OSVR/OSVR-HDK/HDK Ver. 2.0/misc/GF-S140149--Cable B  Rev_3.0.pdf

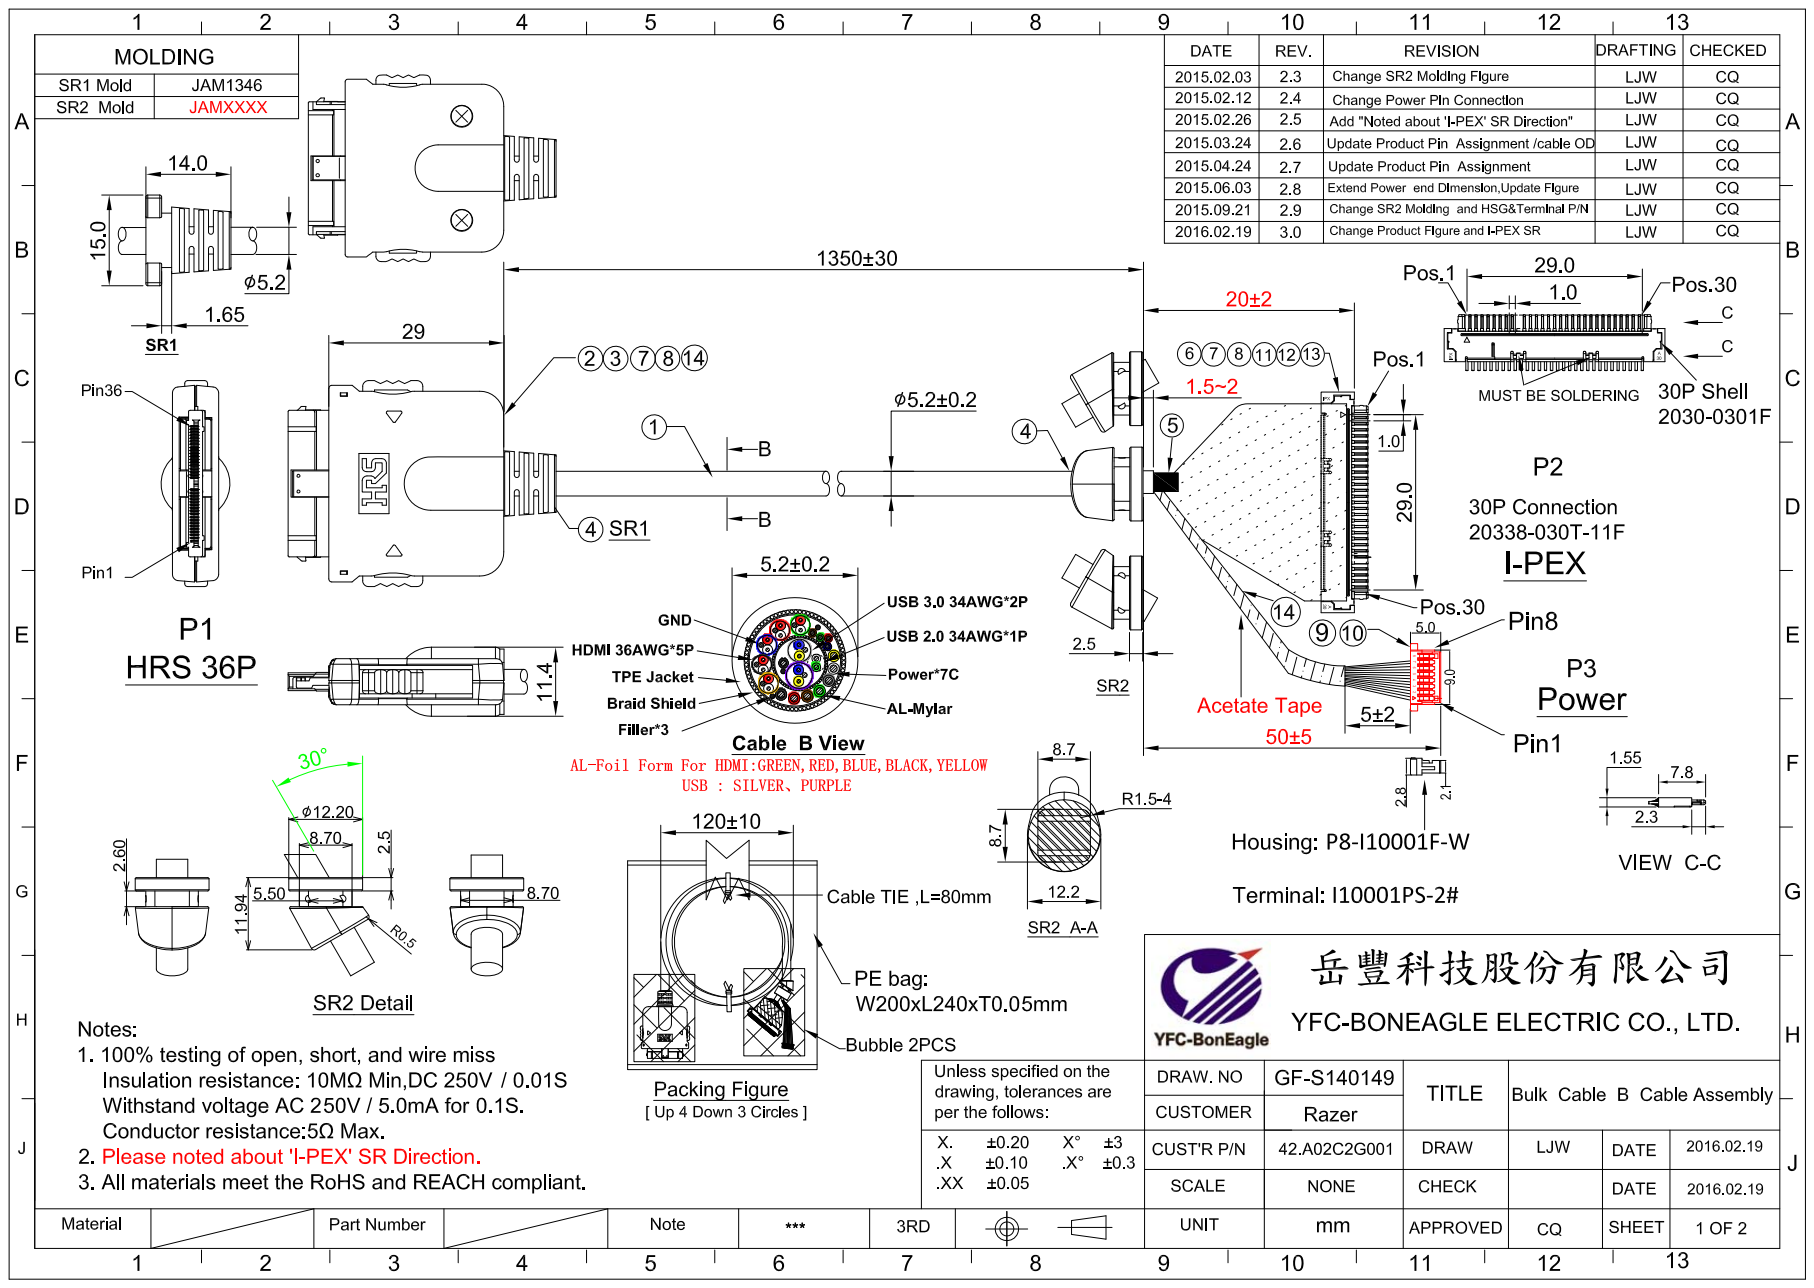
[picture p48: page 1]

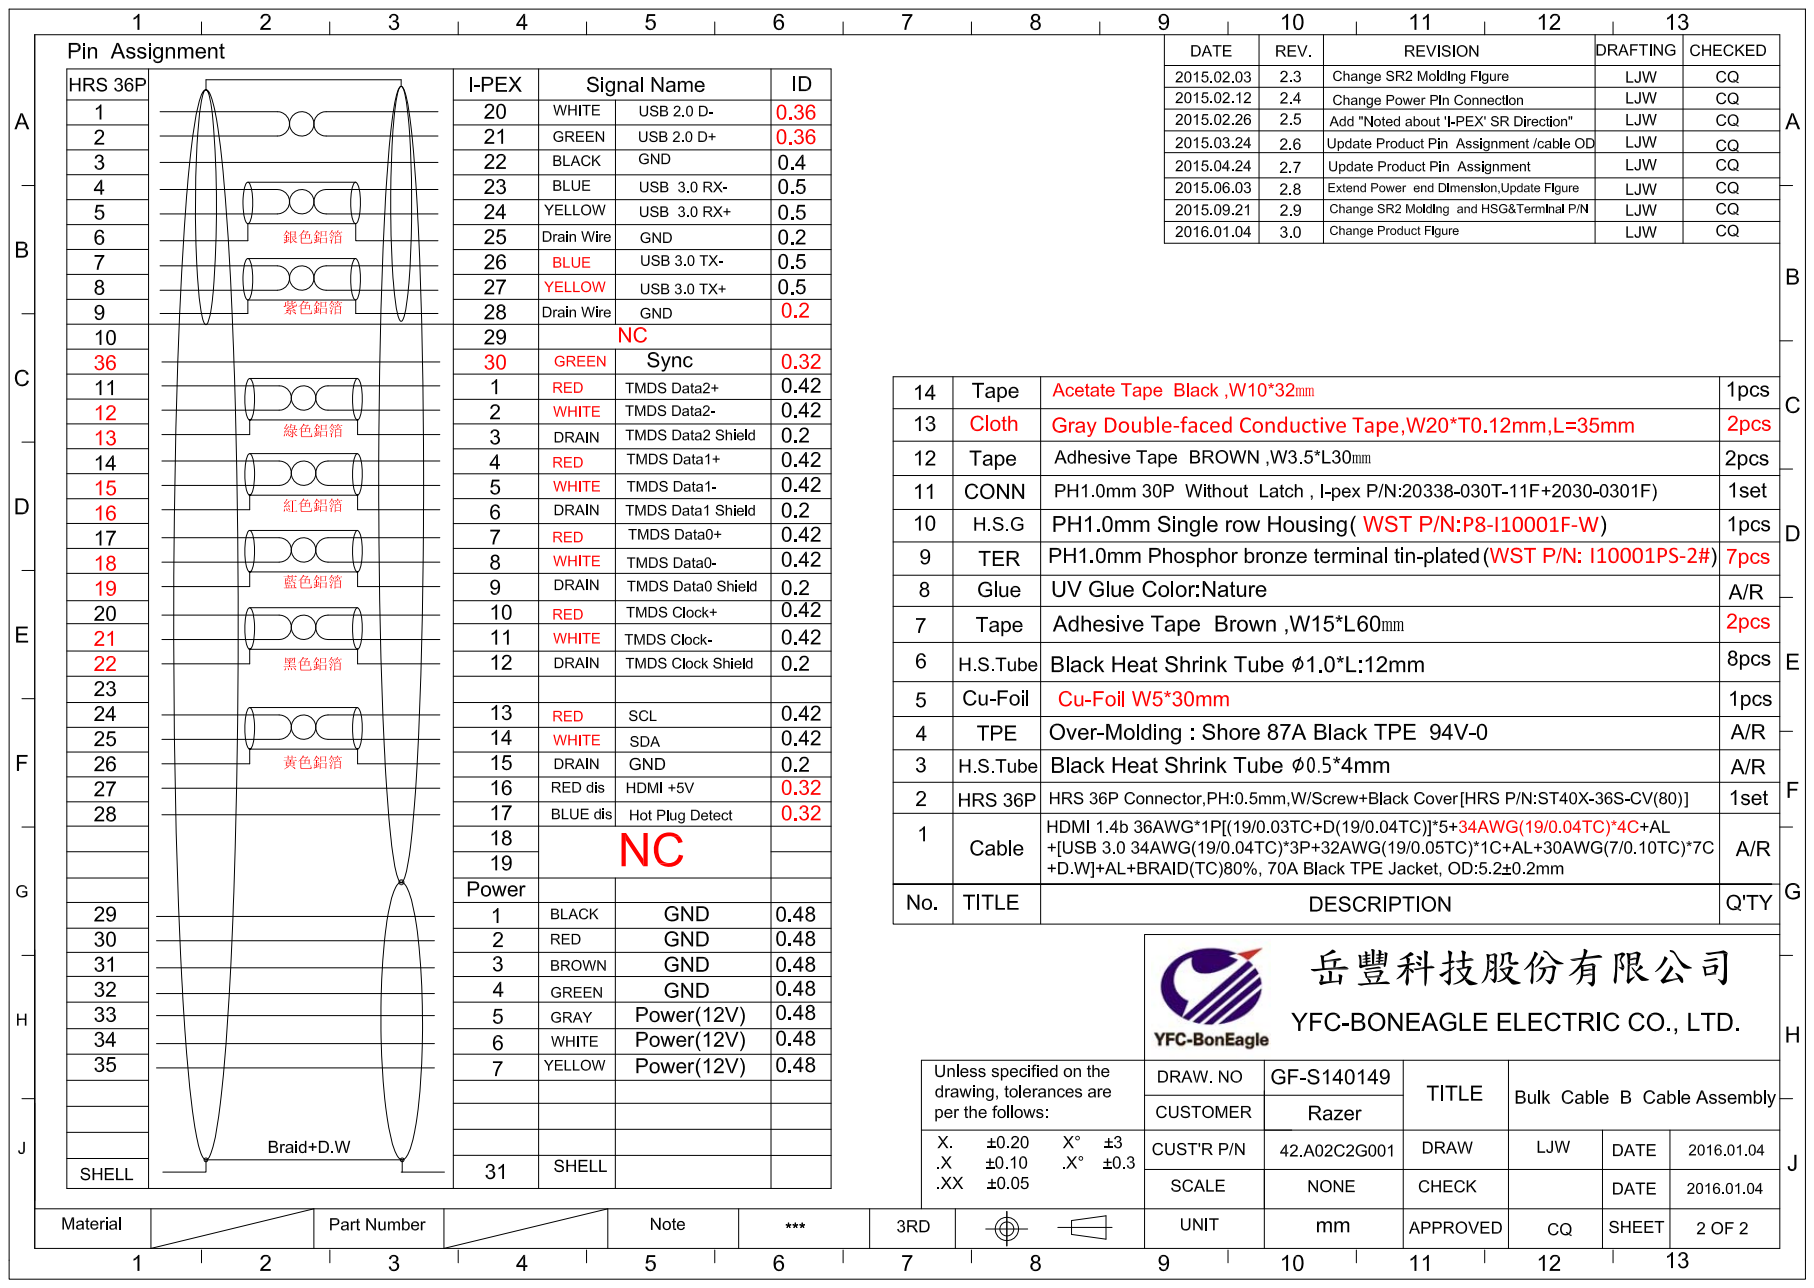
[picture p49: page 2]
