OSVR/OSVR-HDK/HDK Ver. 2.0/misc/GF-S150066--IR Cable_REV1.6.pdf

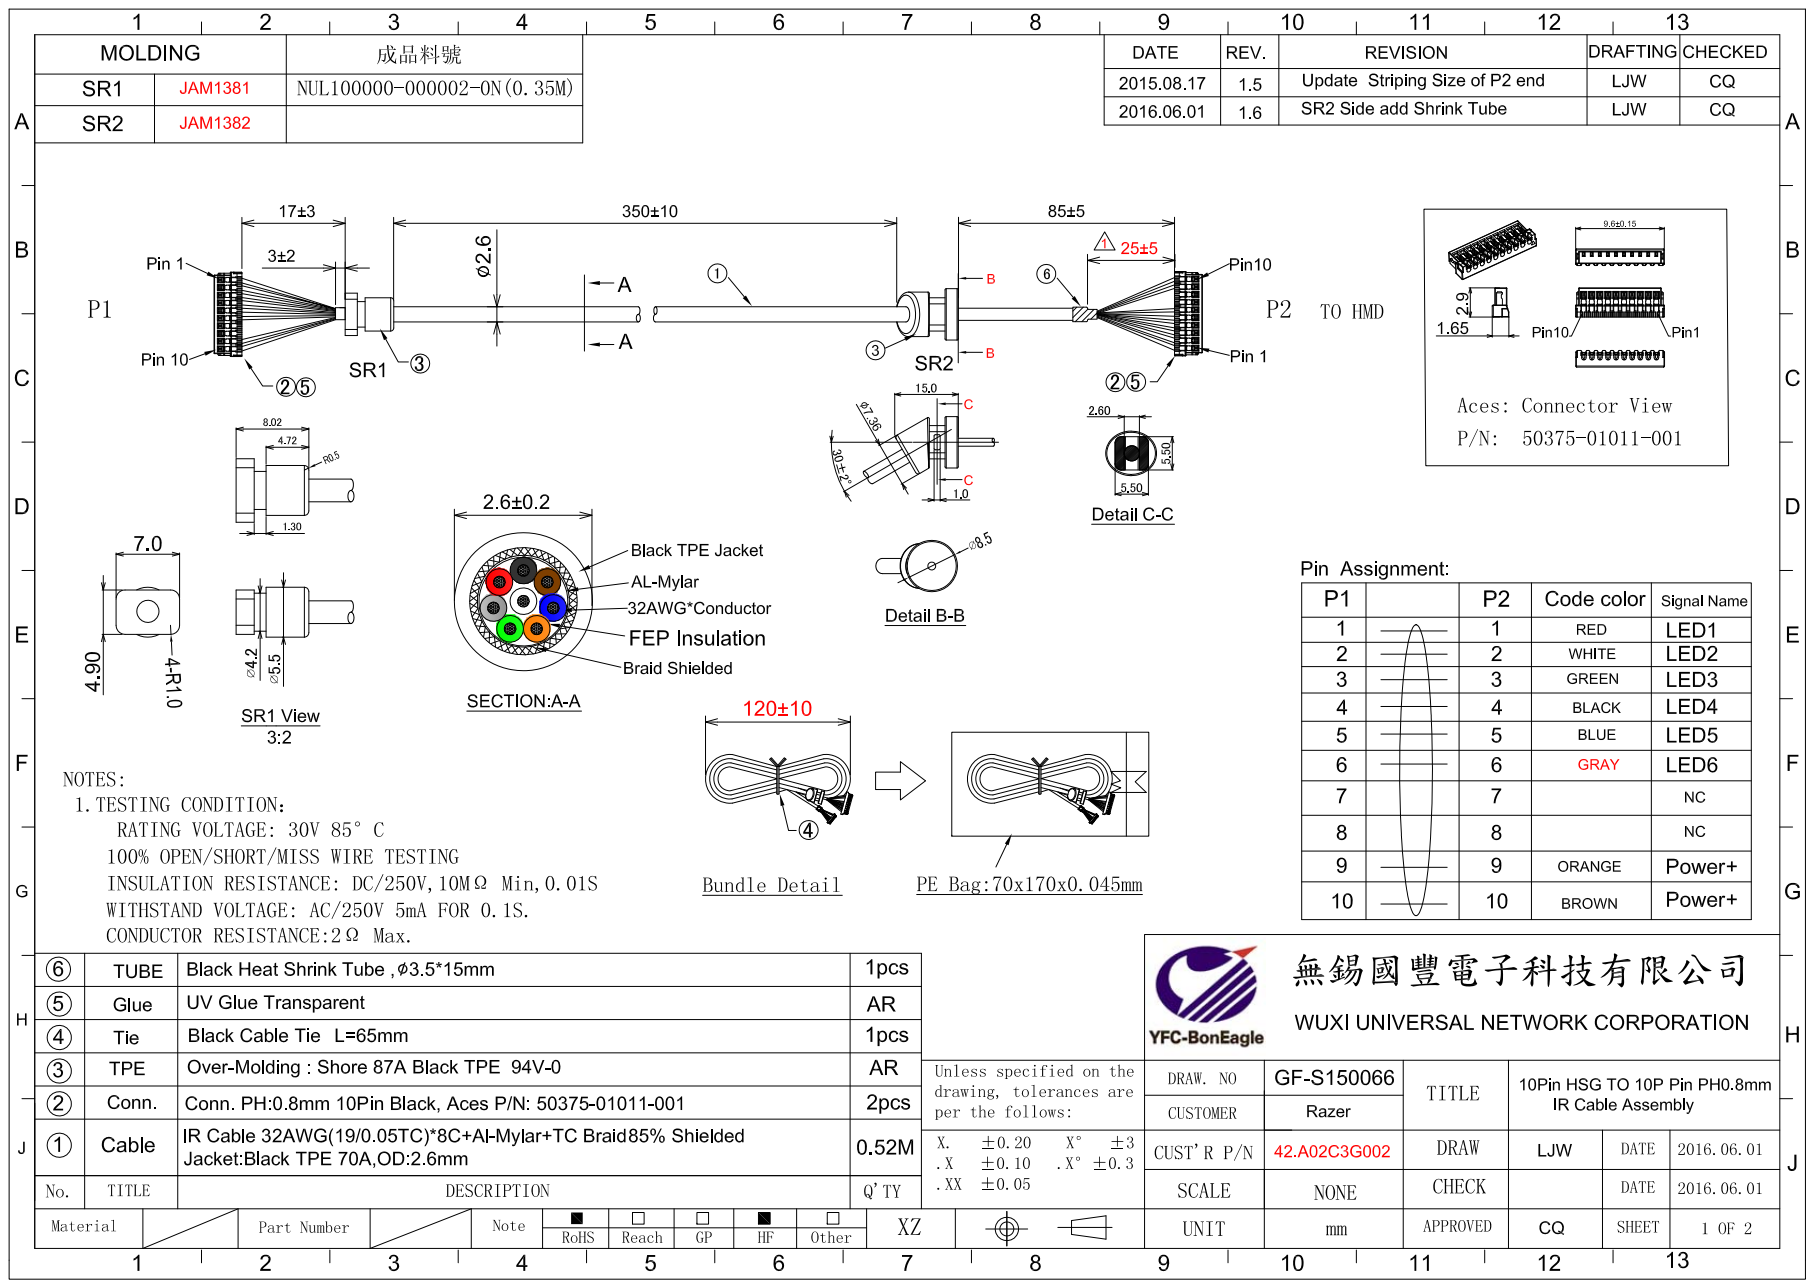
[picture p50: page 1]

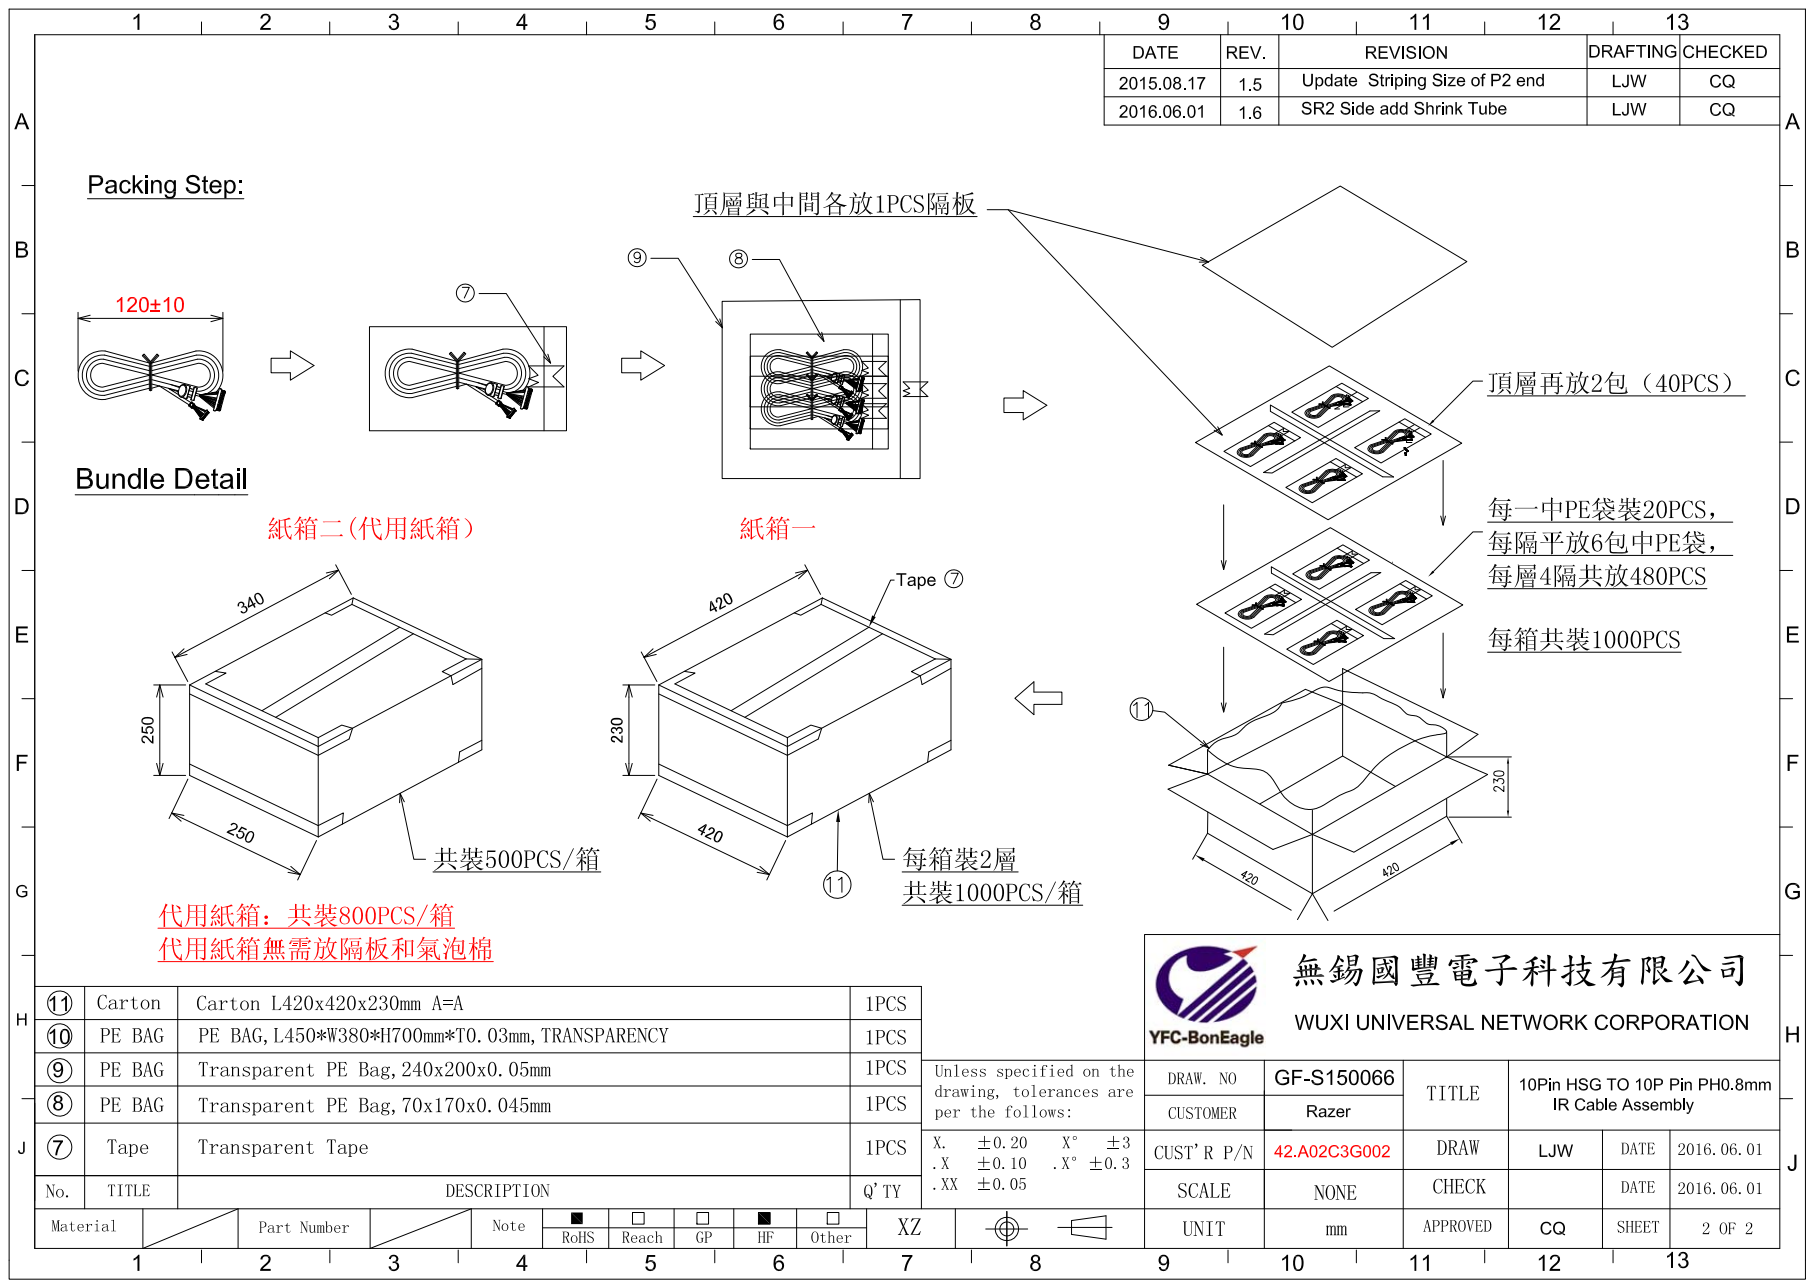
[picture p51: page 2]
