OSVR/OSVR-HDK/HDK Ver. 2.0/misc/GF-S150127---USB 2.0 AM-MICRO BM _A1.pdf

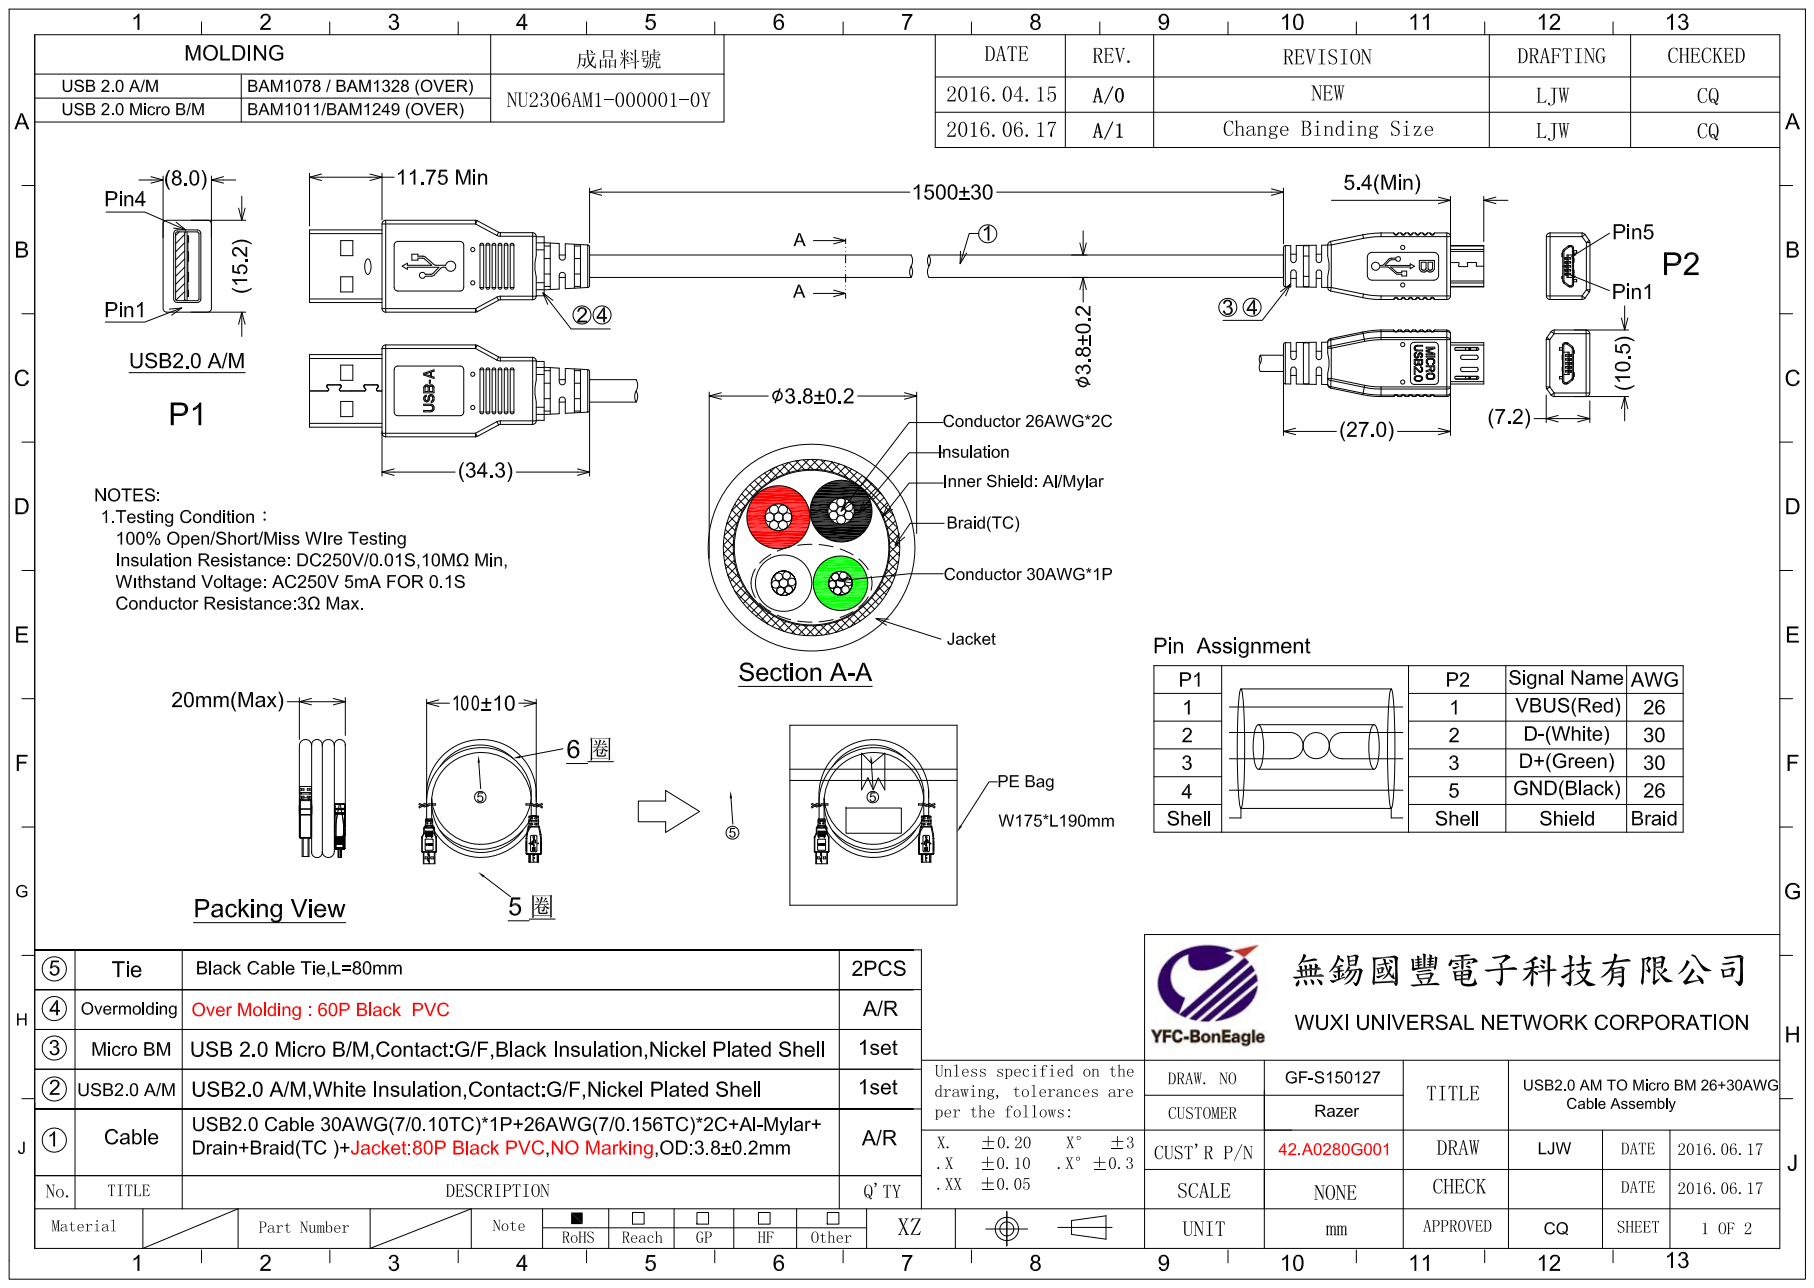
[picture p52: page 1]

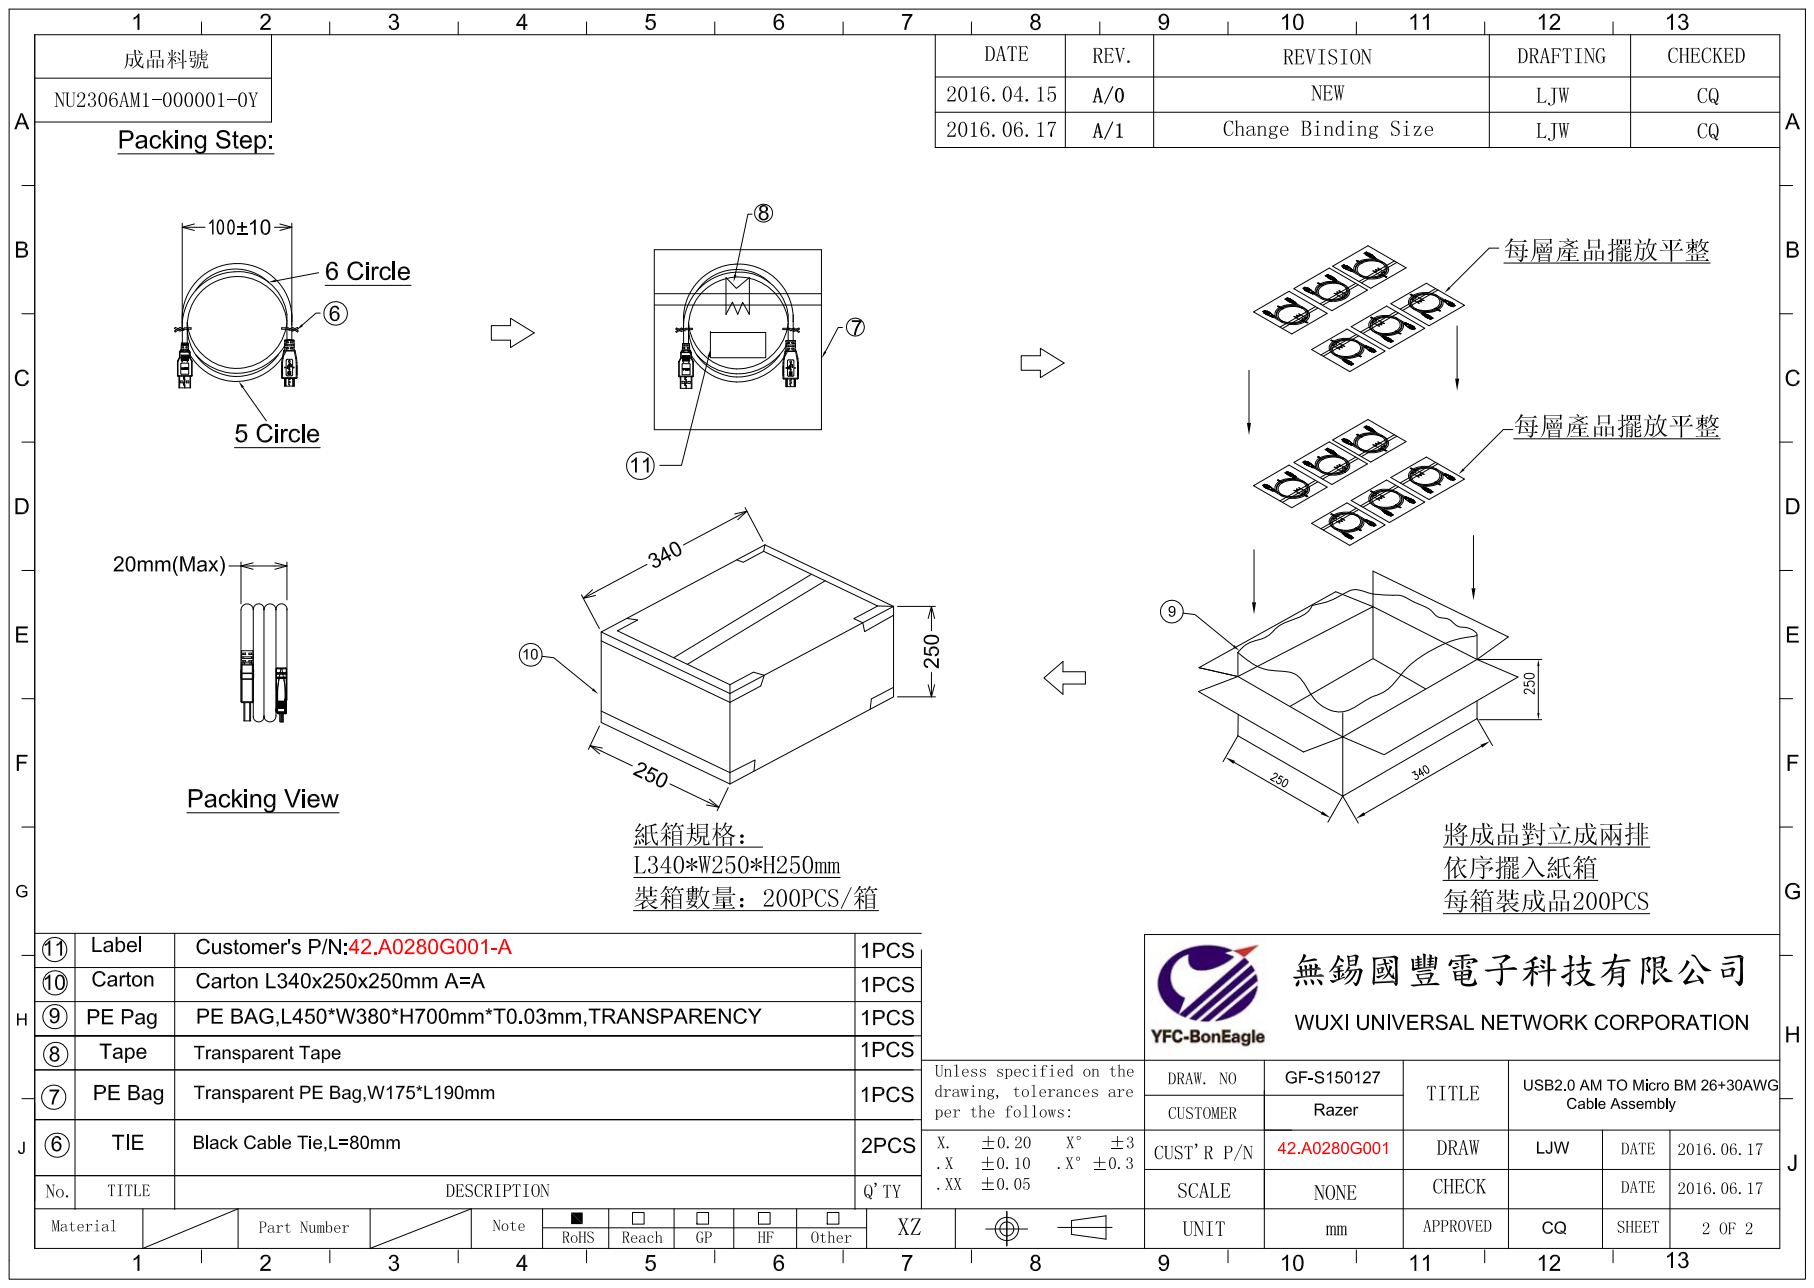
[picture p53: page 2]
