OSVR/OSVR-HDK/HDK Ver. 2.0/misc/GF-S150128---CABLE  D Rev_1.4 20150721.pdf

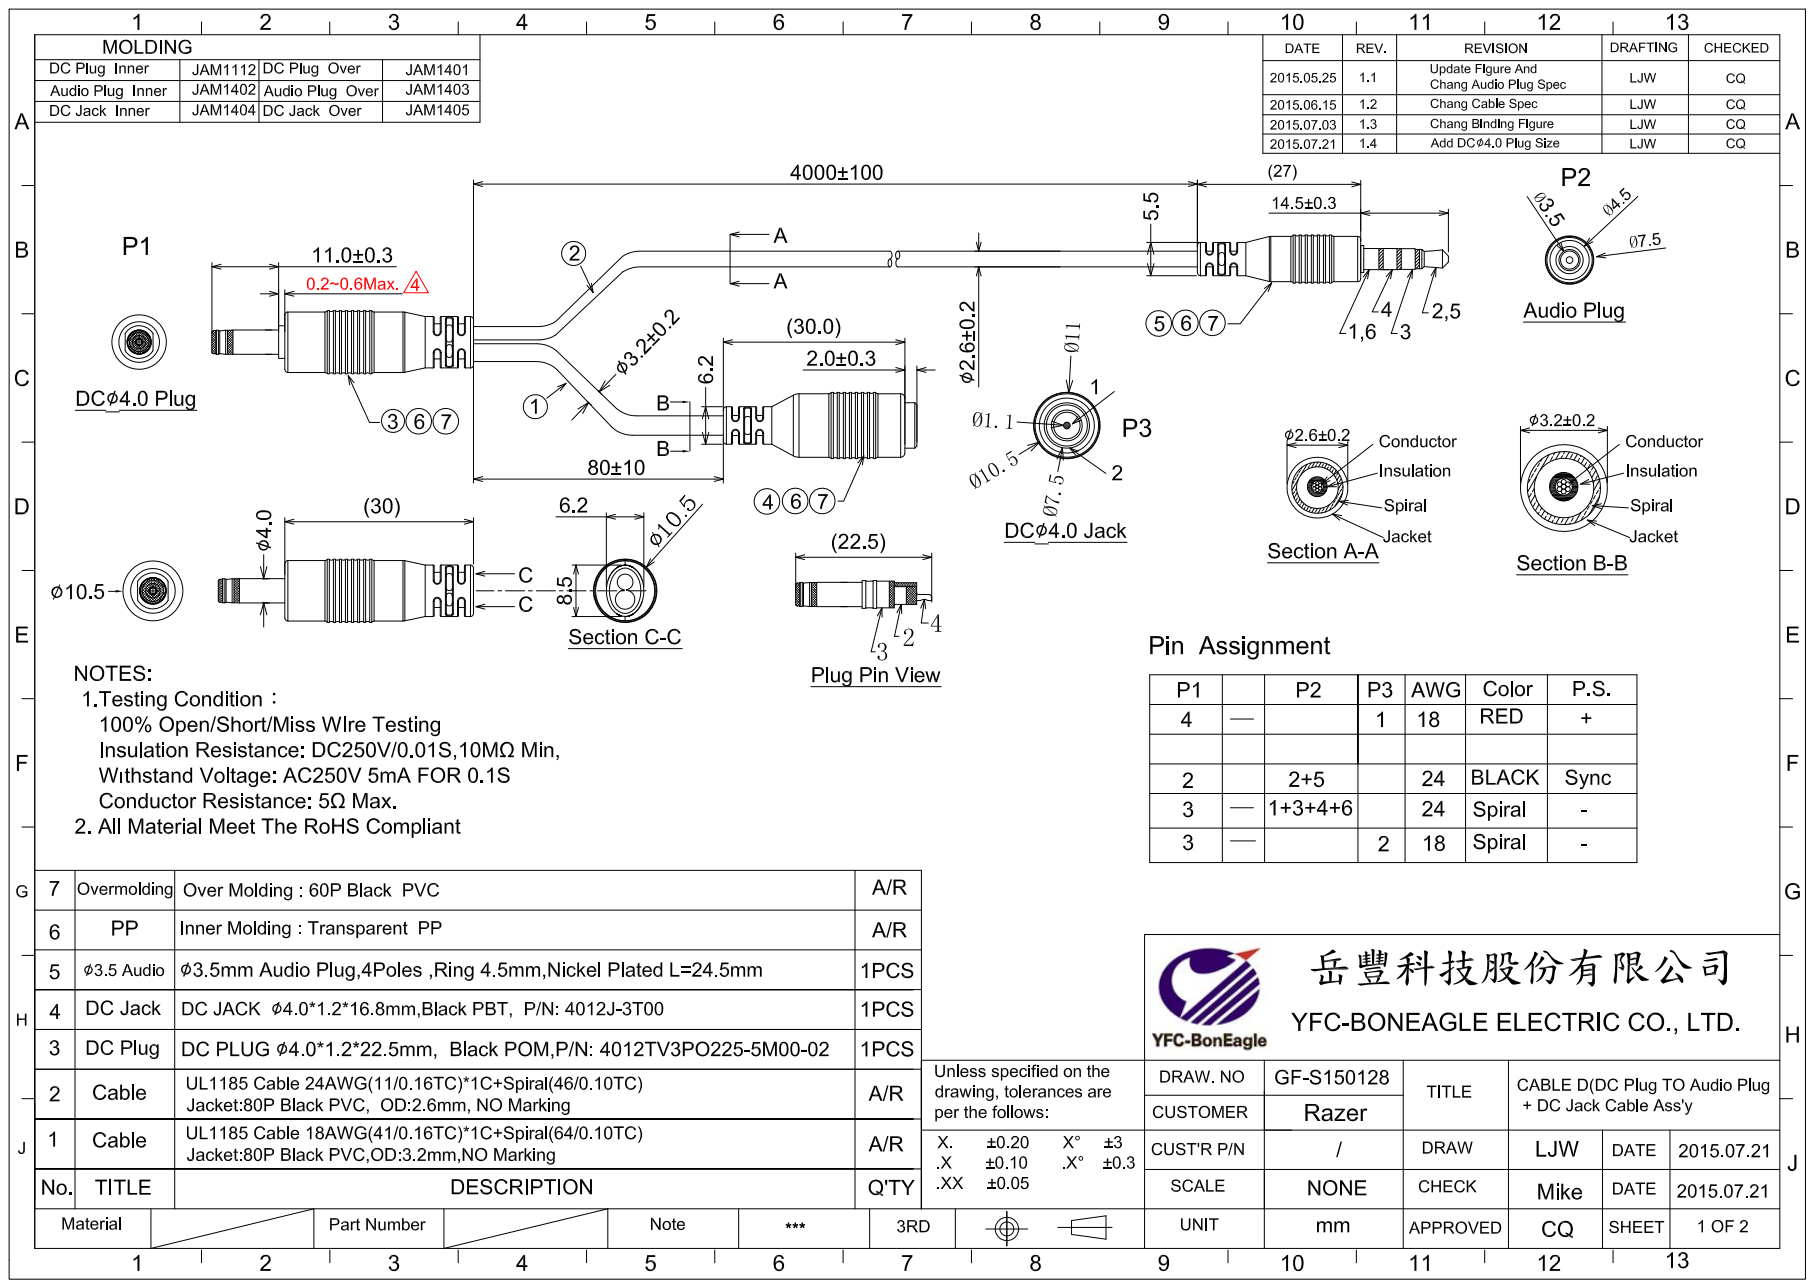
[picture p54: page 1]

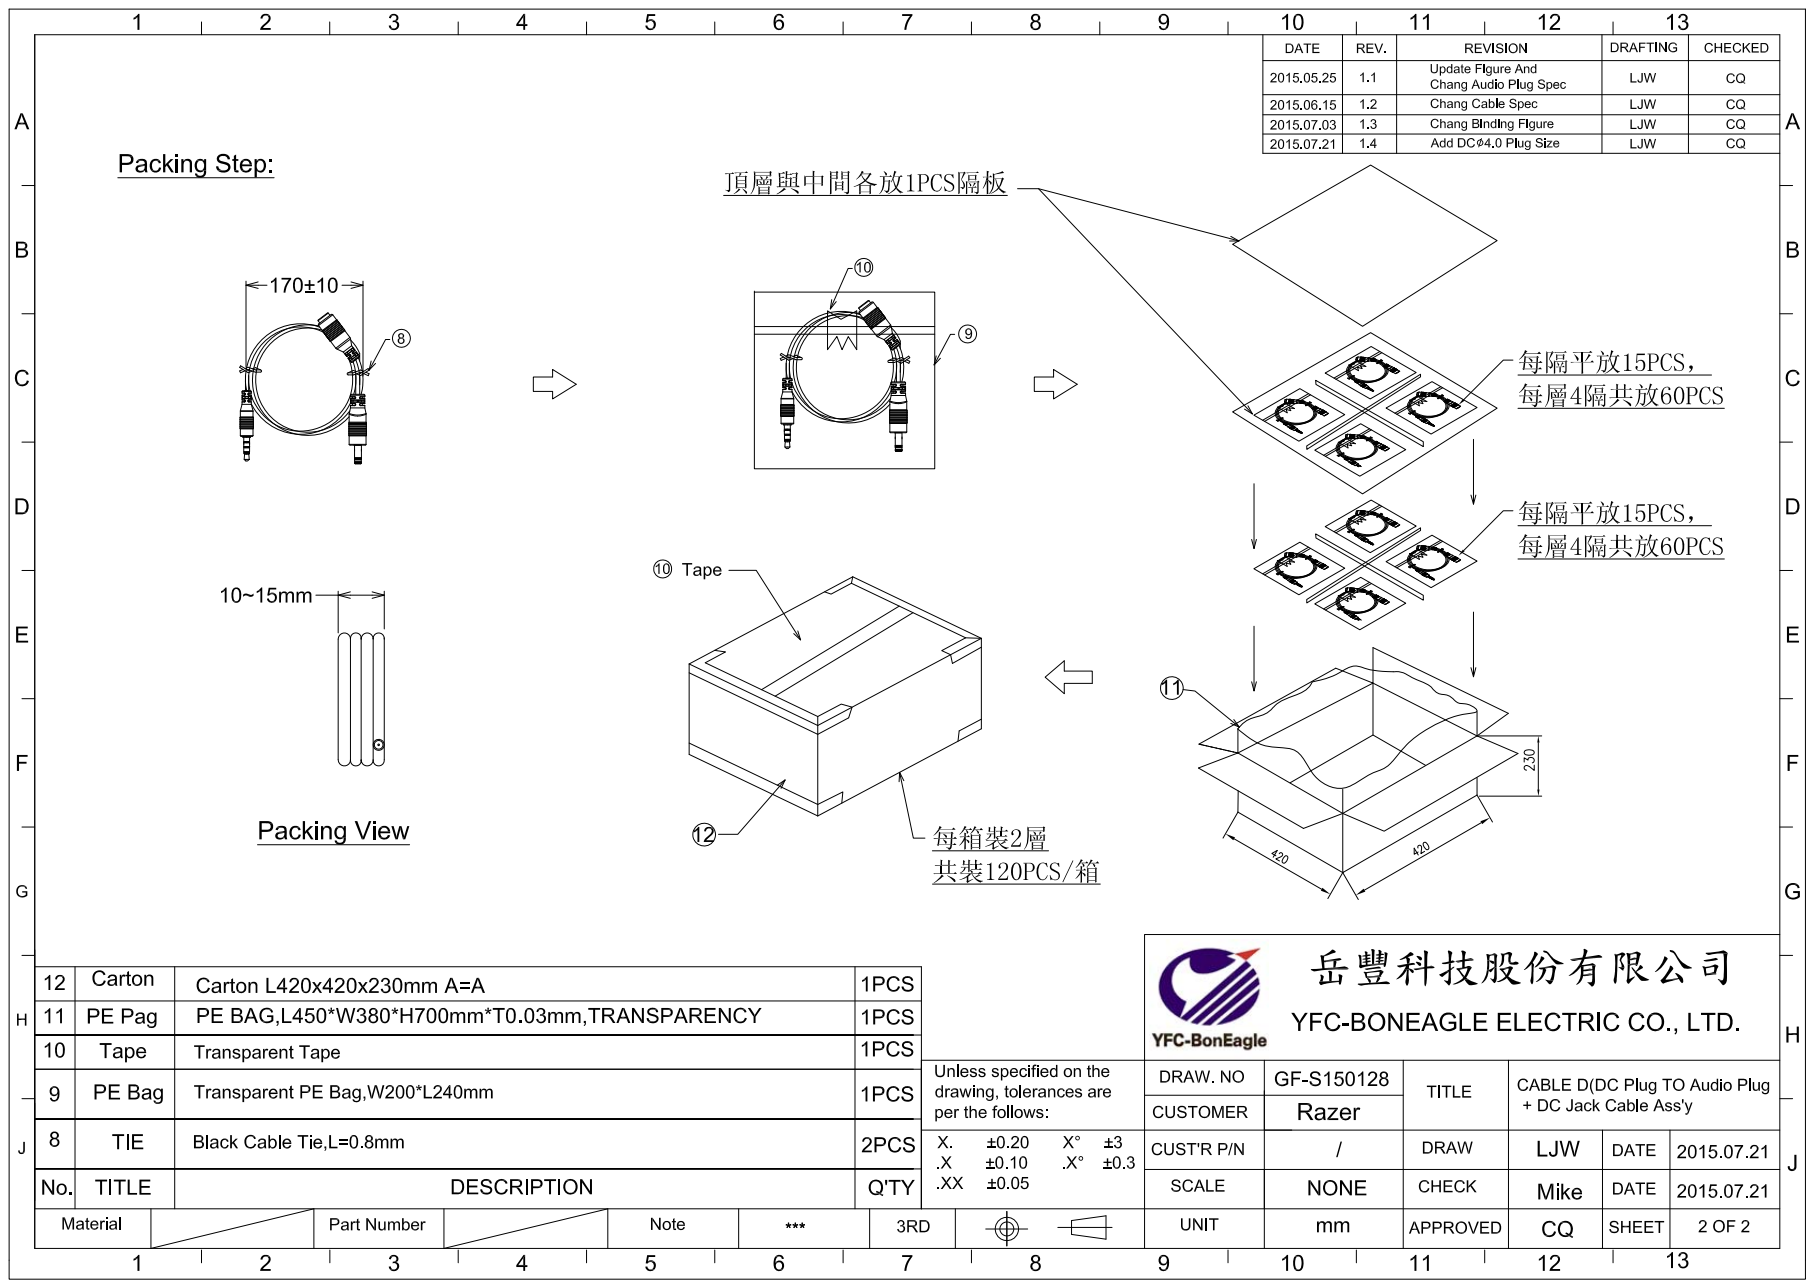
[picture p55: page 2]
