OSVR/OSVR-HDK/HDK Ver 1.2/electricals/schematics/dvt ir_fpc_fc_05112.pdf

# FPC-Front Cover Board 1/2

# TO FPC-U Board

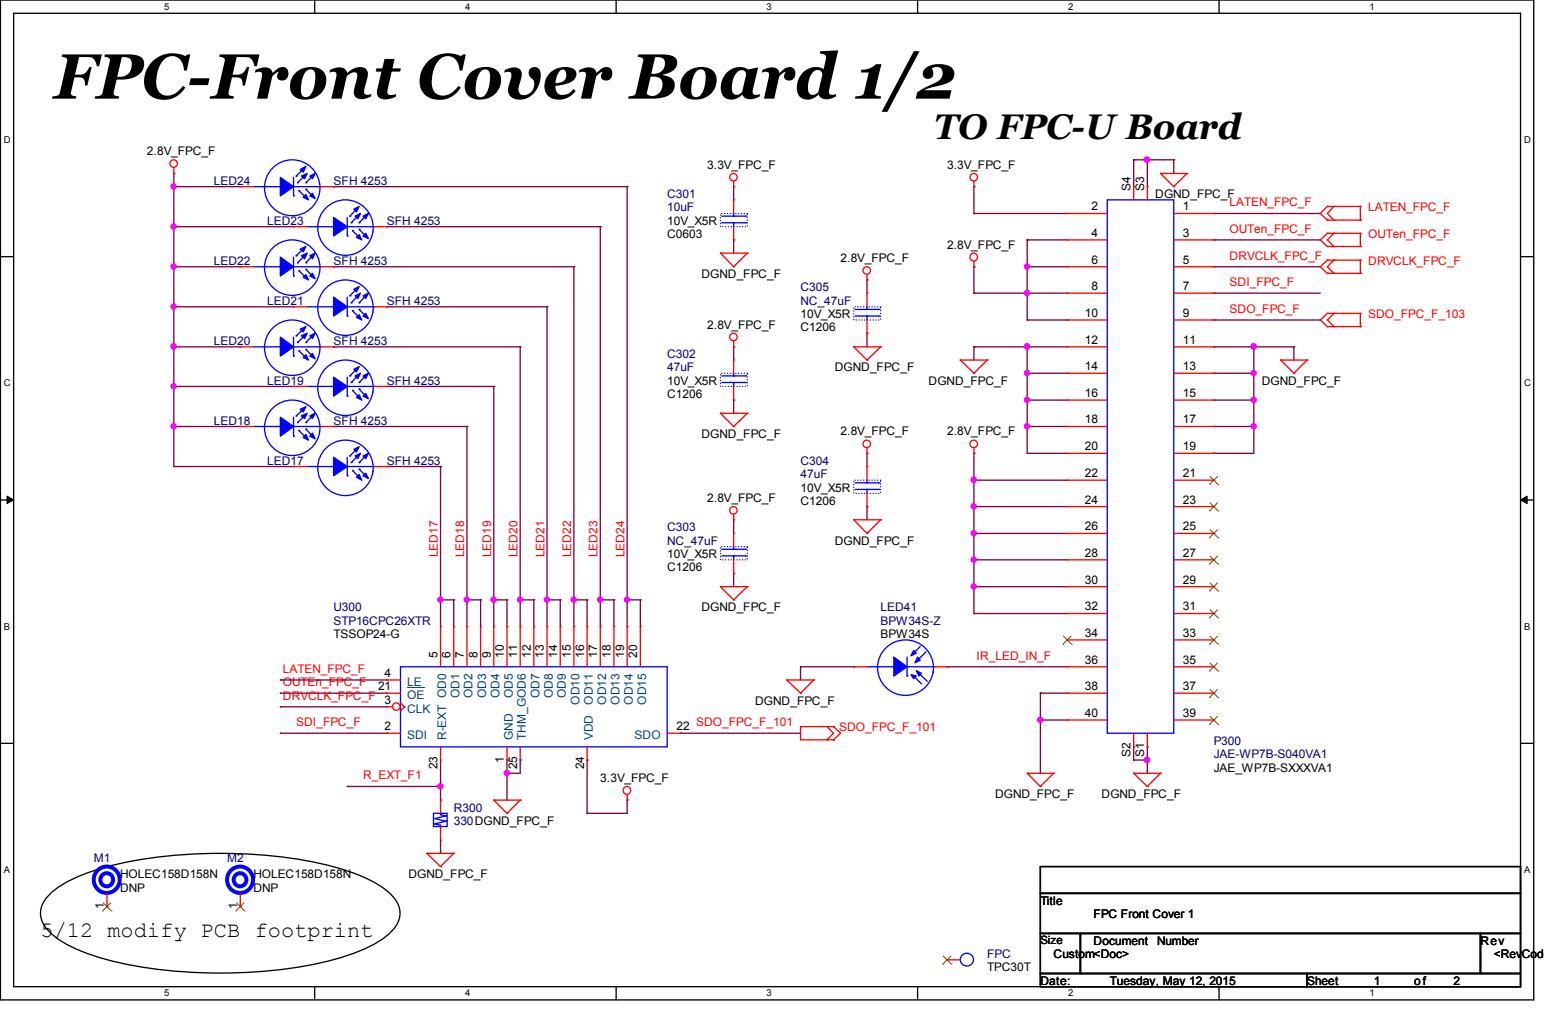
[picture p56: page 1]

# FPC-Front Cover Board 2/2

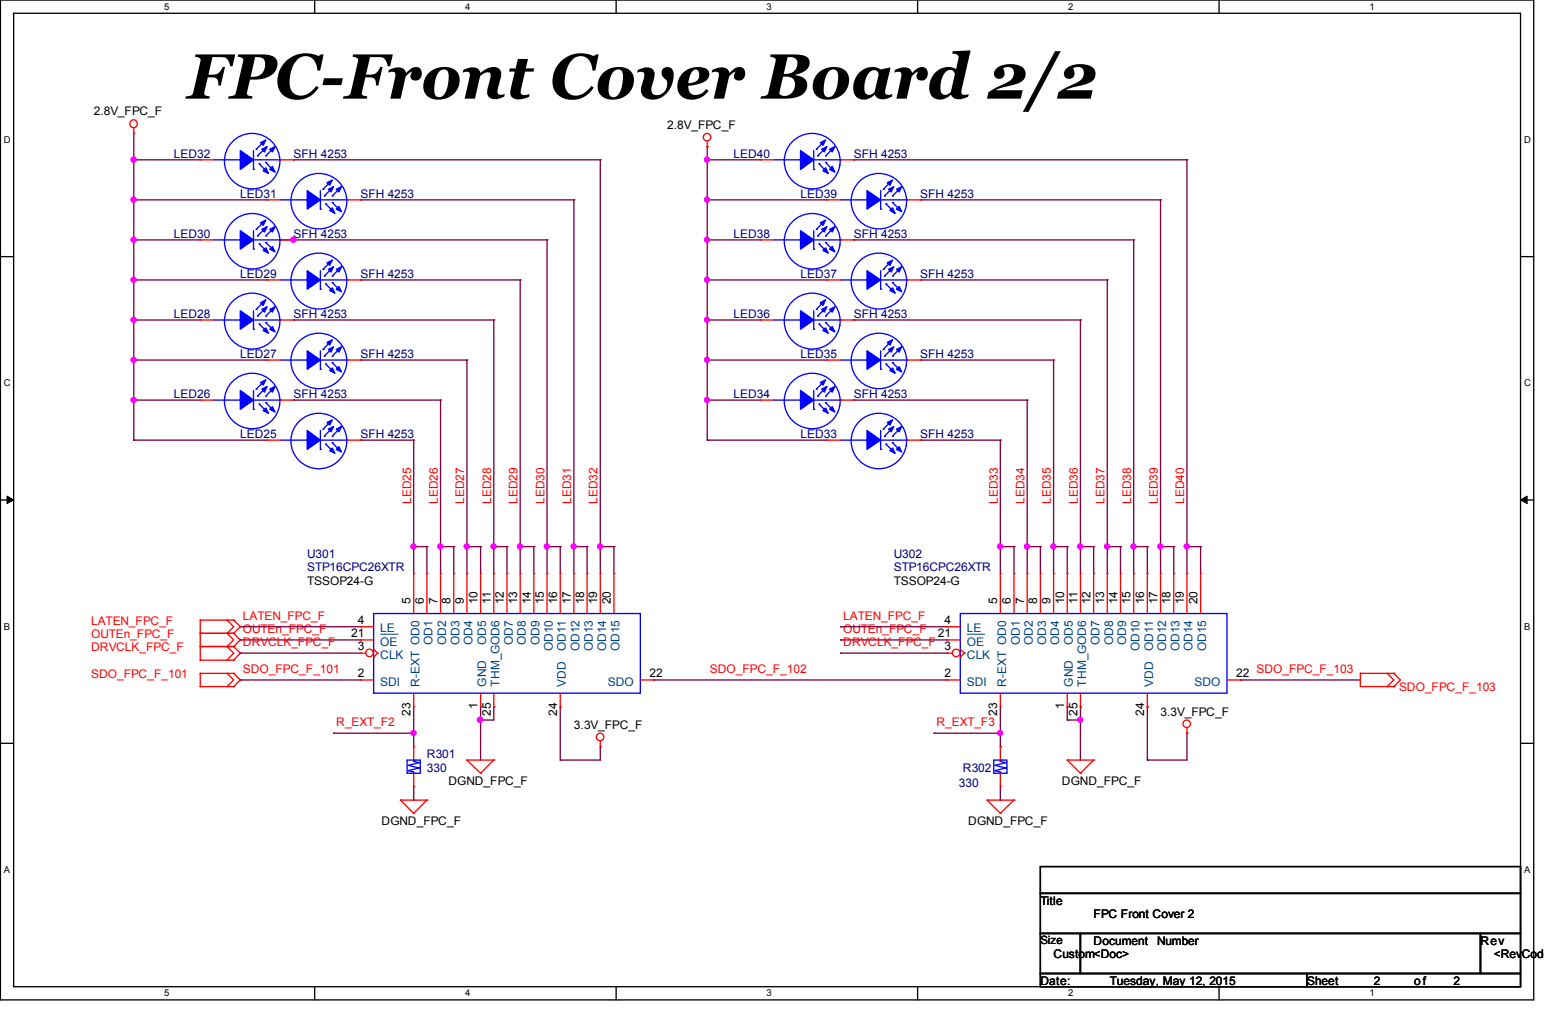
[picture p57: page 2]
