OSVR/OSVR-HDK/HDK Ver 1.2/electricals/schematics/dvt ir_fpc_u_0511.pdf

TO IR Board | TO FPC_ Front Cover Board

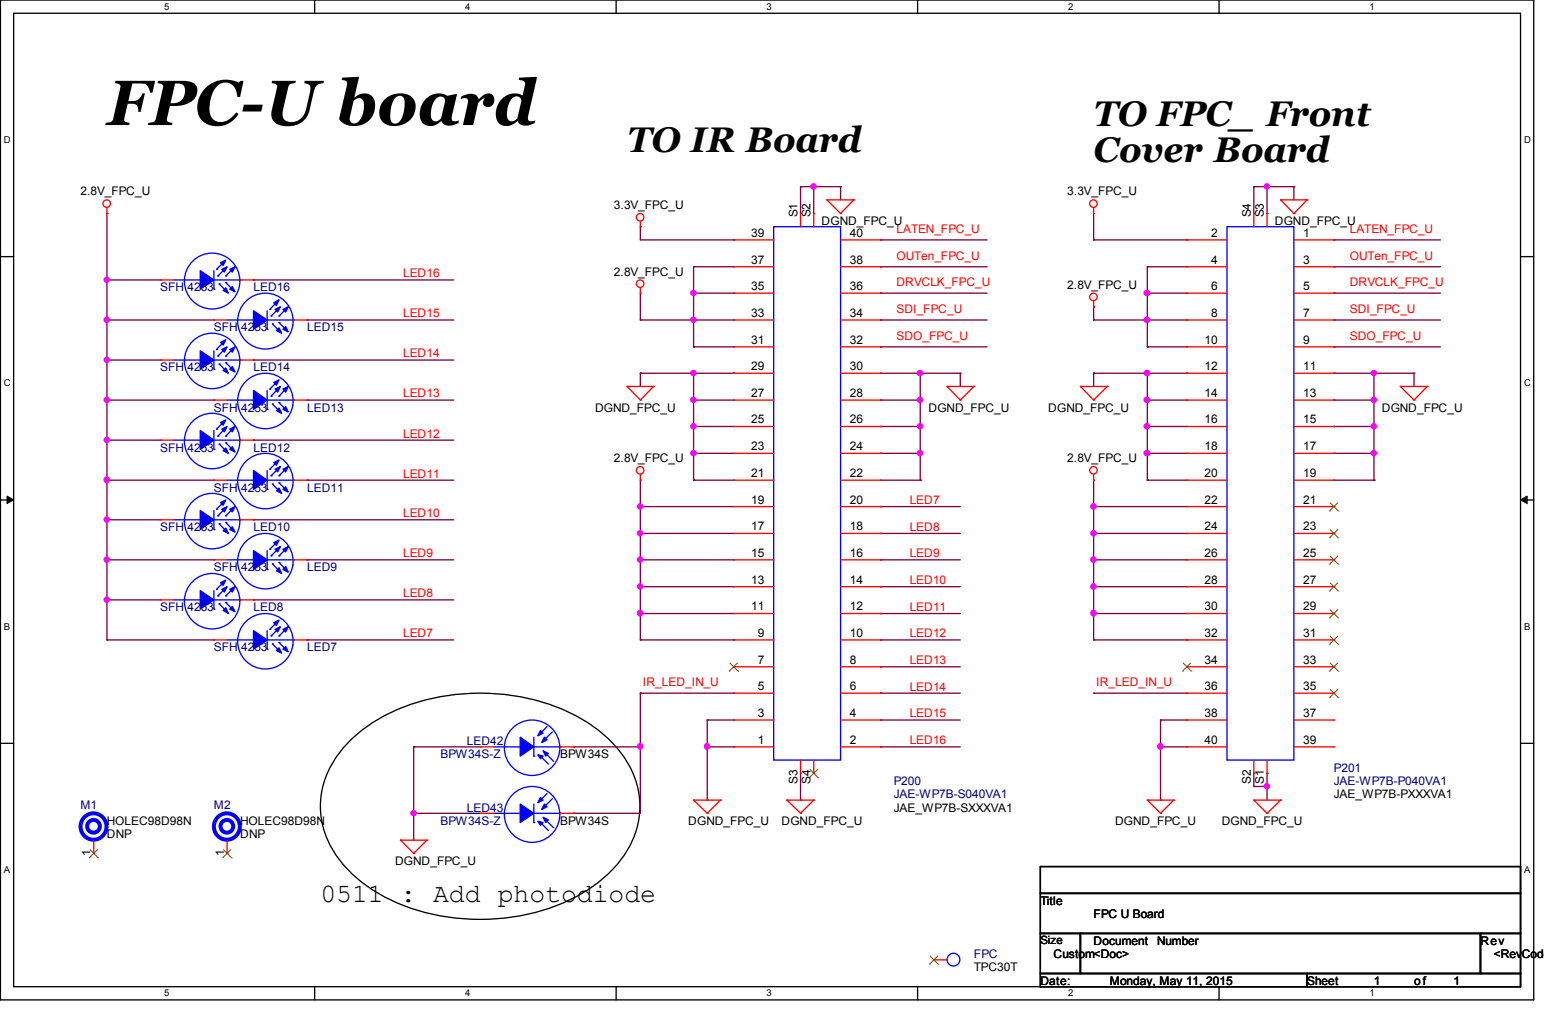
[picture p58: page 1]
