OSVR/OSVR-HDK/HDK Ver 1.2/electricals/schematics/DVT_RIGID_PCBWLEDS_UPDATE1_0513.pdf

# TO FPC_U Board TO HMD Board

# IR Board 1/4

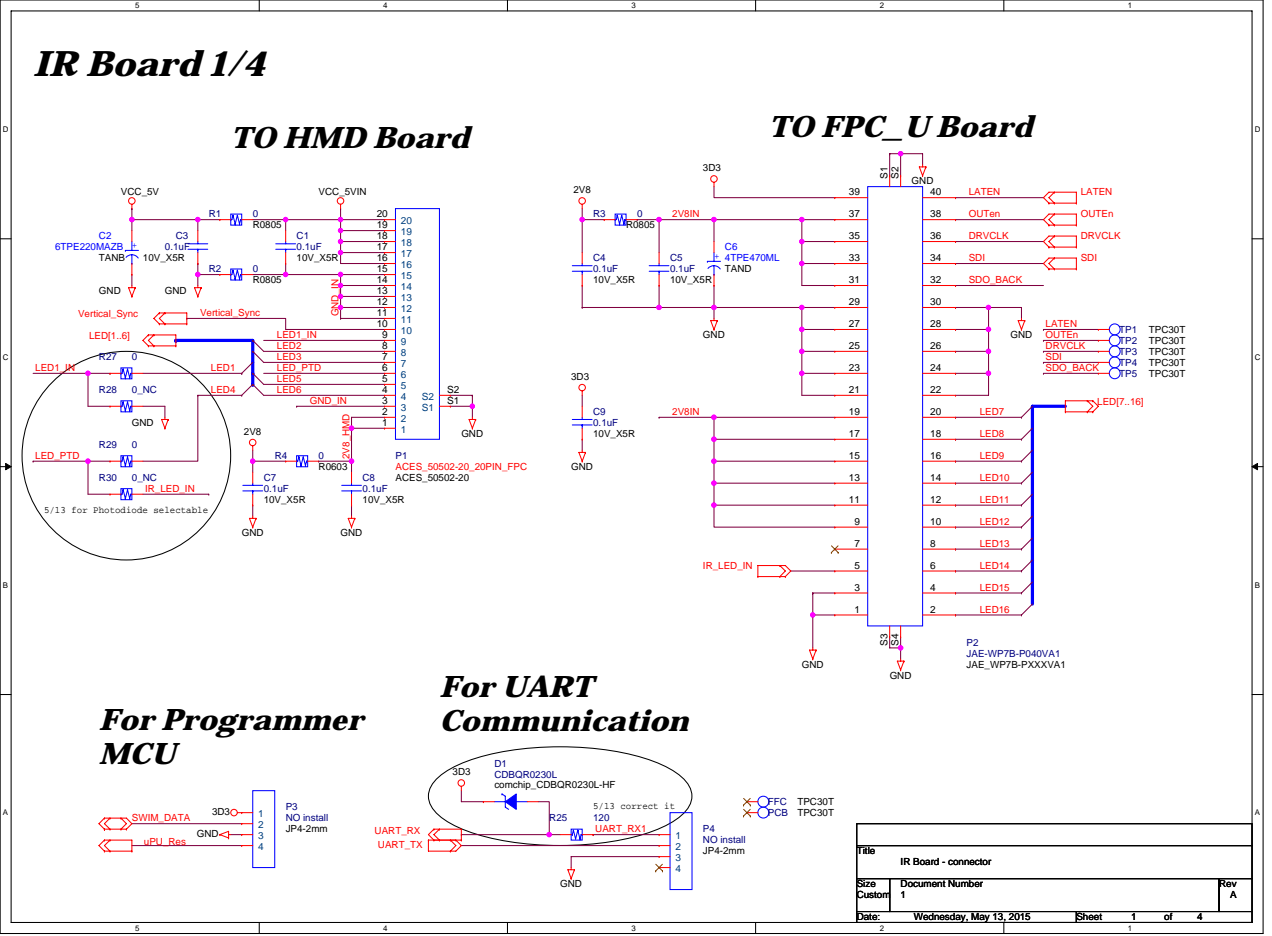
[picture p59: page 1]

17 | 18 LED8

15 | 16 LED9

13 | 14 LED10

11 | 12 LED11

9 | 10 LED12

Size Size Size Custom Custom Custom | Document Number Document Number Document Number 1 1 1 | Rev Rev Rev A A A

Date: Wednesday, May 13, 2015 Wednesday, May 13, 2015 Wednesday, May 13, 2015 | Sheet 1 1 1 of 4 4 4

# IR Board 2/4

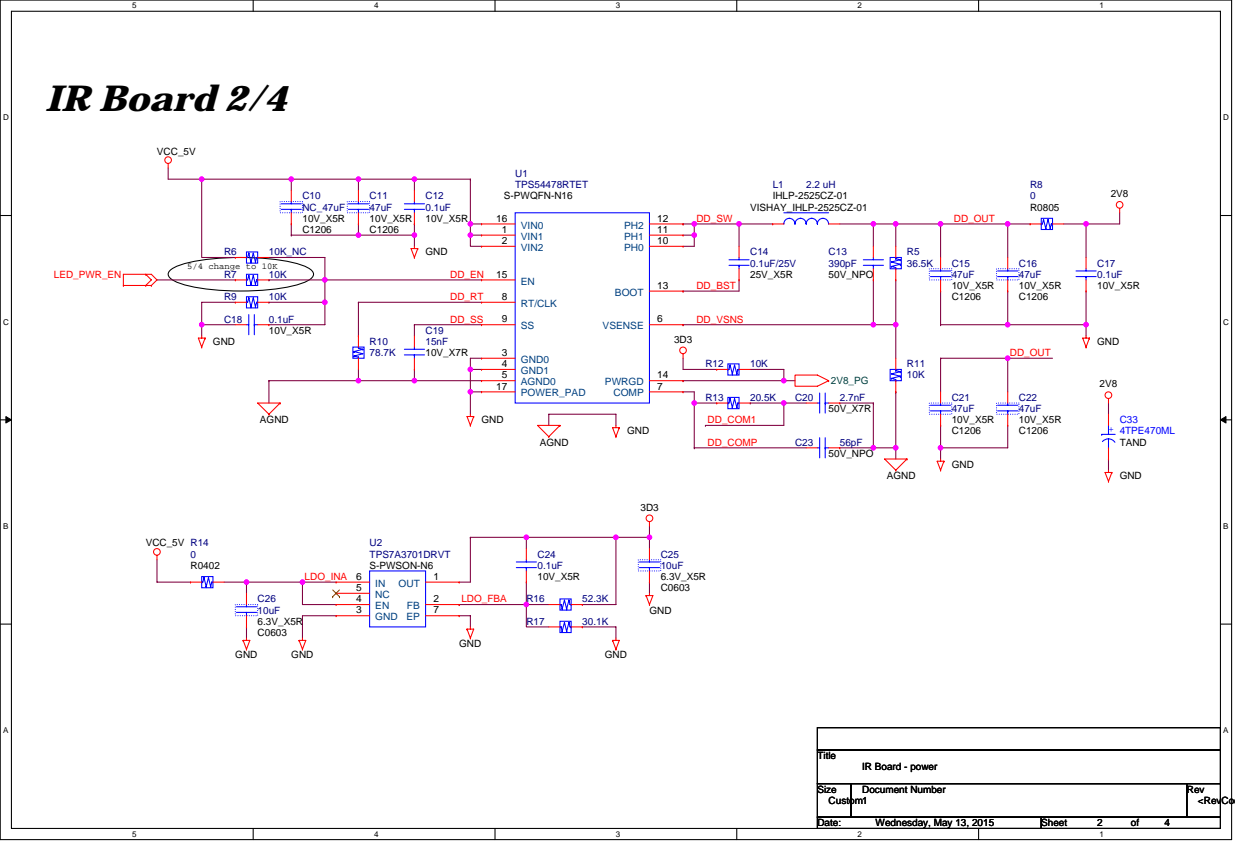
[picture p60: page 2]

Size Size Size Custom Custom Custom | Document Number Document Number Document Number | Rev Rev Rev

Wednesday, May 13, 2015 Wednesday, May 13, 2015 Wednesday, May 13, 2015 | 2 2 2 4 4 4

# IR Board 3/4

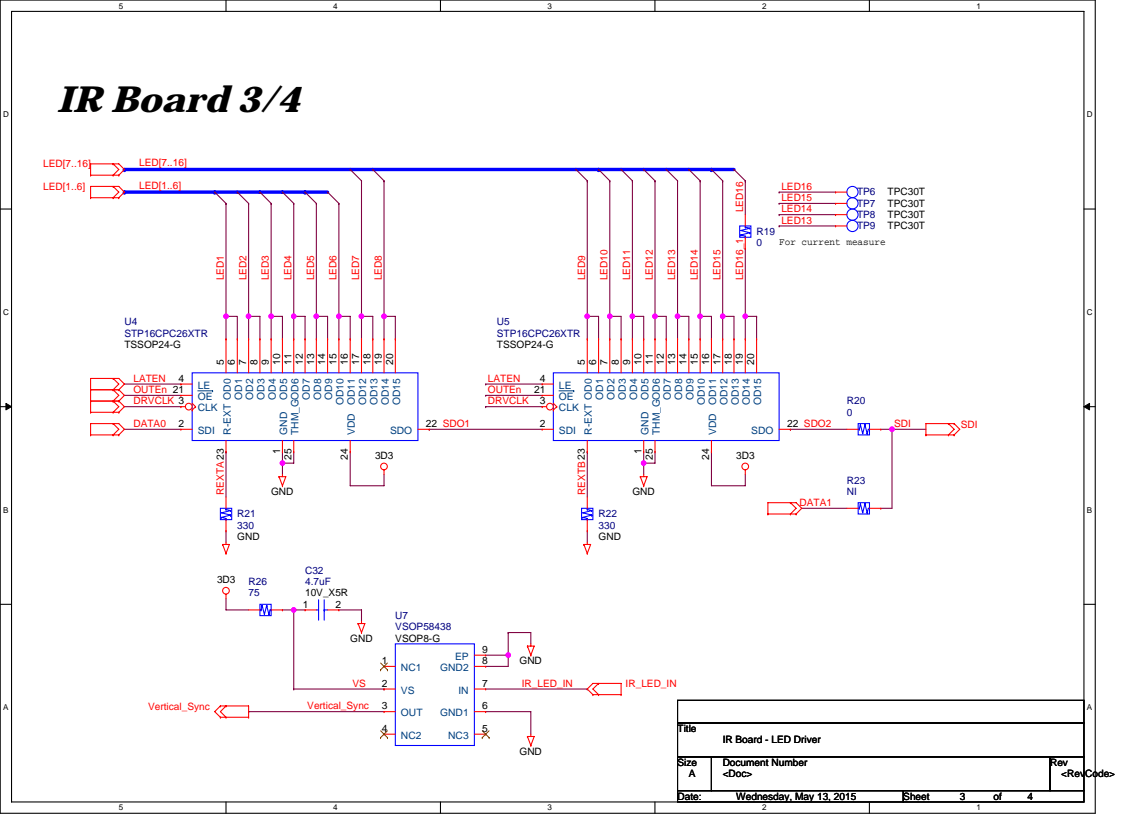
[picture p61: page 3]

IR Board - LED Driver

Size Size Size A A A | Document Number Document Number Document Number | Rev Rev Rev

Wednesday, May 13, 2015 Wednesday, May 13, 2015 Wednesday, May 13, 2015 | 3 3 3 4 4 4

# IR Board 4/4

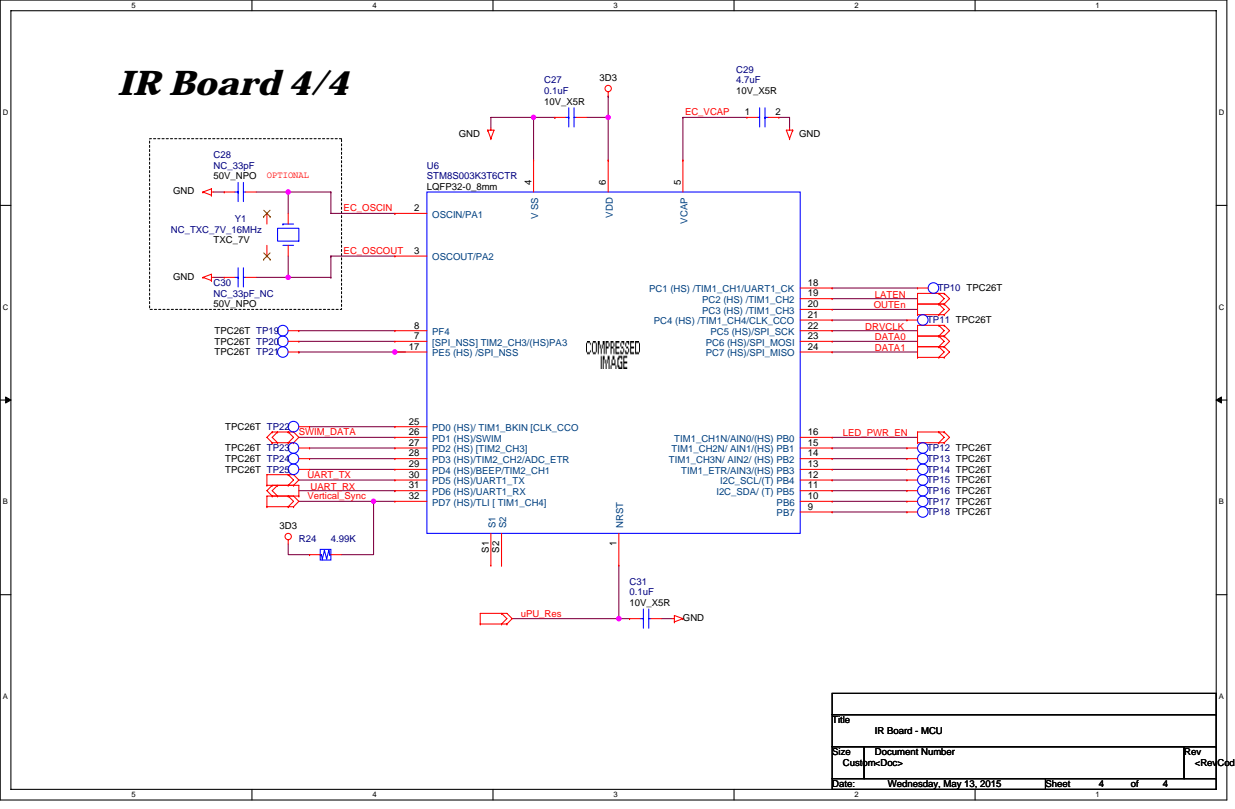
[picture p62: page 4]

Size Size Size Custom Custom Custom | Document Number Document Number Document Number | Rev Rev Rev

Date: Date: Date: Wednesday, May 13, 2015 Wednesday, May 13, 2015 Wednesday, May 13, 2015 | Sheet Sheet Sheet 4 4 4 of of of 4 4 4
