OSVR/OSVR-HDK/HDK Ver 1.2/electricals/schematics/DVT_RIGID_PCBWLEDS_UPDATE1_Phot_0524.pdf

# TO FPC_U Board TO HMD Board

# IR Board 1/4

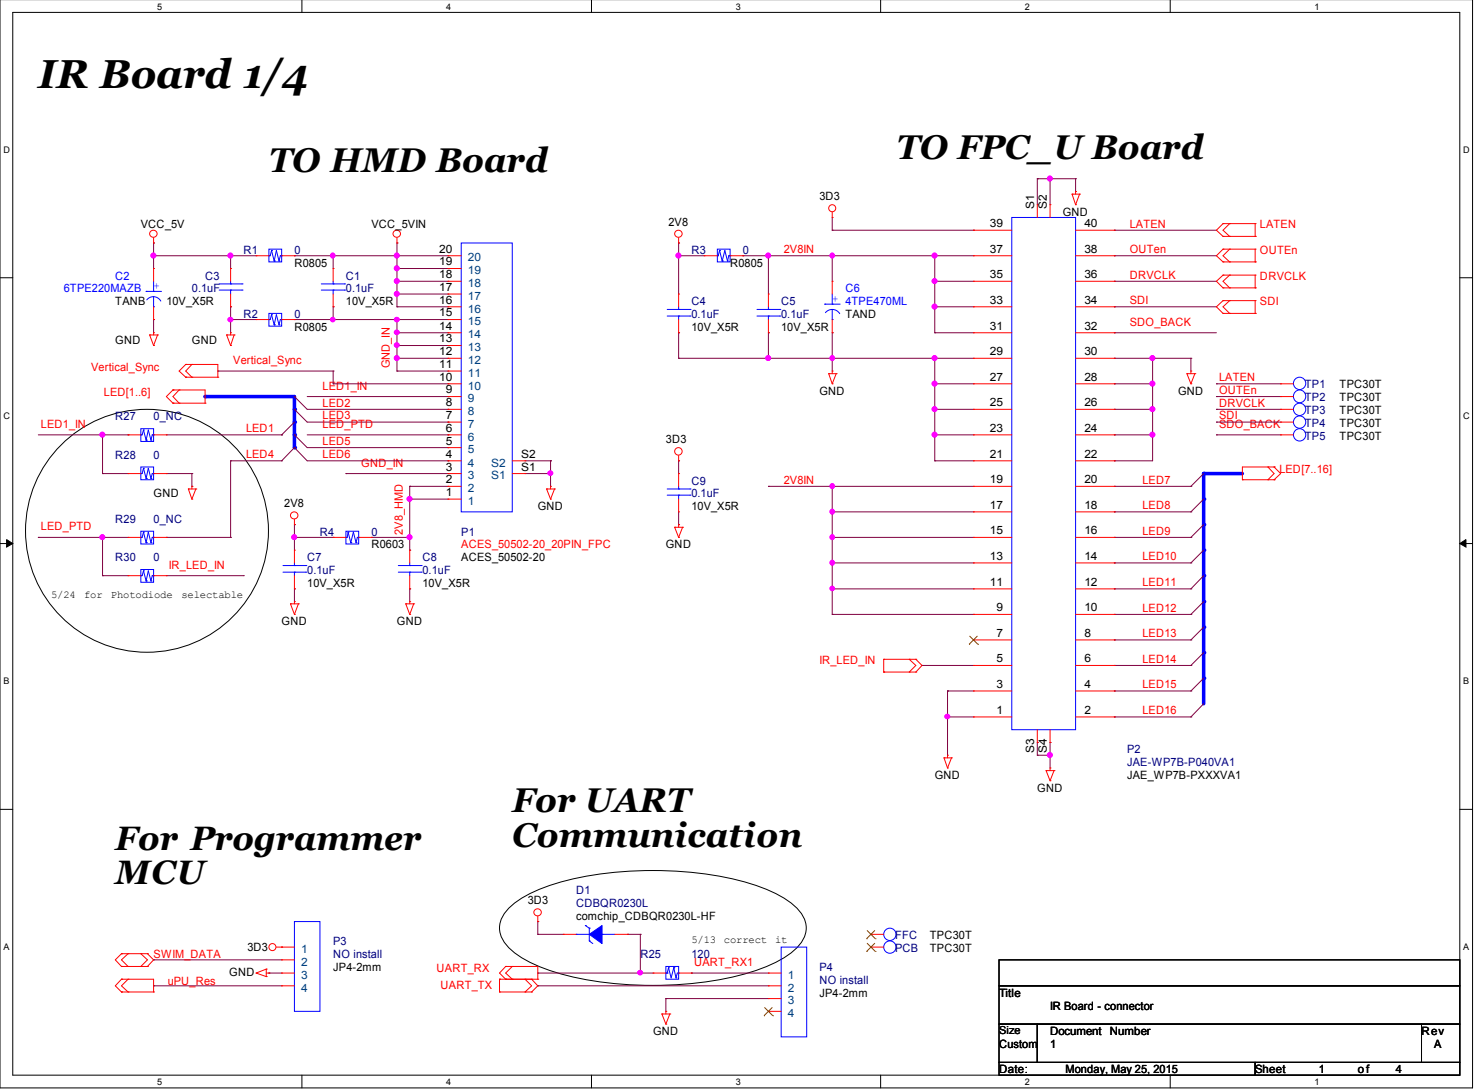
[picture p63: page 1]

# IR Board 2/4

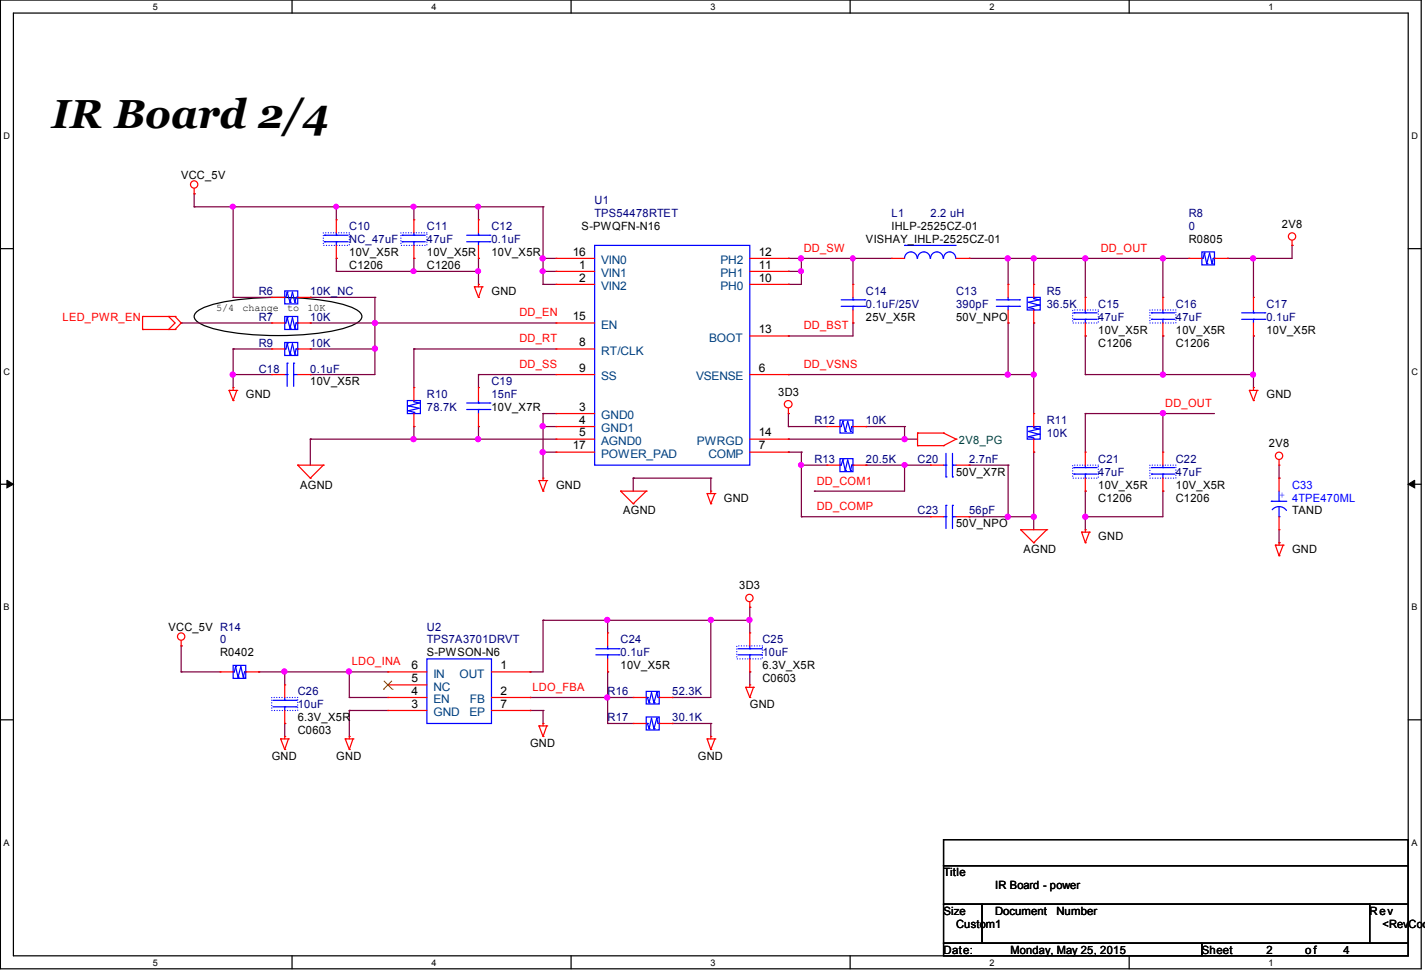
[picture p64: page 2]

# IR Board 3/4

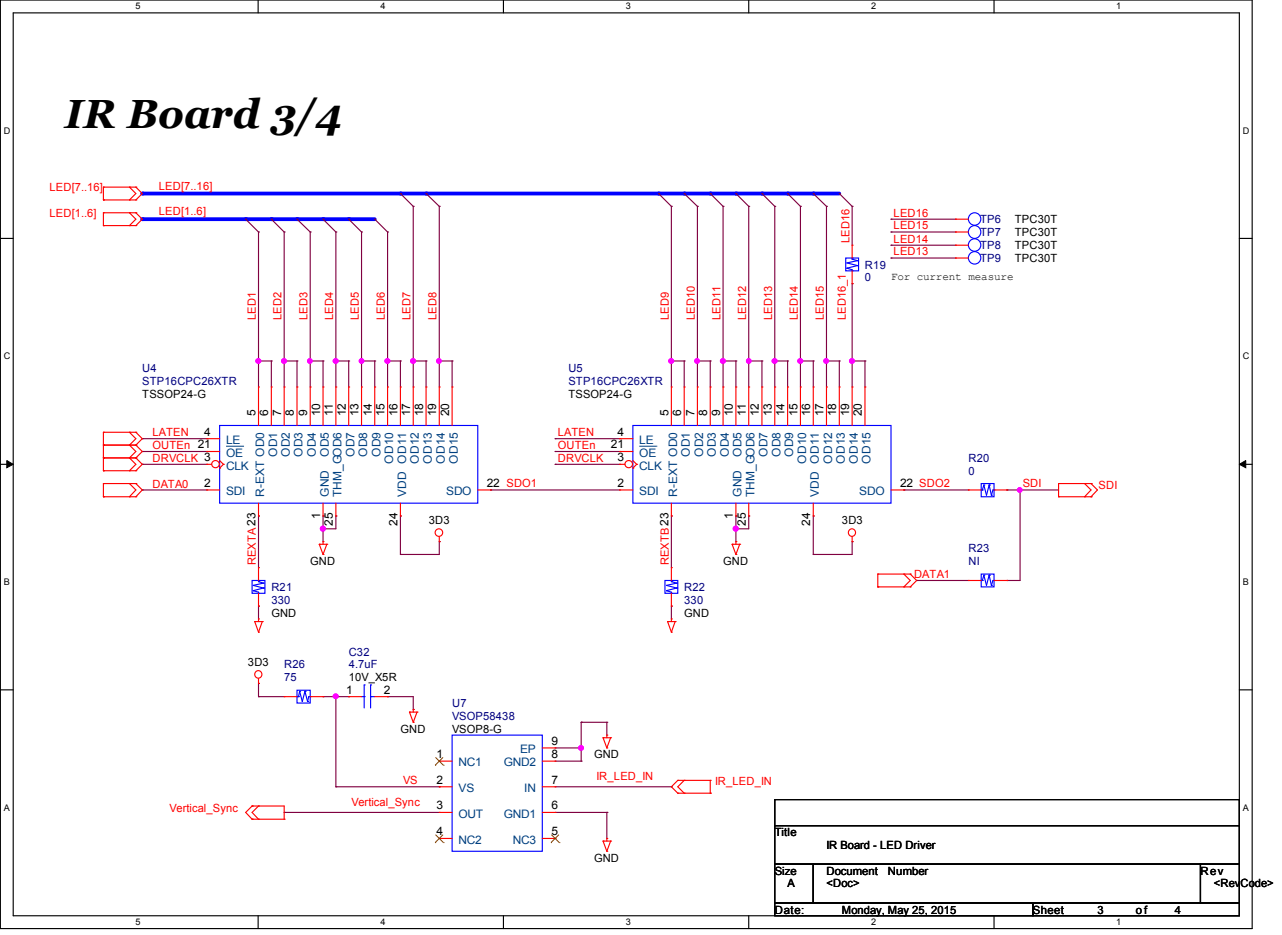
[picture p65: page 3]

IR Board - LED Driver

# IR Board 4/4

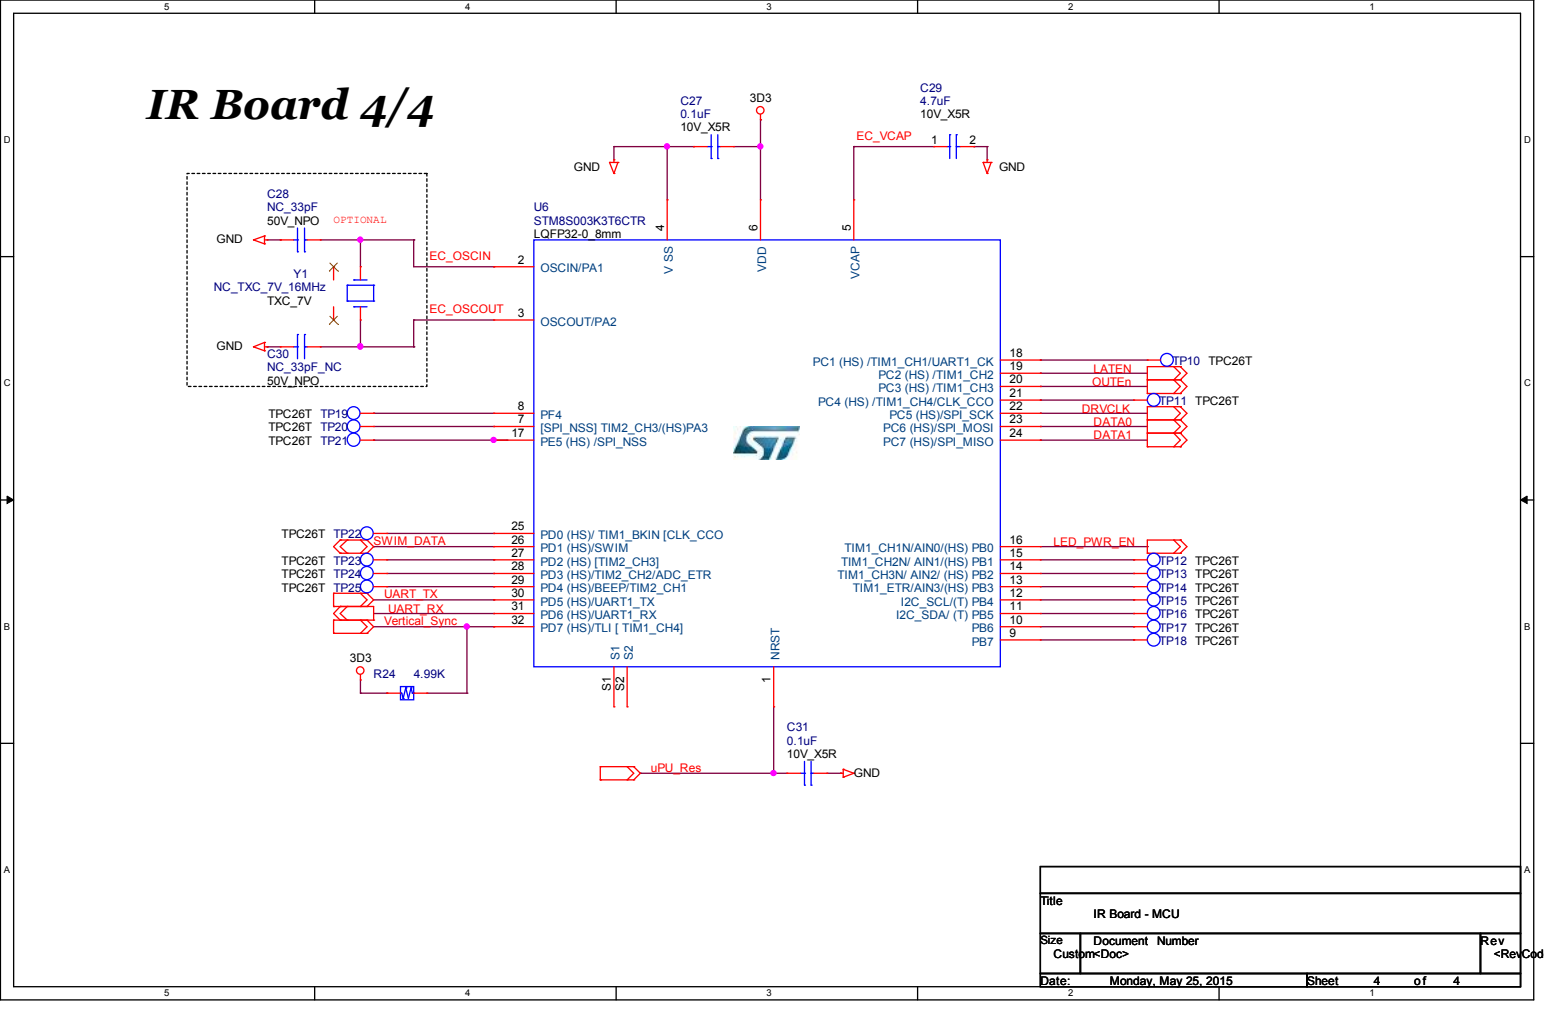
[picture p66: page 4]
