OSVR/OSVR-HDK/HDK Ver 1.2/electricals/schematics/HDMI_T34I_S2_2015_0416.pdf

# VER-T31i_S2_Re_Single

# HDMI-Single

Title; Size; Document Number; Rev; Date:; Sheet; <Doc>; Dual-HDMI; <Variant Name>

# TOP

# HDMI Connector

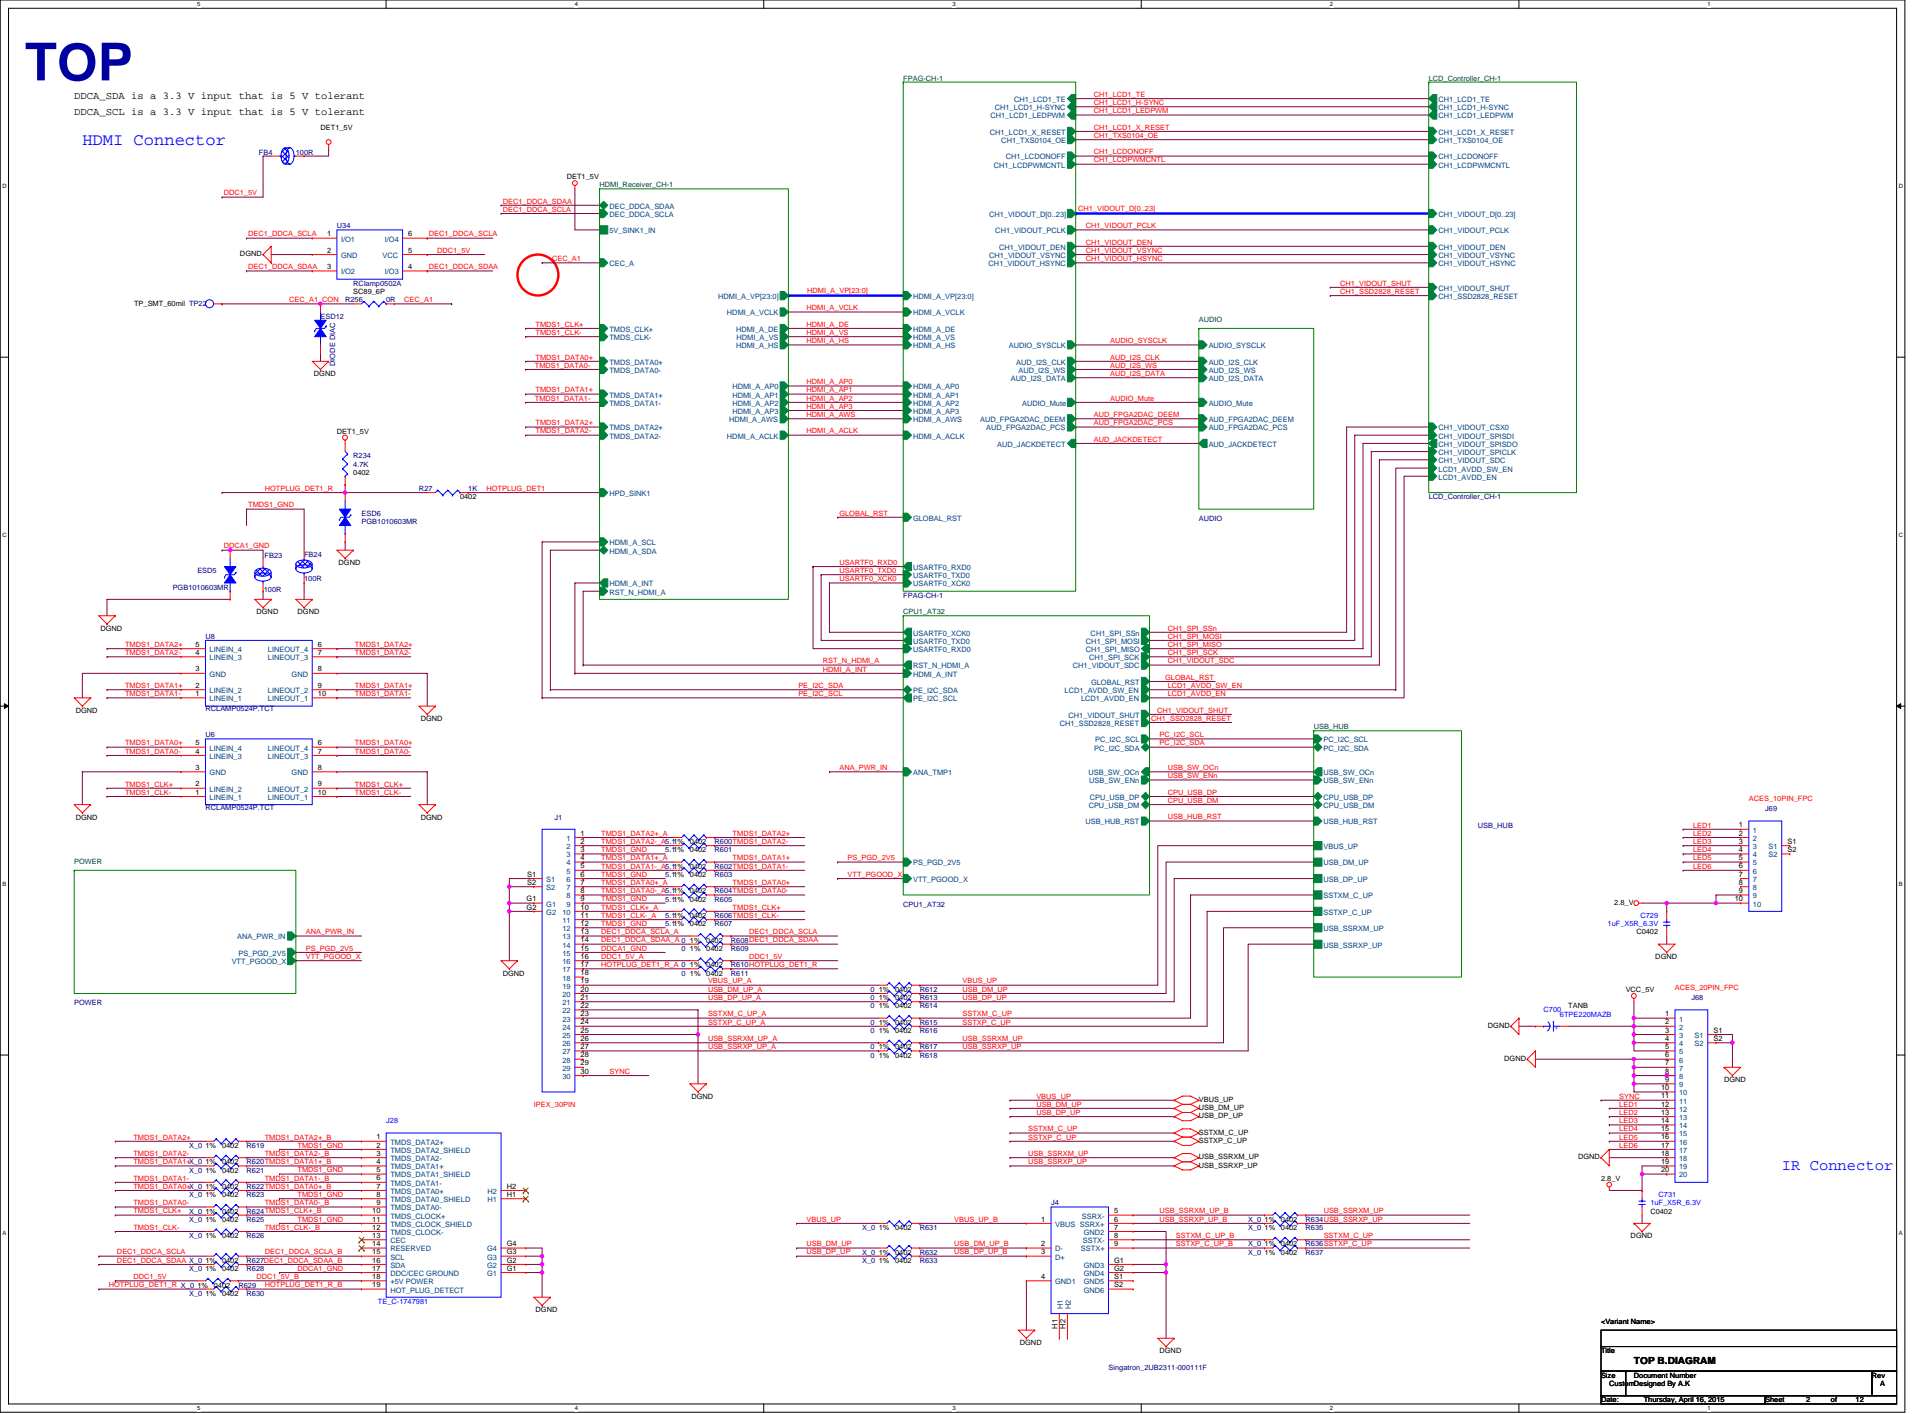
[picture p67: page 2]

DDCA_SDA is a 3.3 V input that is 5 V tolerant
DDCA_SCL is a 3.3 V input that is 5 V tolerant

HDMI_A_AP3 | AUD_FPGA2DAC_DEEM

HDMI_A_ACLK | AUD_FPGA2DAC_PCS

# DNP FB59 , C641 ,U50, R560, R561 C642

# DNP R461 R463 C576

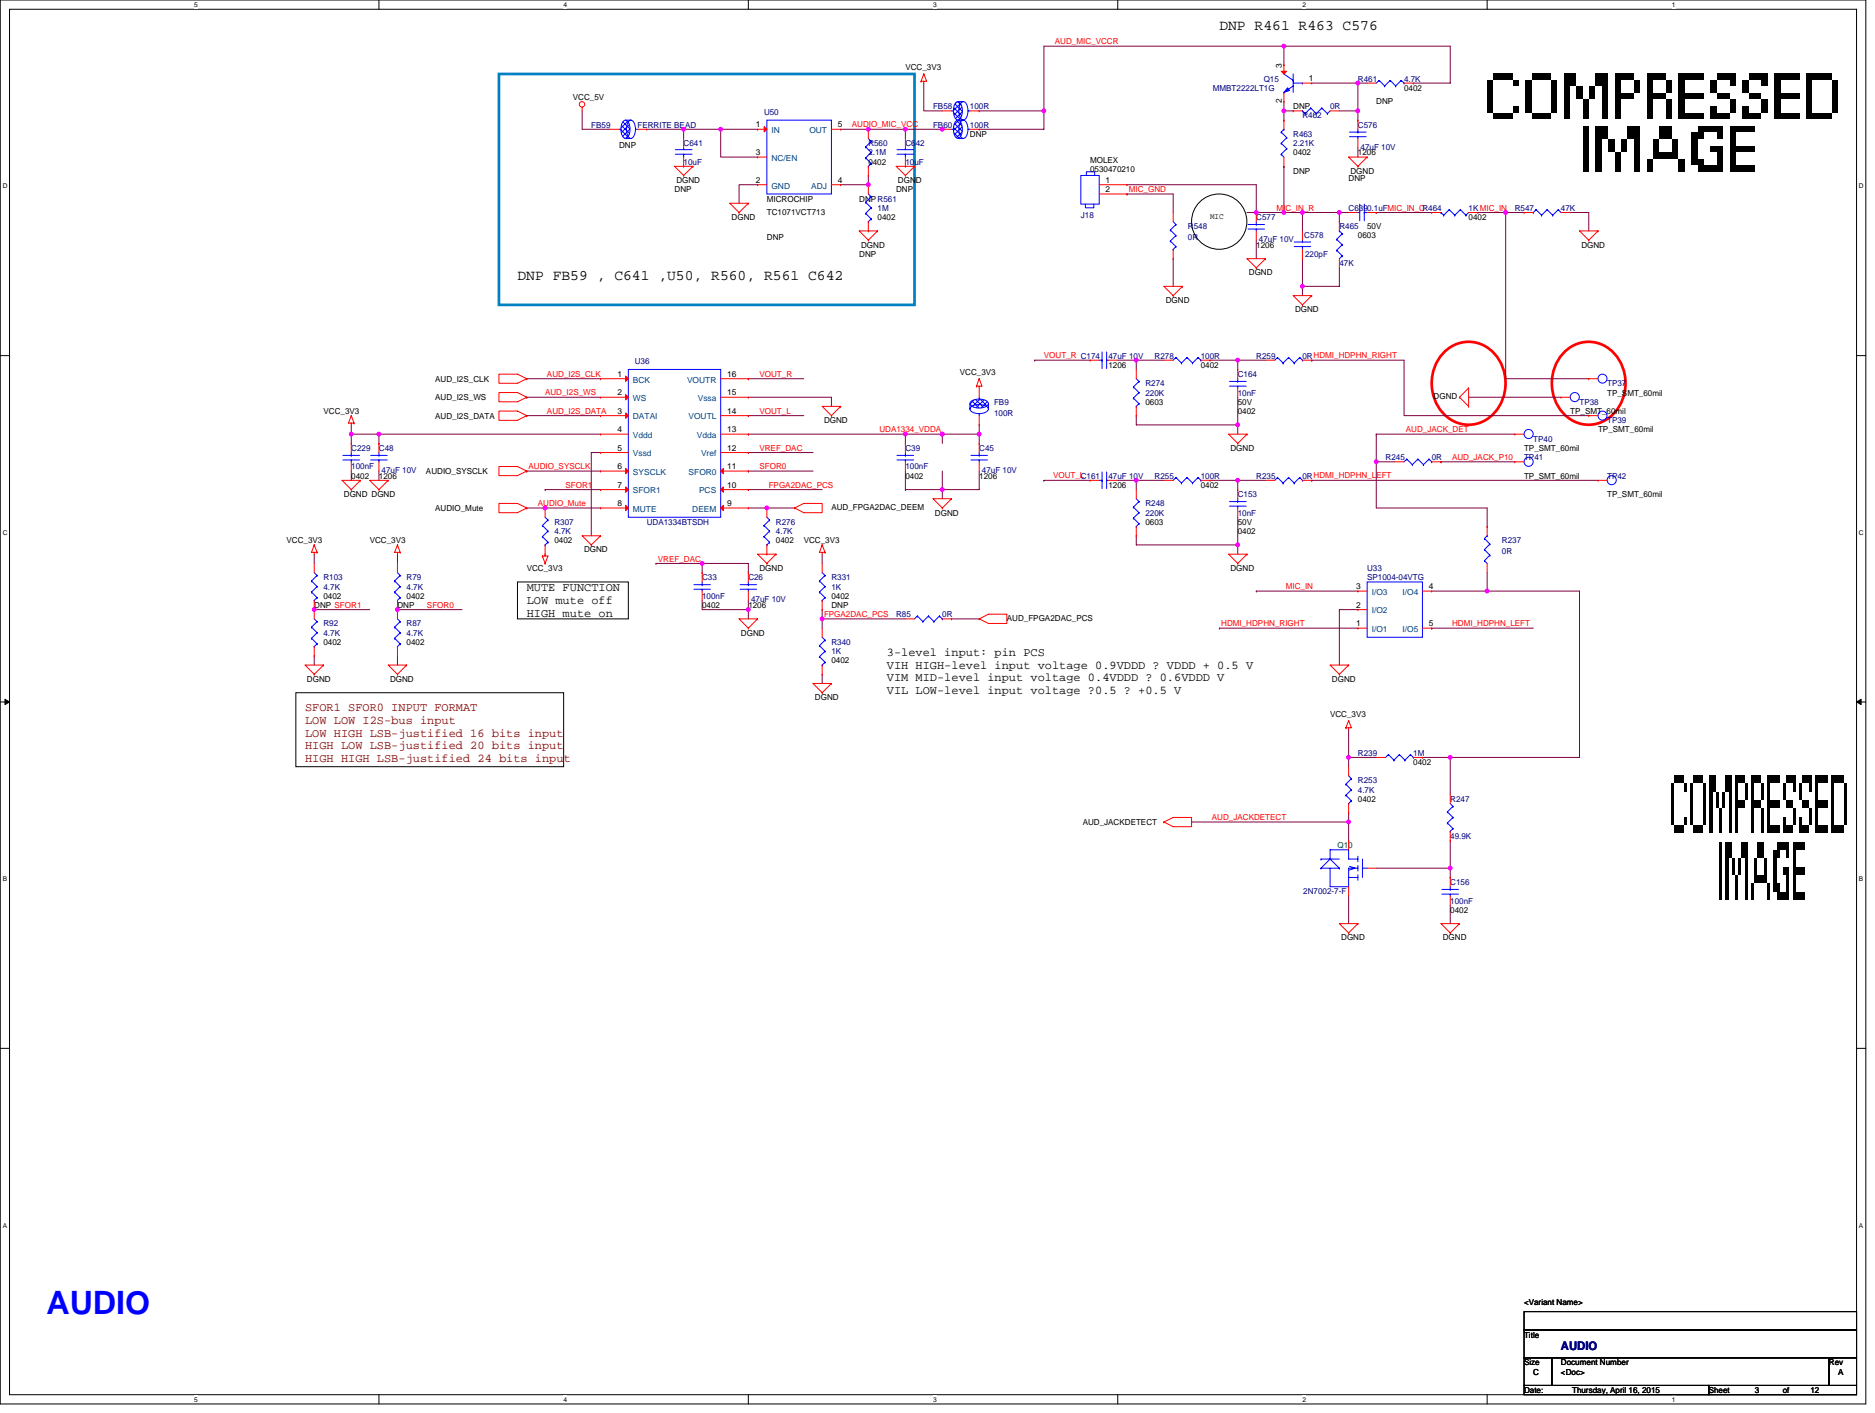
[picture p68: page 3]

3-level input: pin PCS
VIH HIGH-level input voltage 0.9VDDD ? VDDD + 0.5 V
VIM MID-level input voltage 0.4VDDD ? 0.6VDDD V
VIL LOW-level input voltage ?0.5 ? +0.5 V

SFOR1 SFOR0 INPUT FORMAT
LOW LOW I2S-bus input
LOW HIGH LSB-justified 16 bits input
HIGH LOW LSB-justified 20 bits input
HIGH HIGH LSB-justified 24 bits input

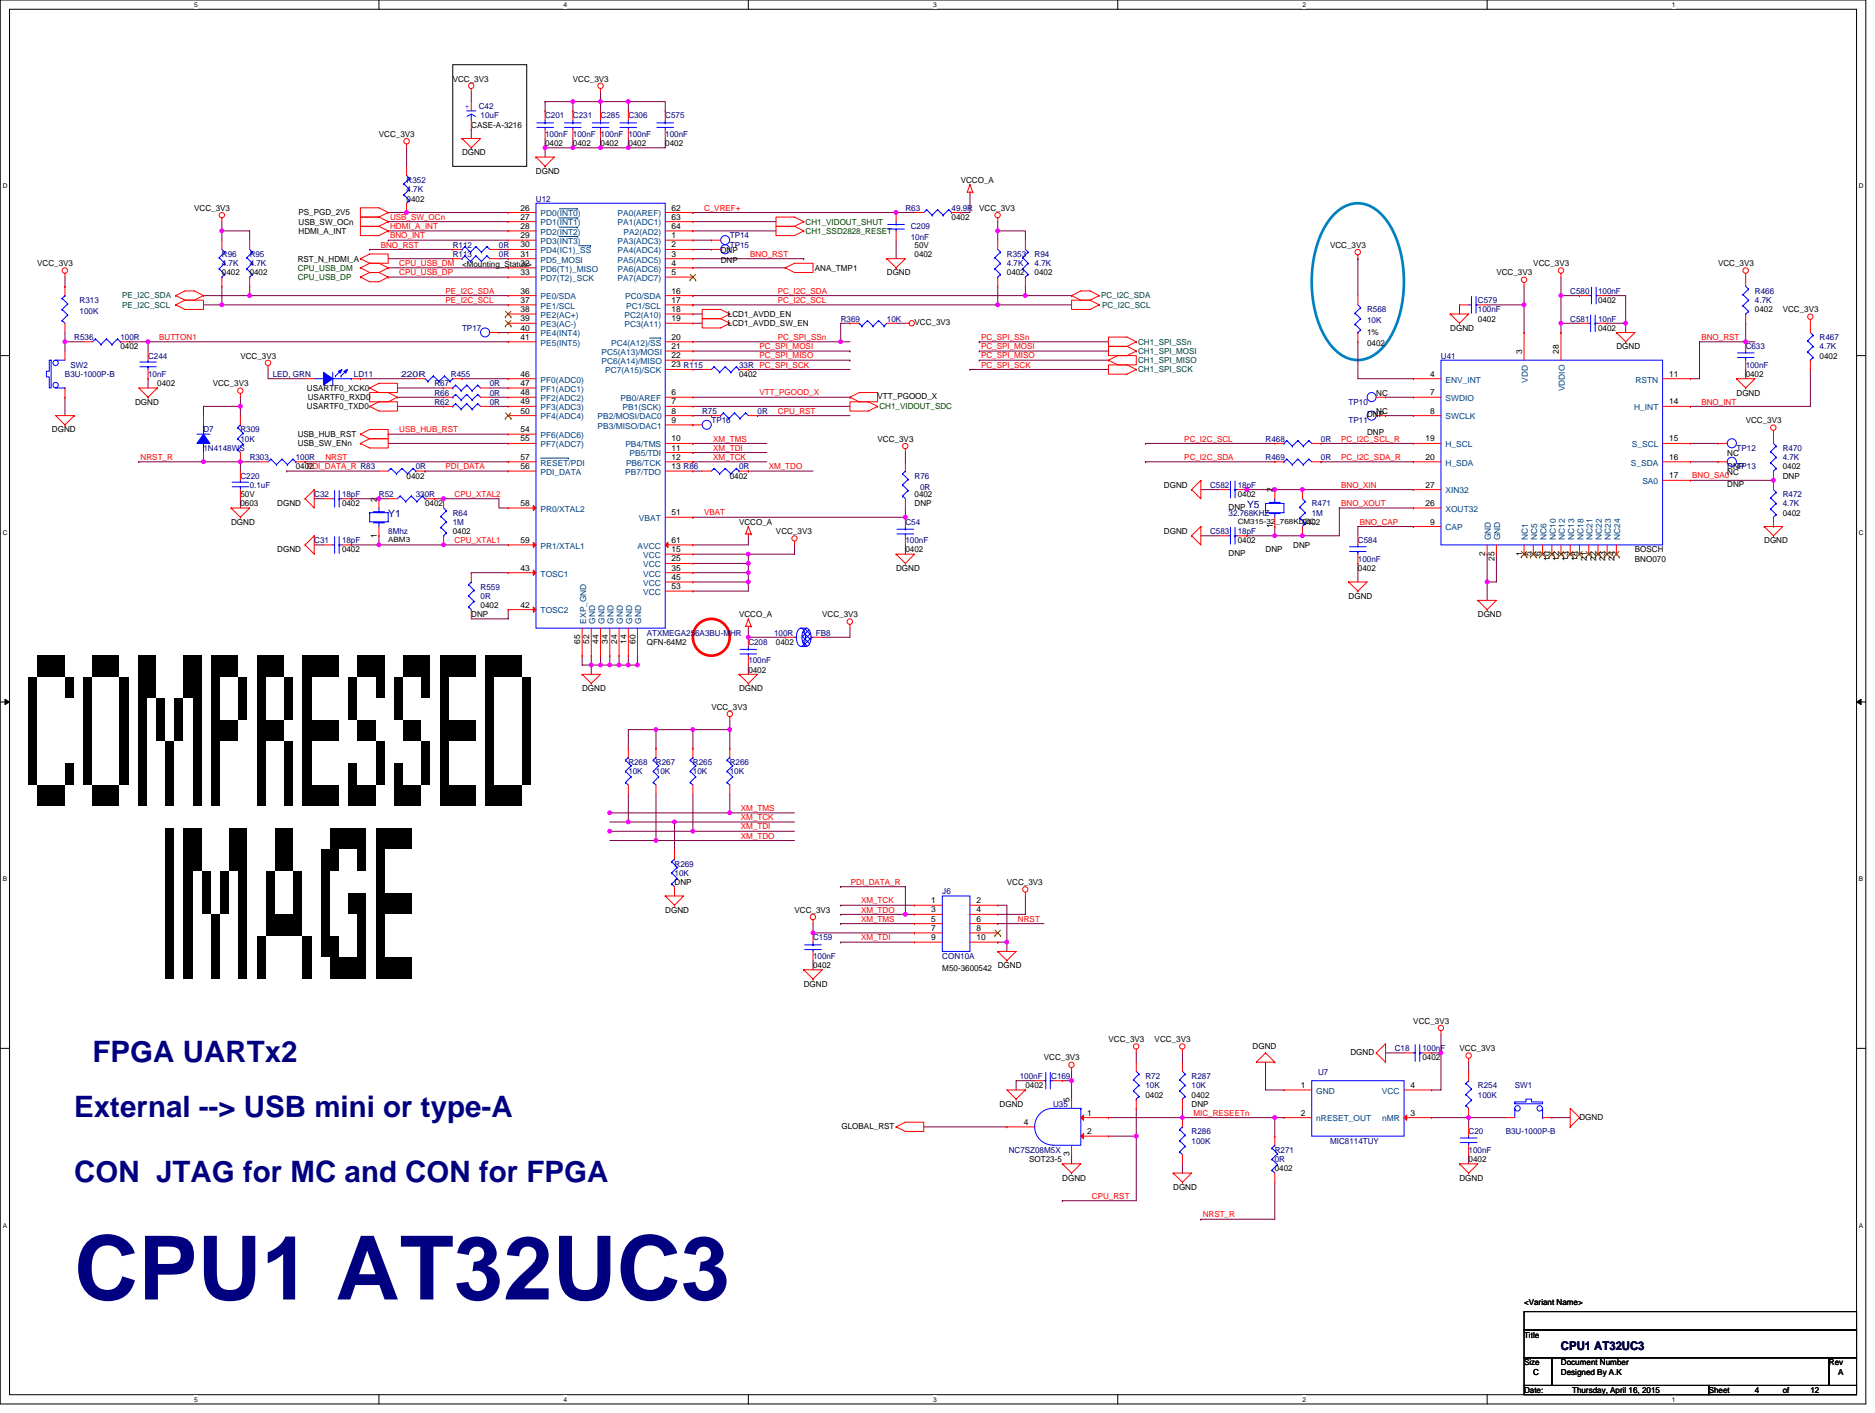
[picture p69: page 4]

FPGA UARTx2
External --> USB mini or type-A

CON JTAG for MC and CON for FPGA
CPU1 AT32UC3

FPGA - Audio/Video Input from SDI Receiver (3.3V) | FPGA - Audio/Video & SDI Rx Ctrl Signals

## R400 repleace SBY100505T-470Y-N

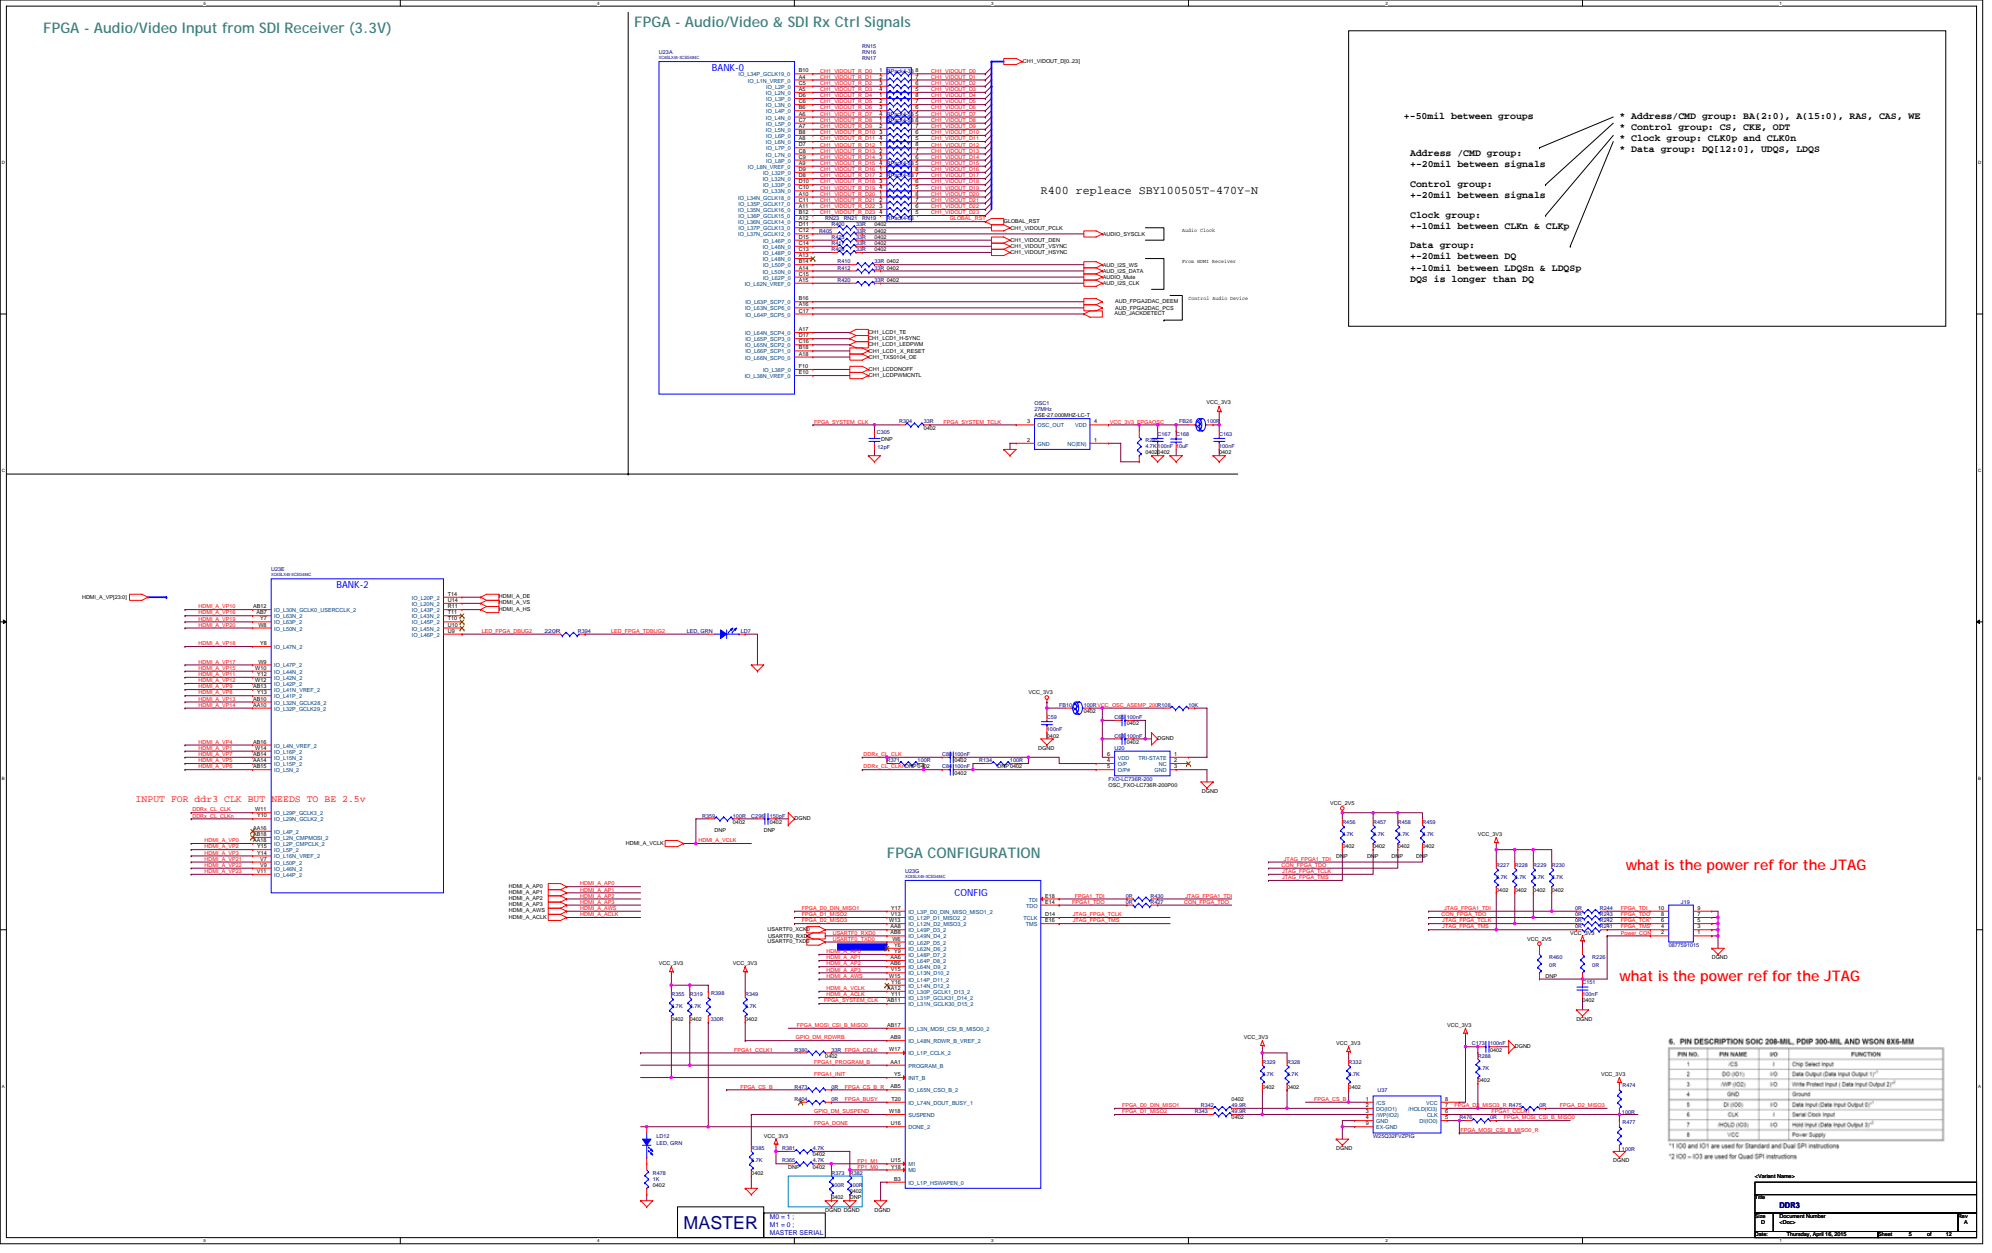
[picture p70: page 5]

* Address/CMD group: BA(2:0), A(15:0), RAS, CAS, WE
* Control group: CS, CKE, ODT
* Clock group: CLK0p and CLK0n
* Data group: DQ[12:0], UDQS, LDQS

Address /CMD group:
+-20mil between signals
Control group:
Clock group:
+-10mil between CLKn & CLKp
Data group:
+-20mil between DQ
+-10mil between LDQSn & LDQSp
DQS is longer than DQ

what is the power ref for the JTAG

# FPGA - DDR3 Interface (1.5V)

# DDR0_D11_FPAG-CH-1U30.A2

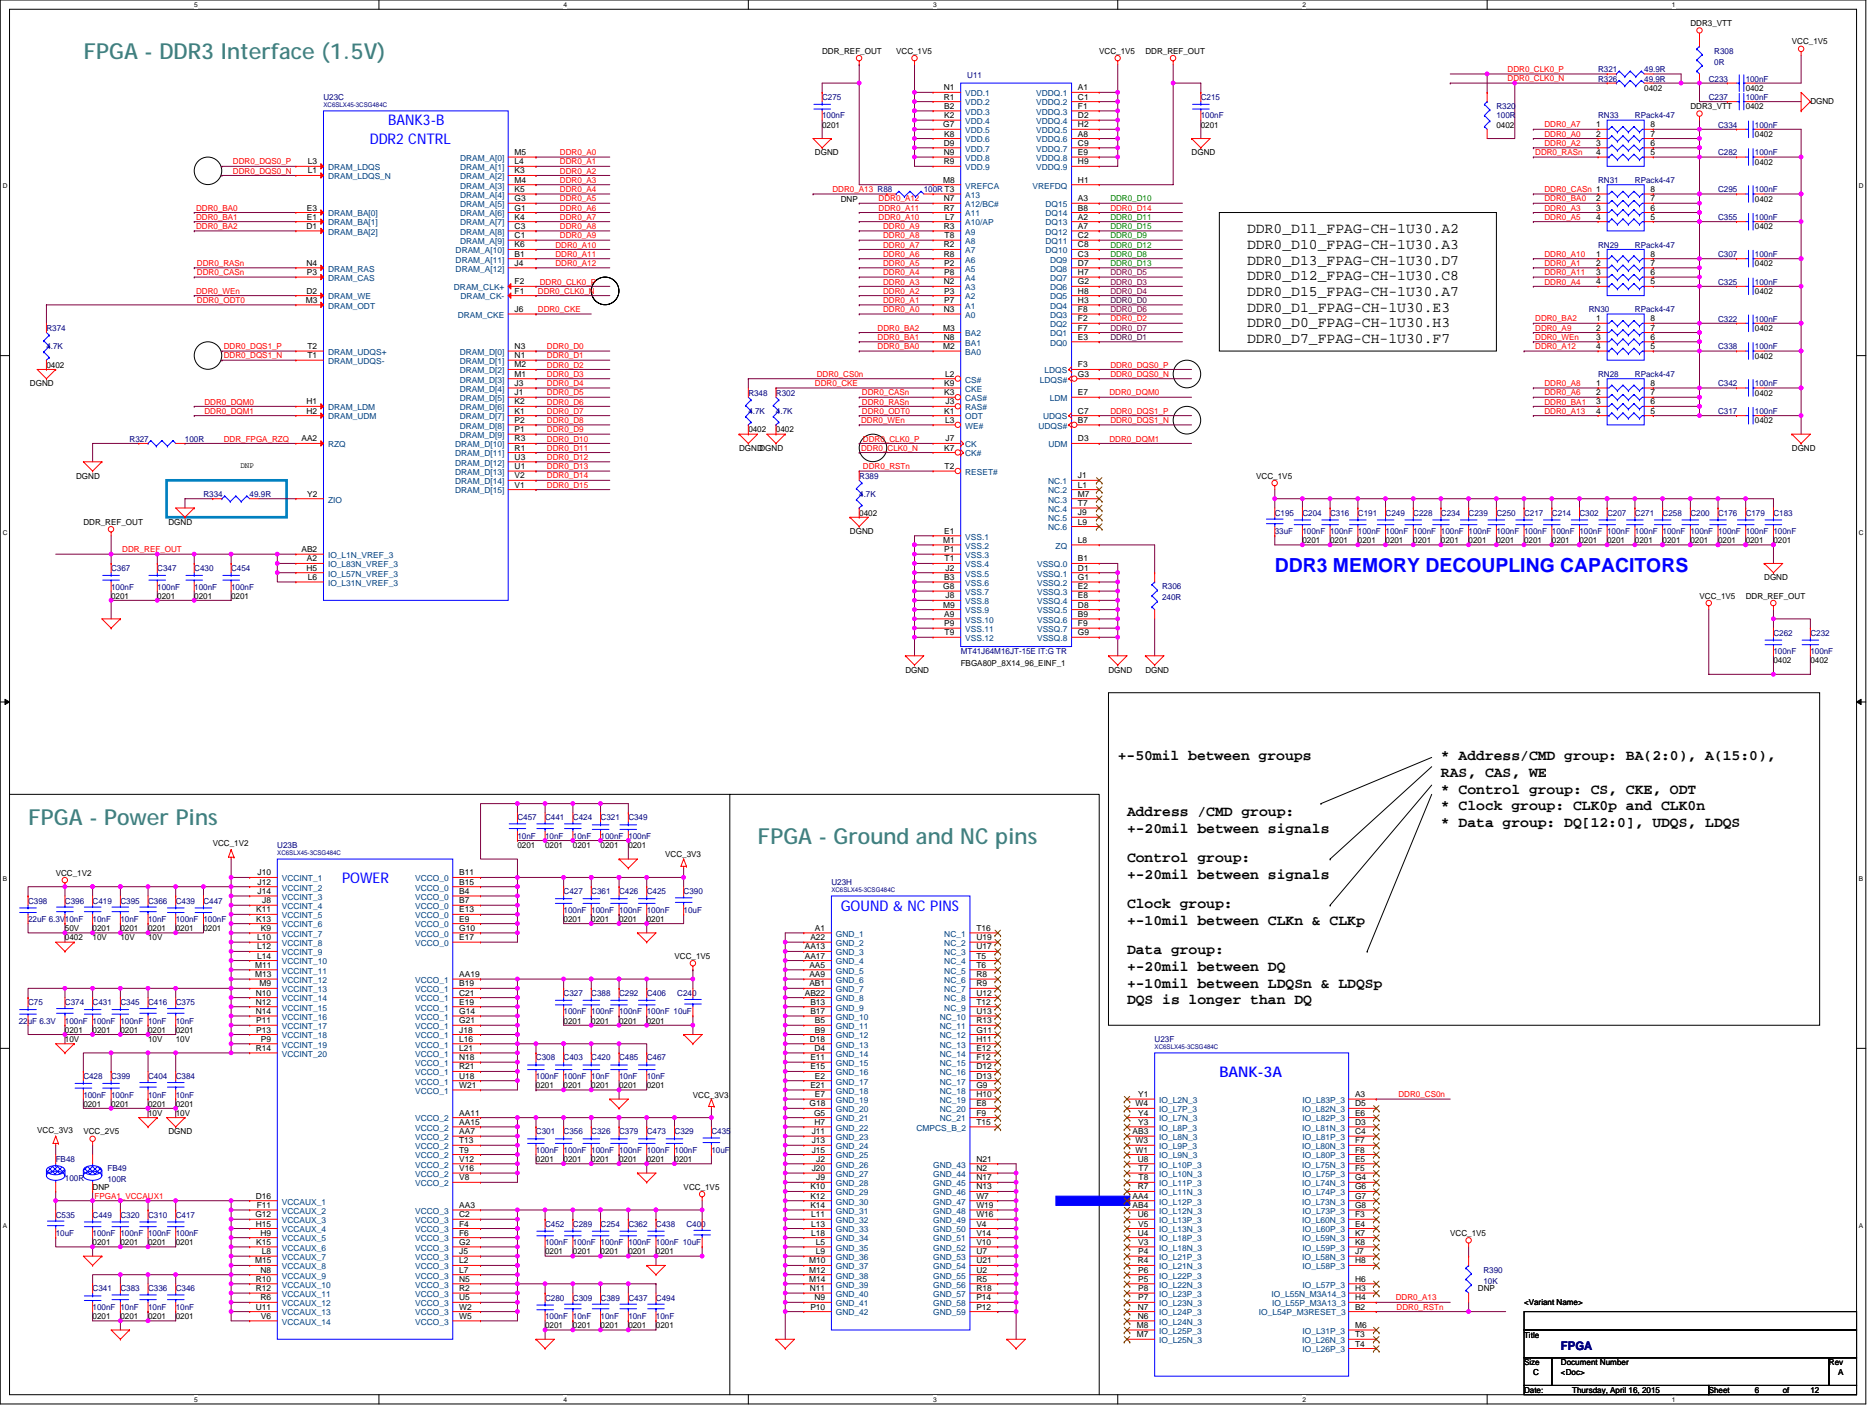
[picture p71: page 6]
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

FPGA - Ground and NC pins

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

# DDR0 MEMORY INTERFACE

## DDR1_DQ12_FPAG-CH-1U29.C2

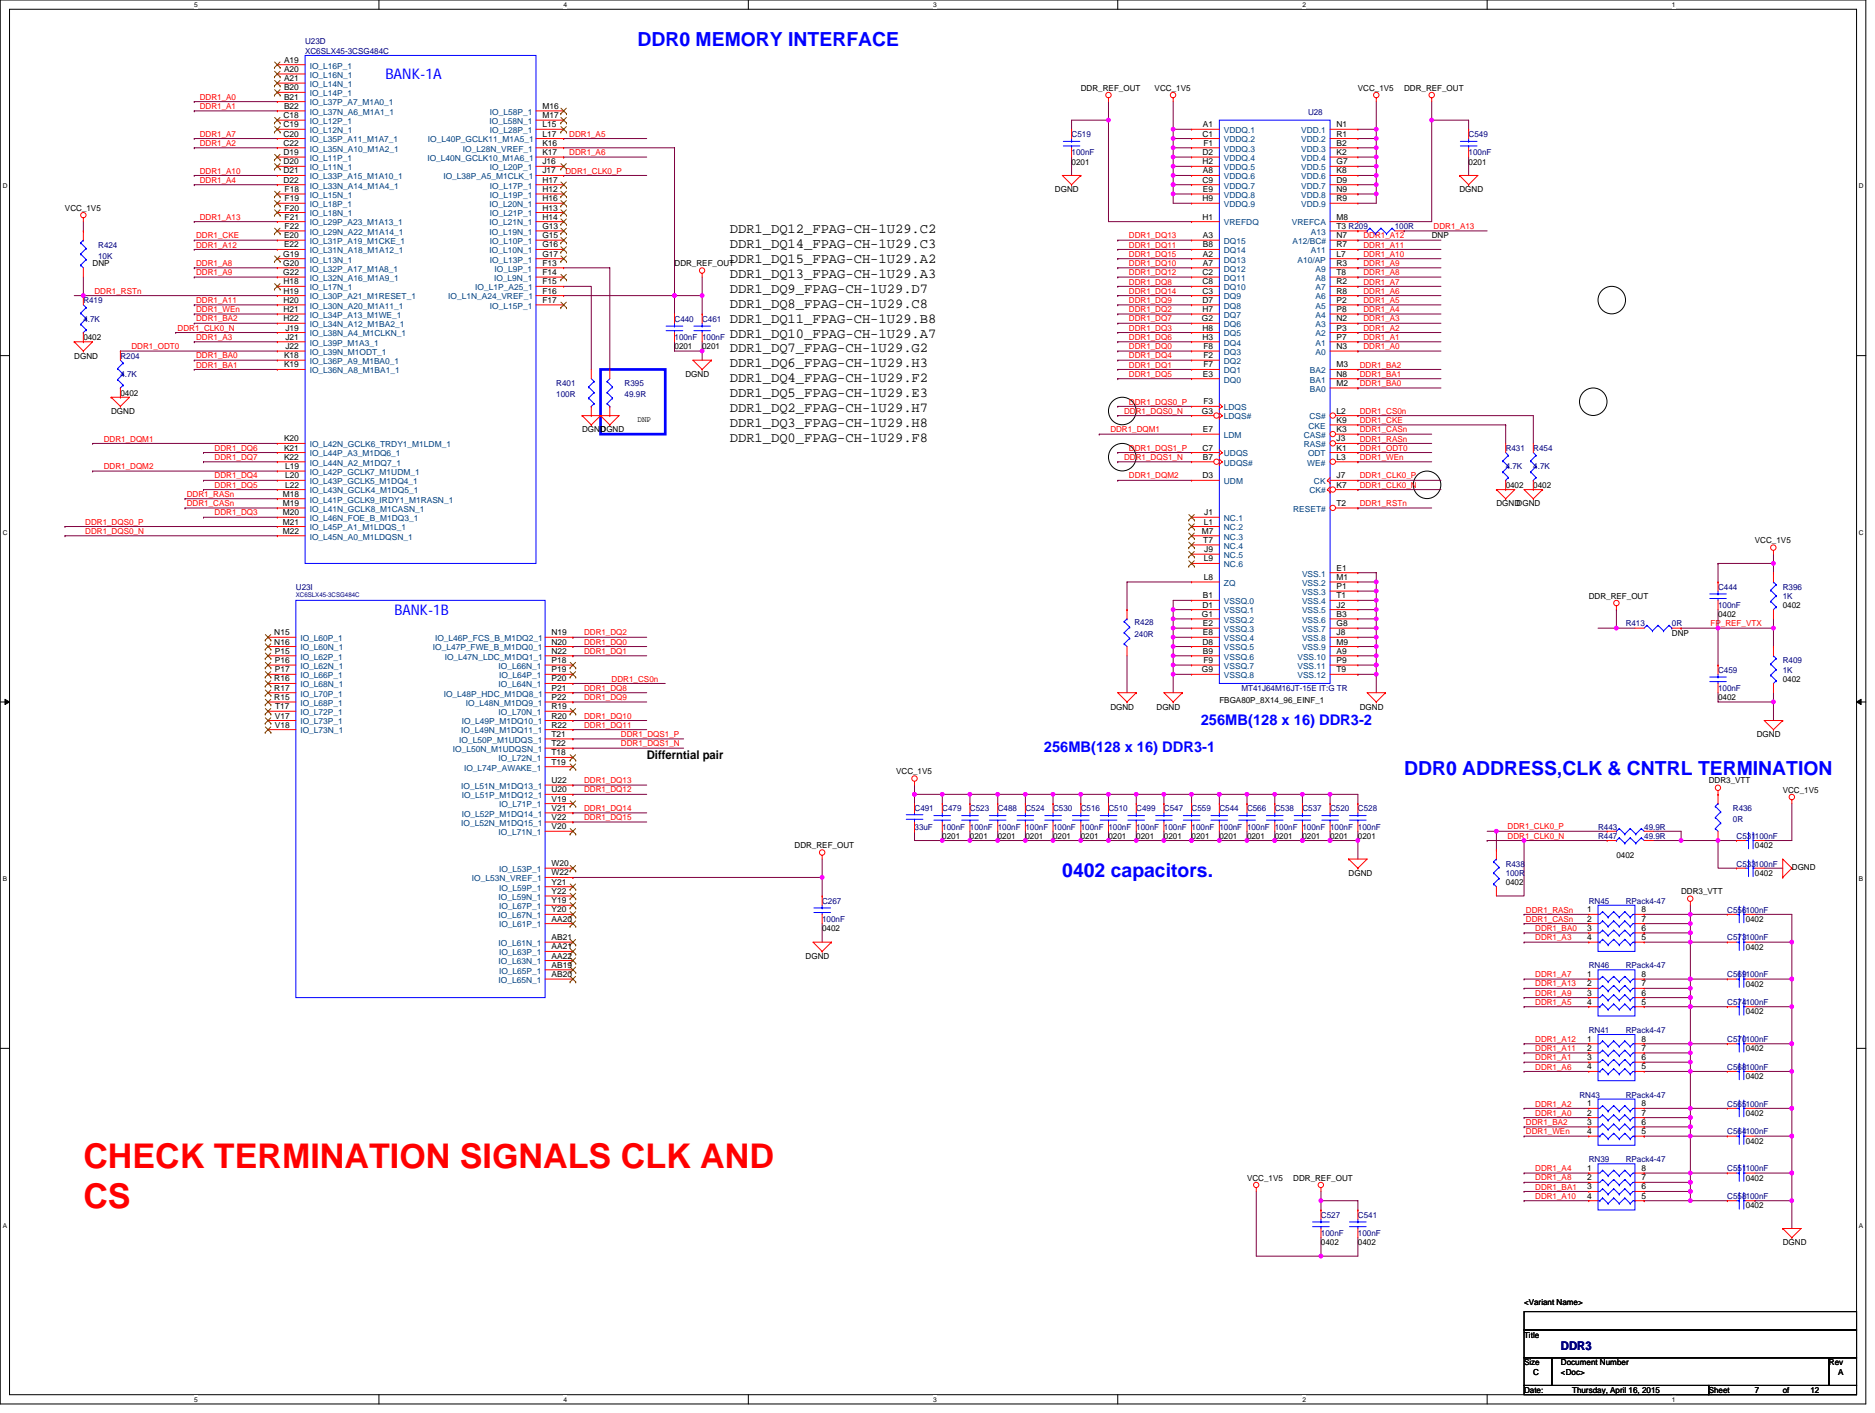
[picture p72: page 7]

CHECK TERMINATION SIGNALS CLK AND

# HDMI RECEIVER PORT A

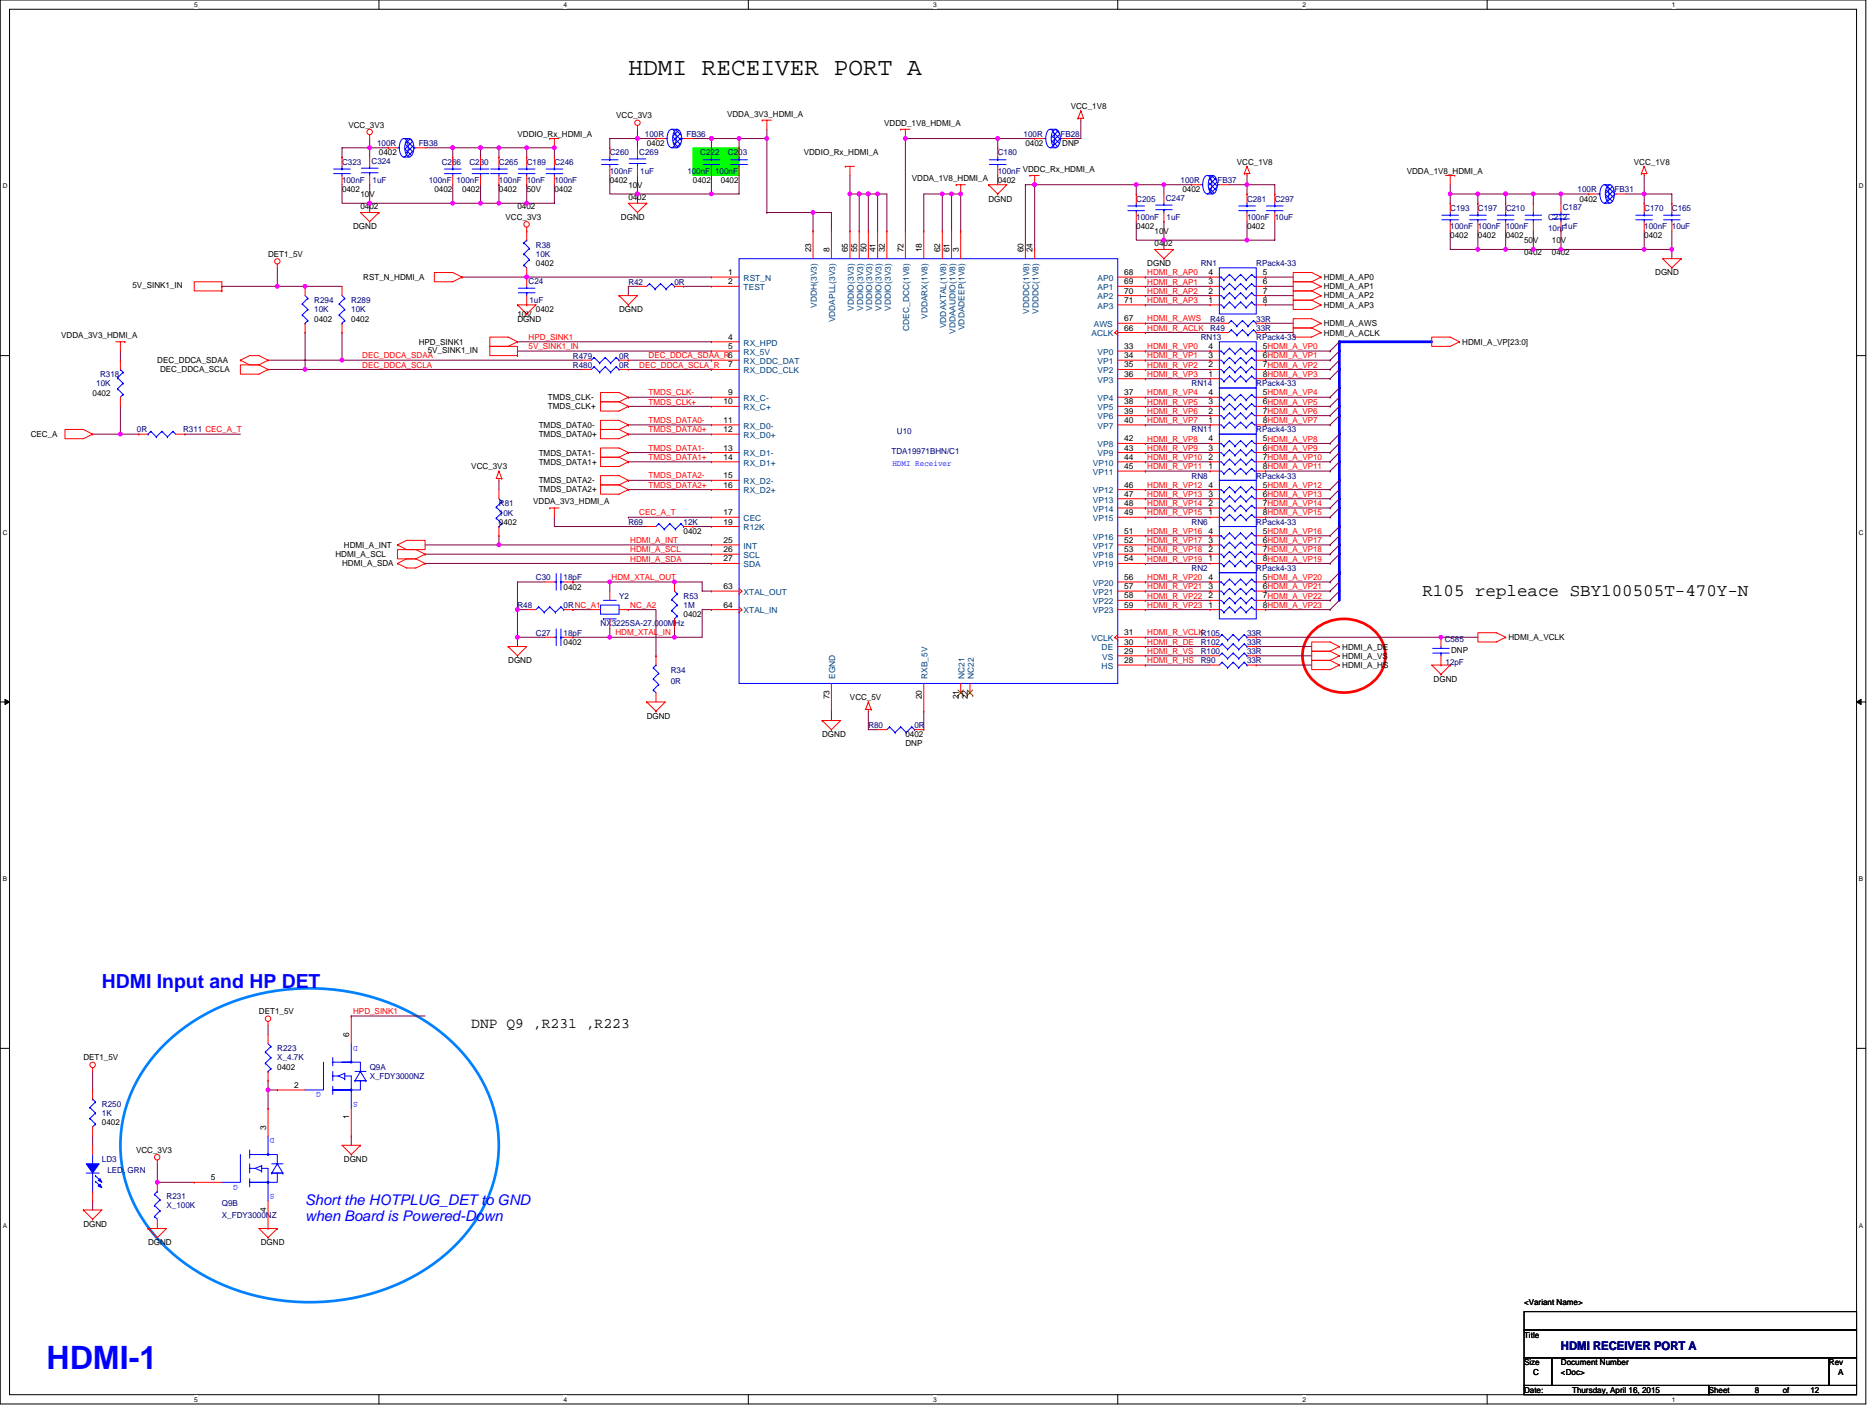
[picture p73: page 8]

VDDIO(3V3) 32 VDDIO(3V3) 41 VDDIO(3V3) 50 VDDIO(3V3) 55

HDMI Input and HP DET

Short the HOTPLUG_DET to GND
when Board is Powered-Down

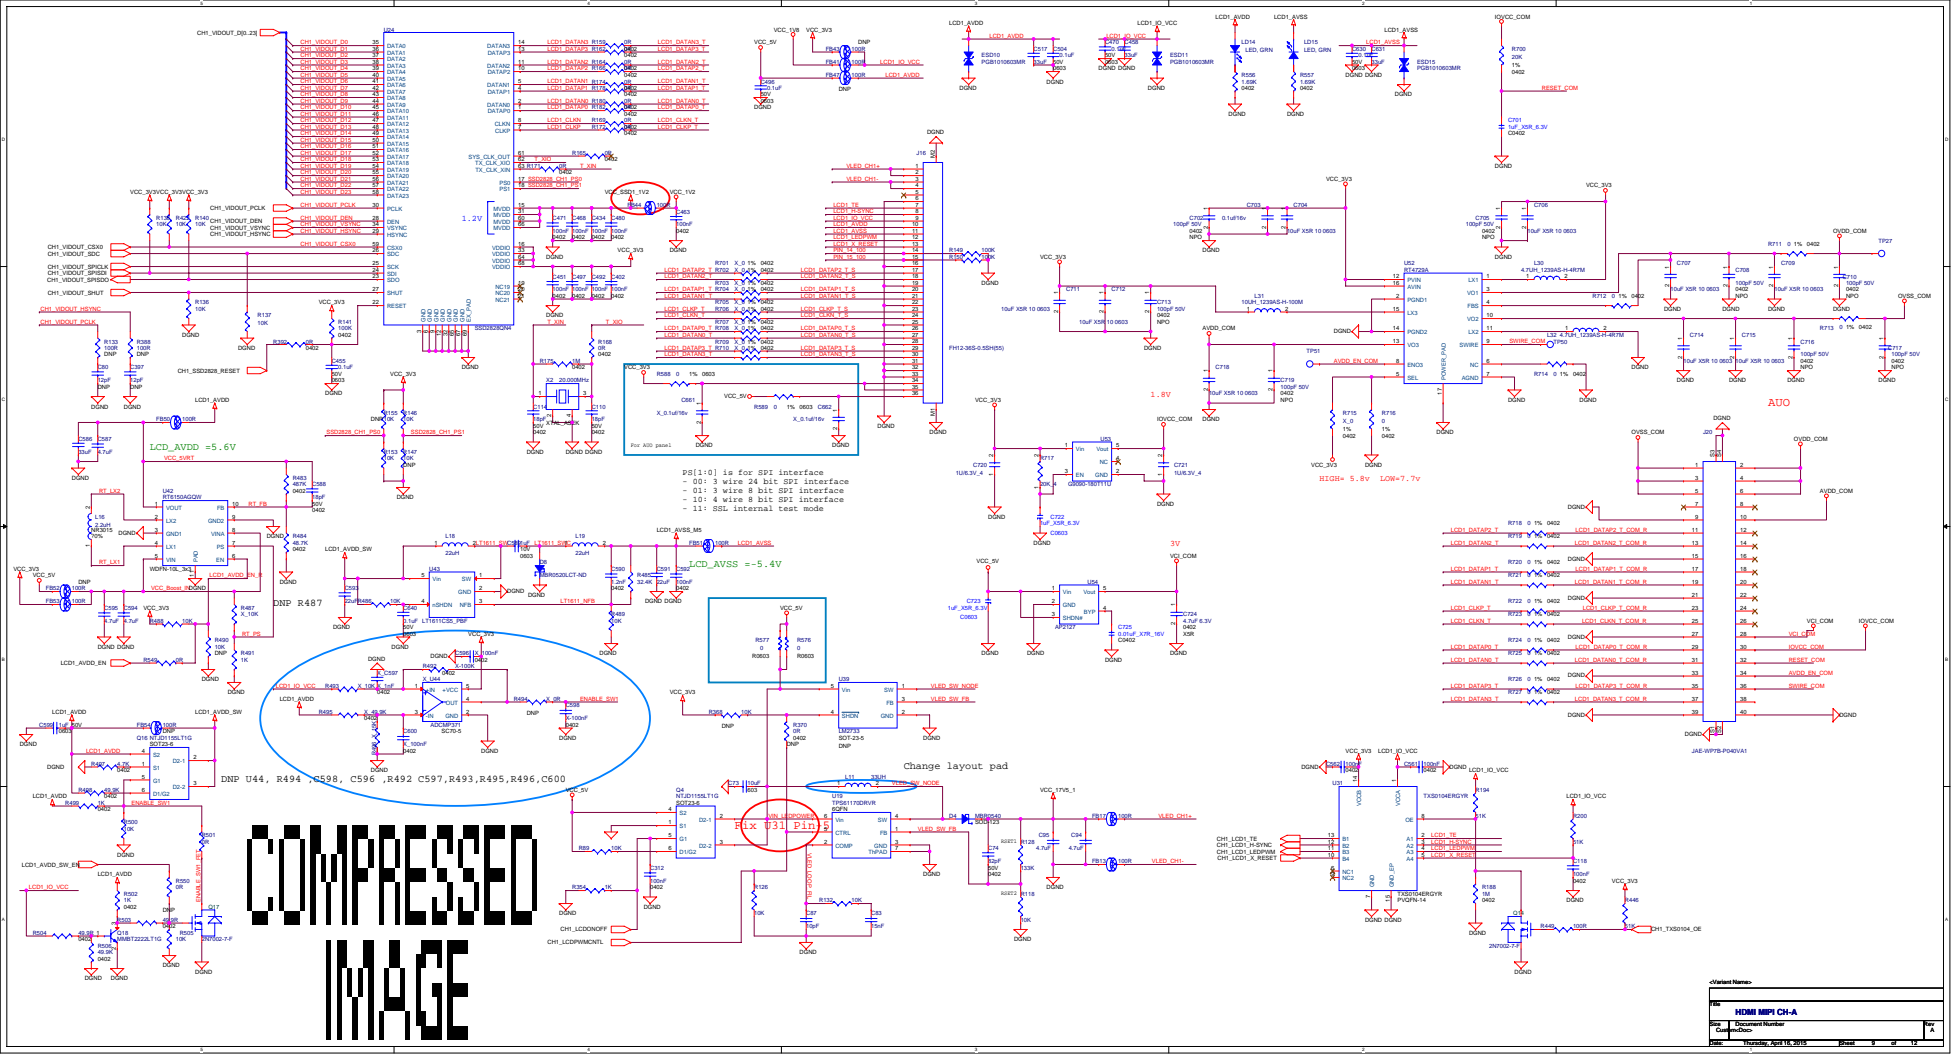
[picture p74: page 9]

PS[1:0] is for SPI interface
- 00: 3 wire 24 bit SPI interface
- 01: 3 wire 8 bit SPI interface
- 10: 4 wire 8 bit SPI interface
- 11: SSL internal test mode

# Reverse Voltage Protection

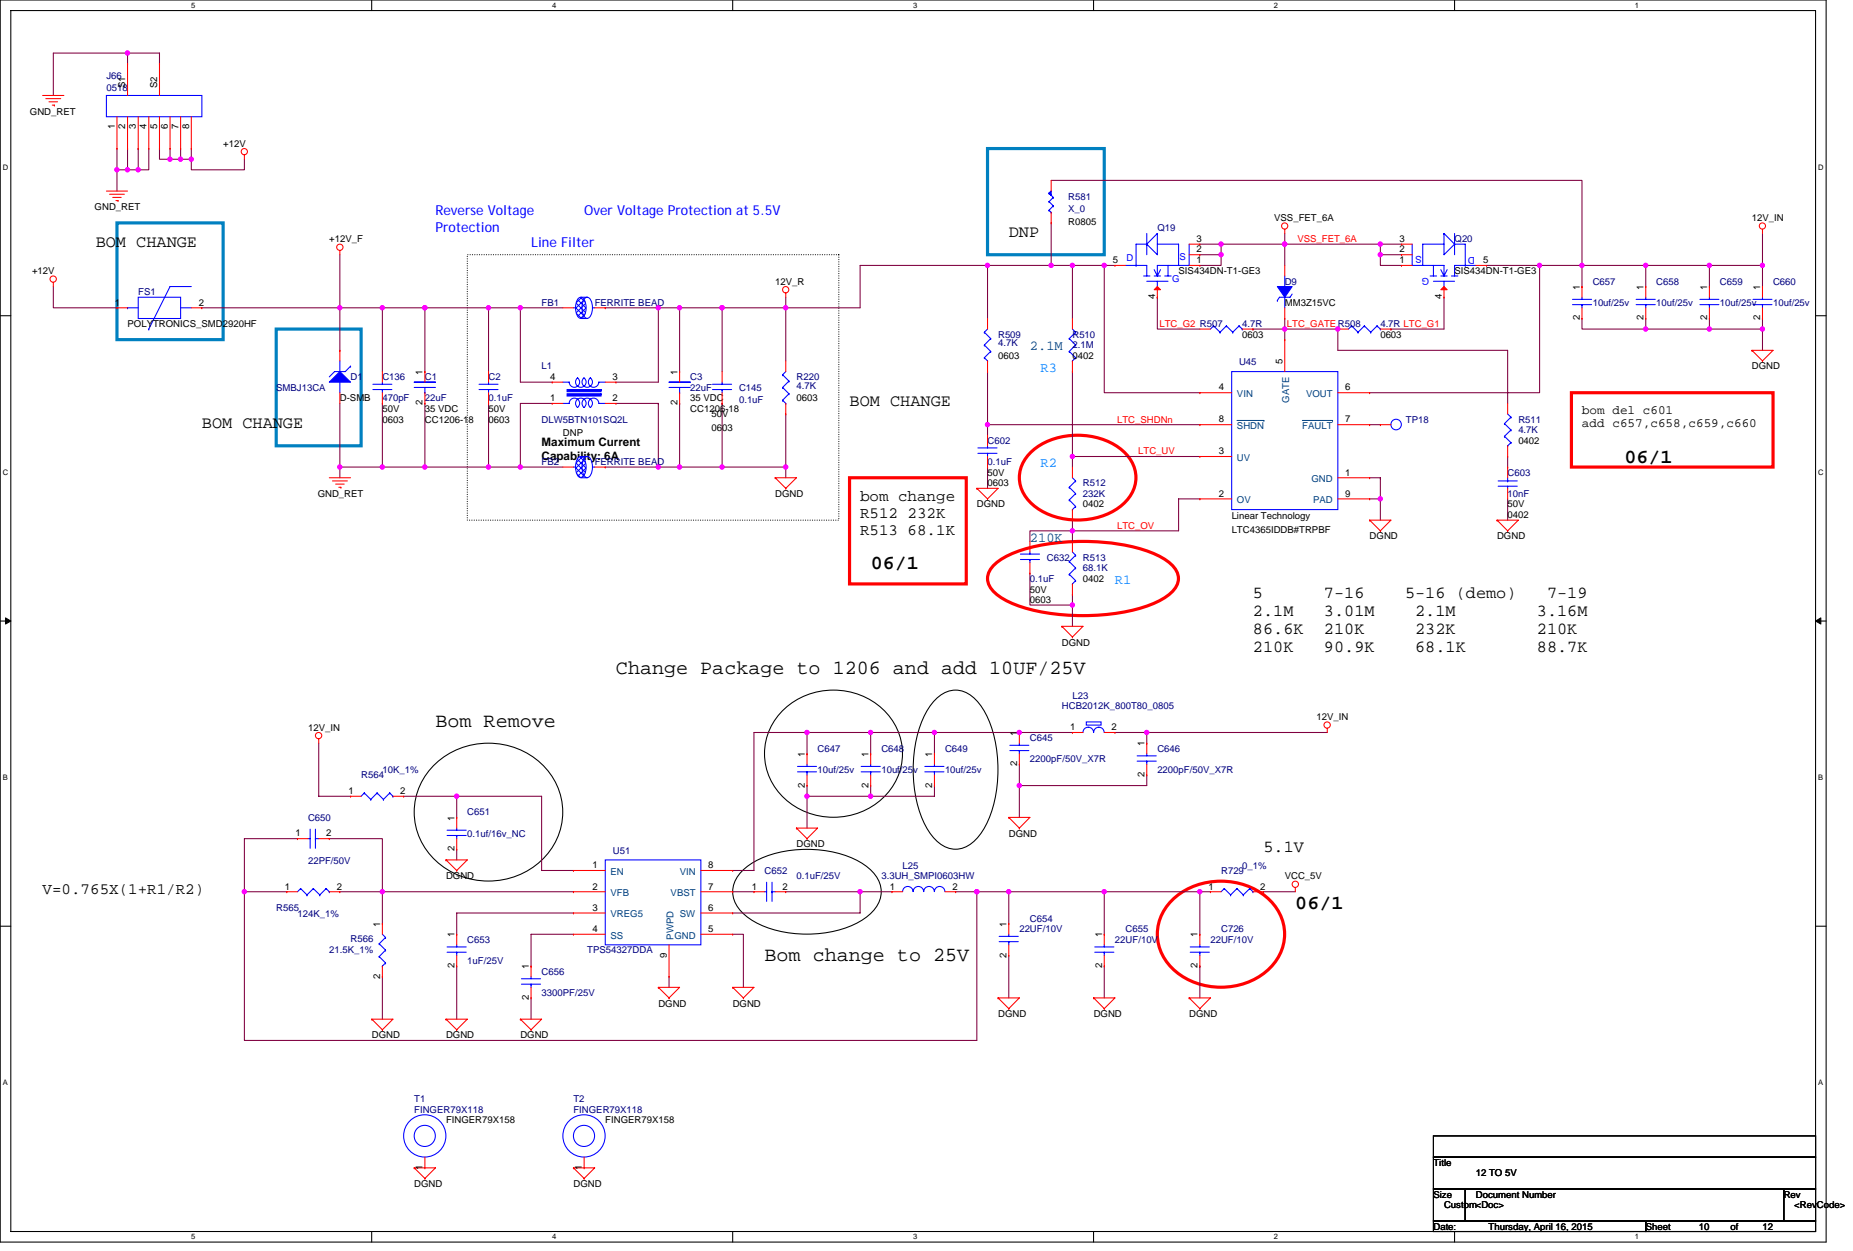
[picture p75: page 10]

Over Voltage Protection at 5.5V

Change Package to 1206 and add 10UF/25V

Size Size Size Custom Custom Custom | Document Number Document Number Document Number | Rev Rev Rev

Thursday, April 16, 2015 Thursday, April 16, 2015 Thursday, April 16, 2015 | 10 10 10 12 12 12

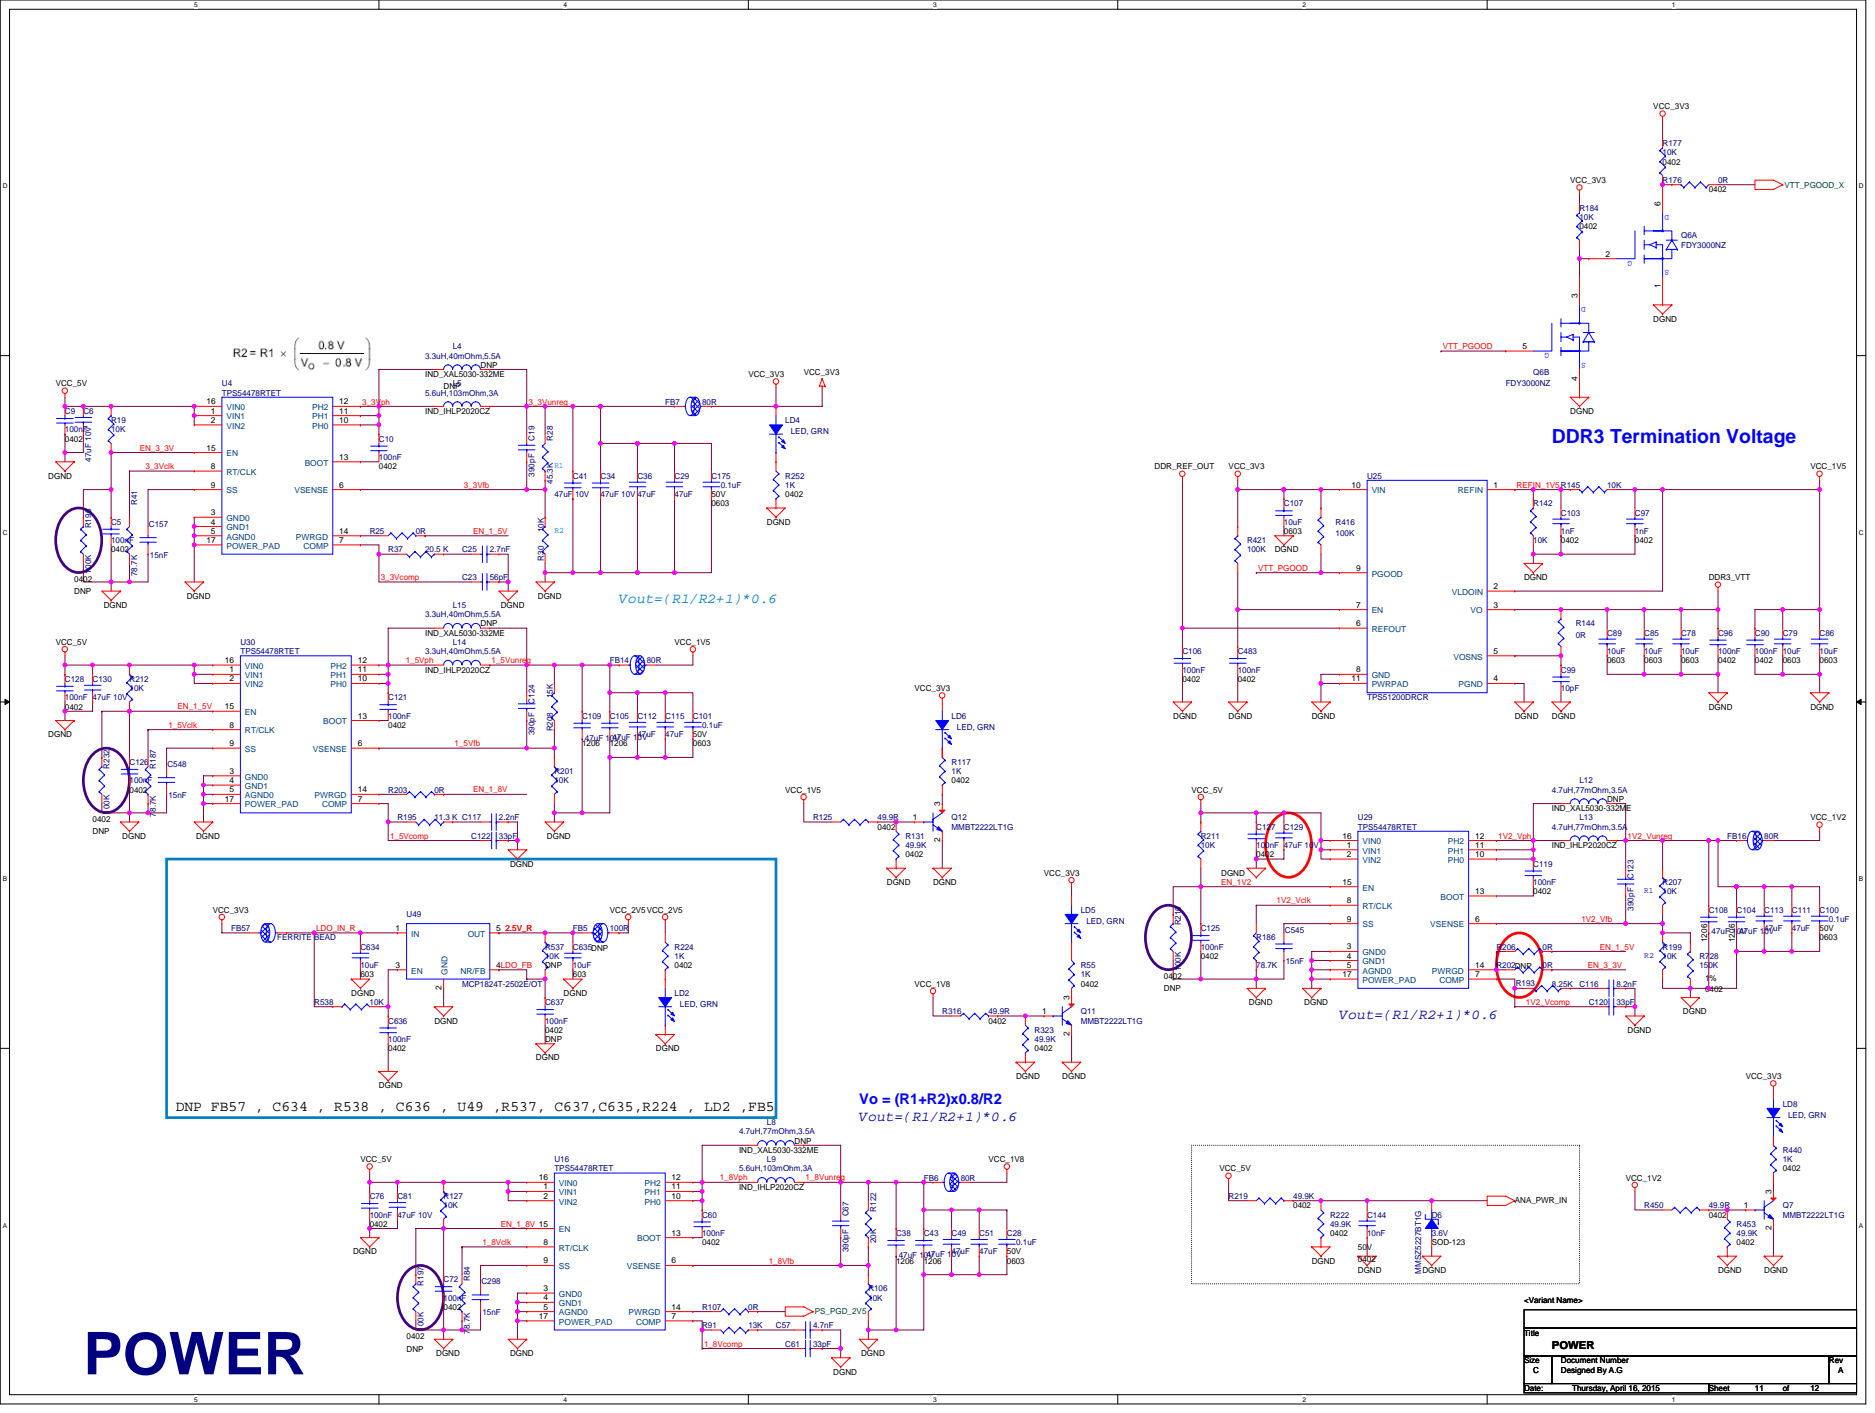
[picture p76: page 11]

## *Note that the SS signal pair Tx+/ are polarity

swapped on Jx for better routing.

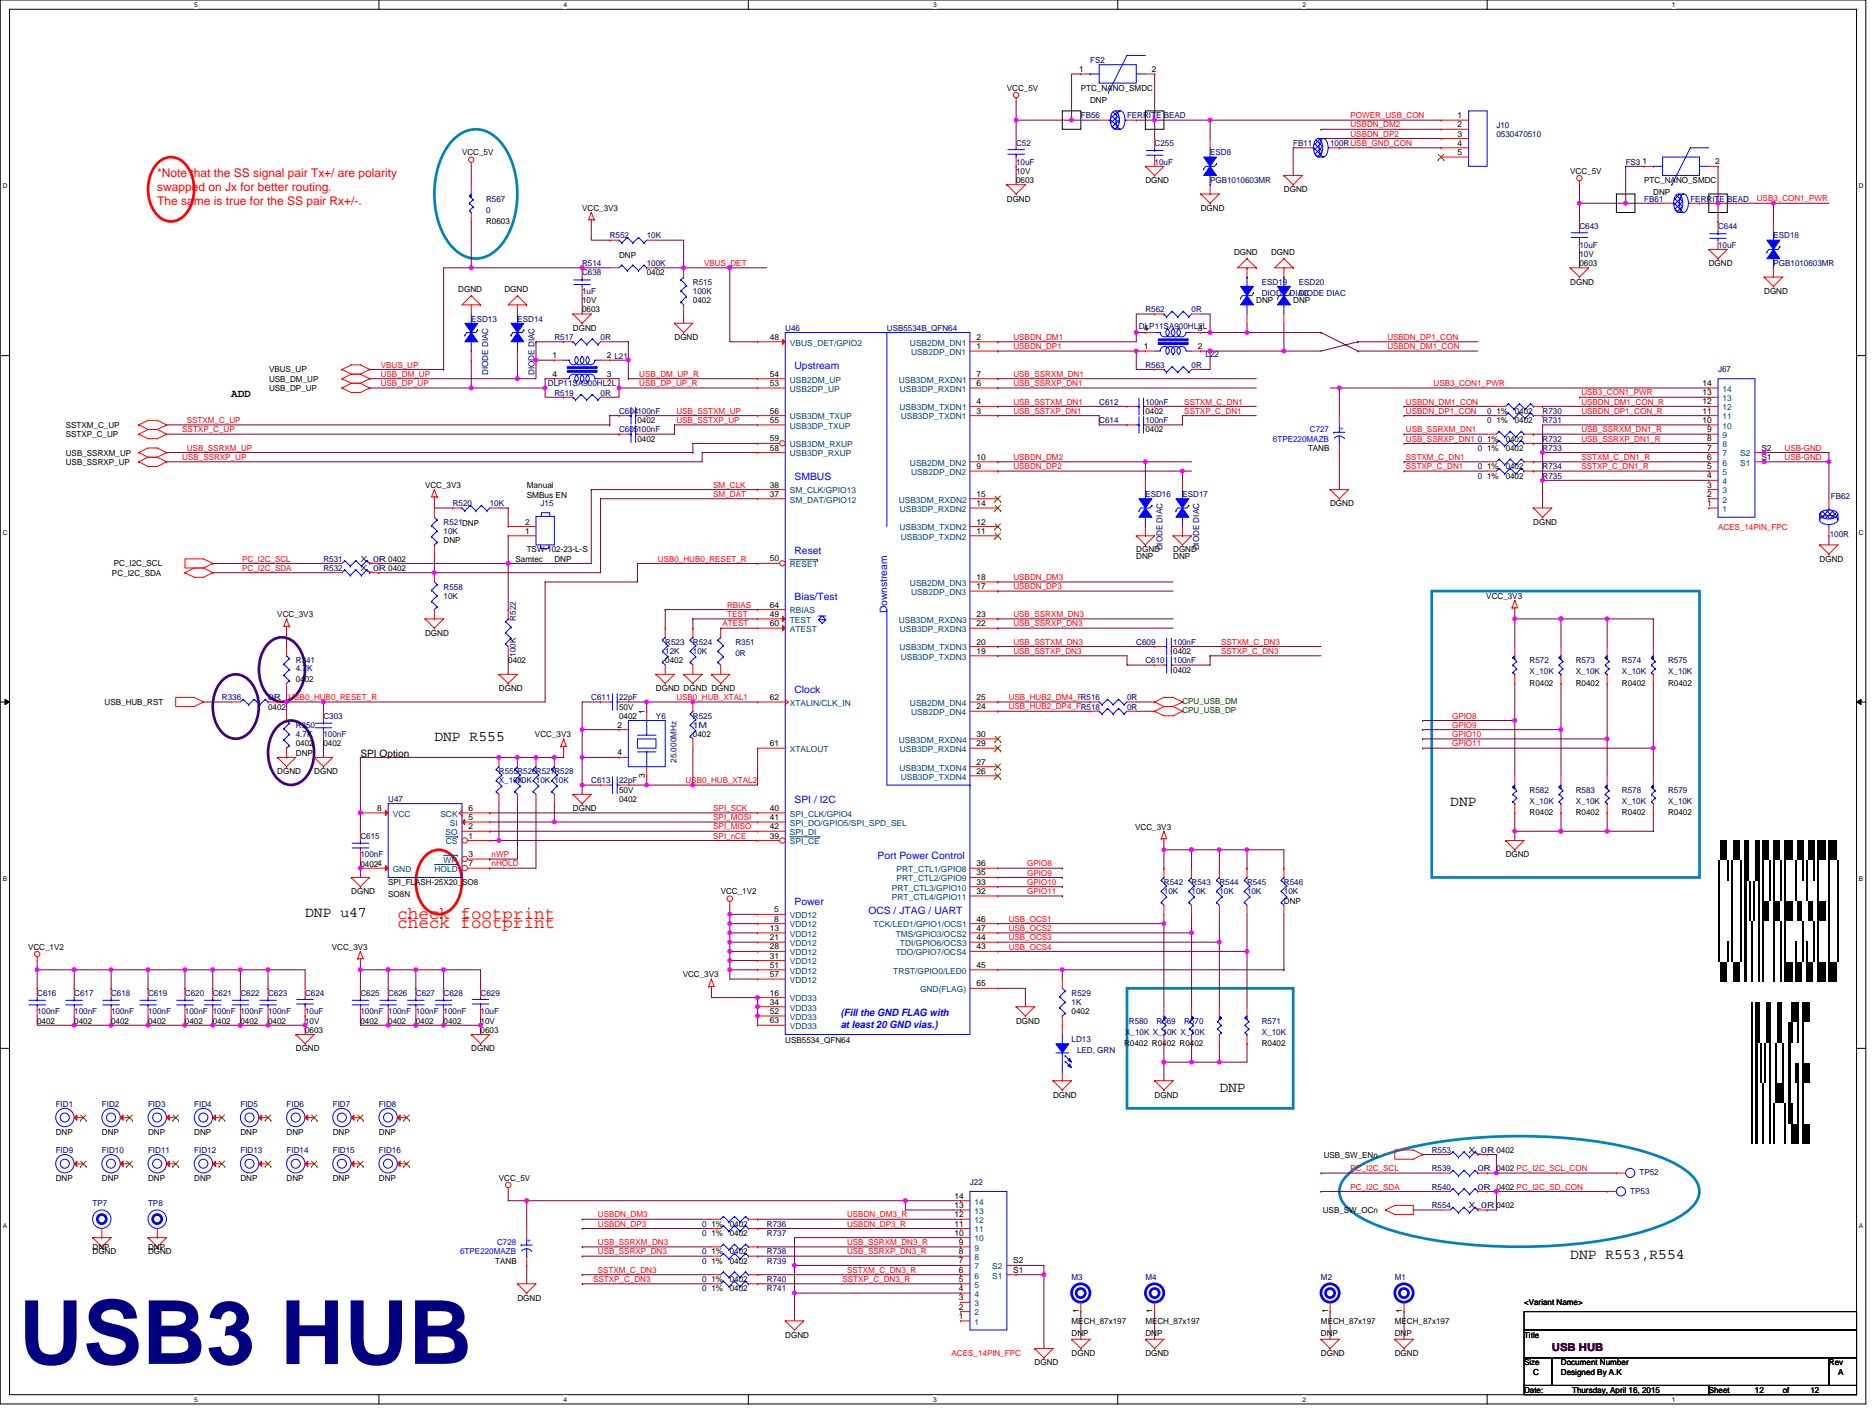
[picture p77: page 12]

The same is true for the SS pair Rx+/-.

VDD12 13 | USB_OCS2
VDD12 21 | USB_OCS3
VDD12 28 | USB_OCS4

(Fill the GND FLAG with
at least 20 GND vias.)
