OSVR/OSVR-HDK/HDK Ver 1.2/electricals/schematics/hmd_box_2015_0323_1800.pdf

HMD_CON_DATA2+_A HMD_CON_DATA2-_A HMD_CON_DET_A HMD_CON_DATA1+_A HMD_CON_DATA1-_A HMD_CON_DATA0+_A HMD_CON_DATA0-_A HMD_CON_CLK+_A HMD_CON_CLK-_A

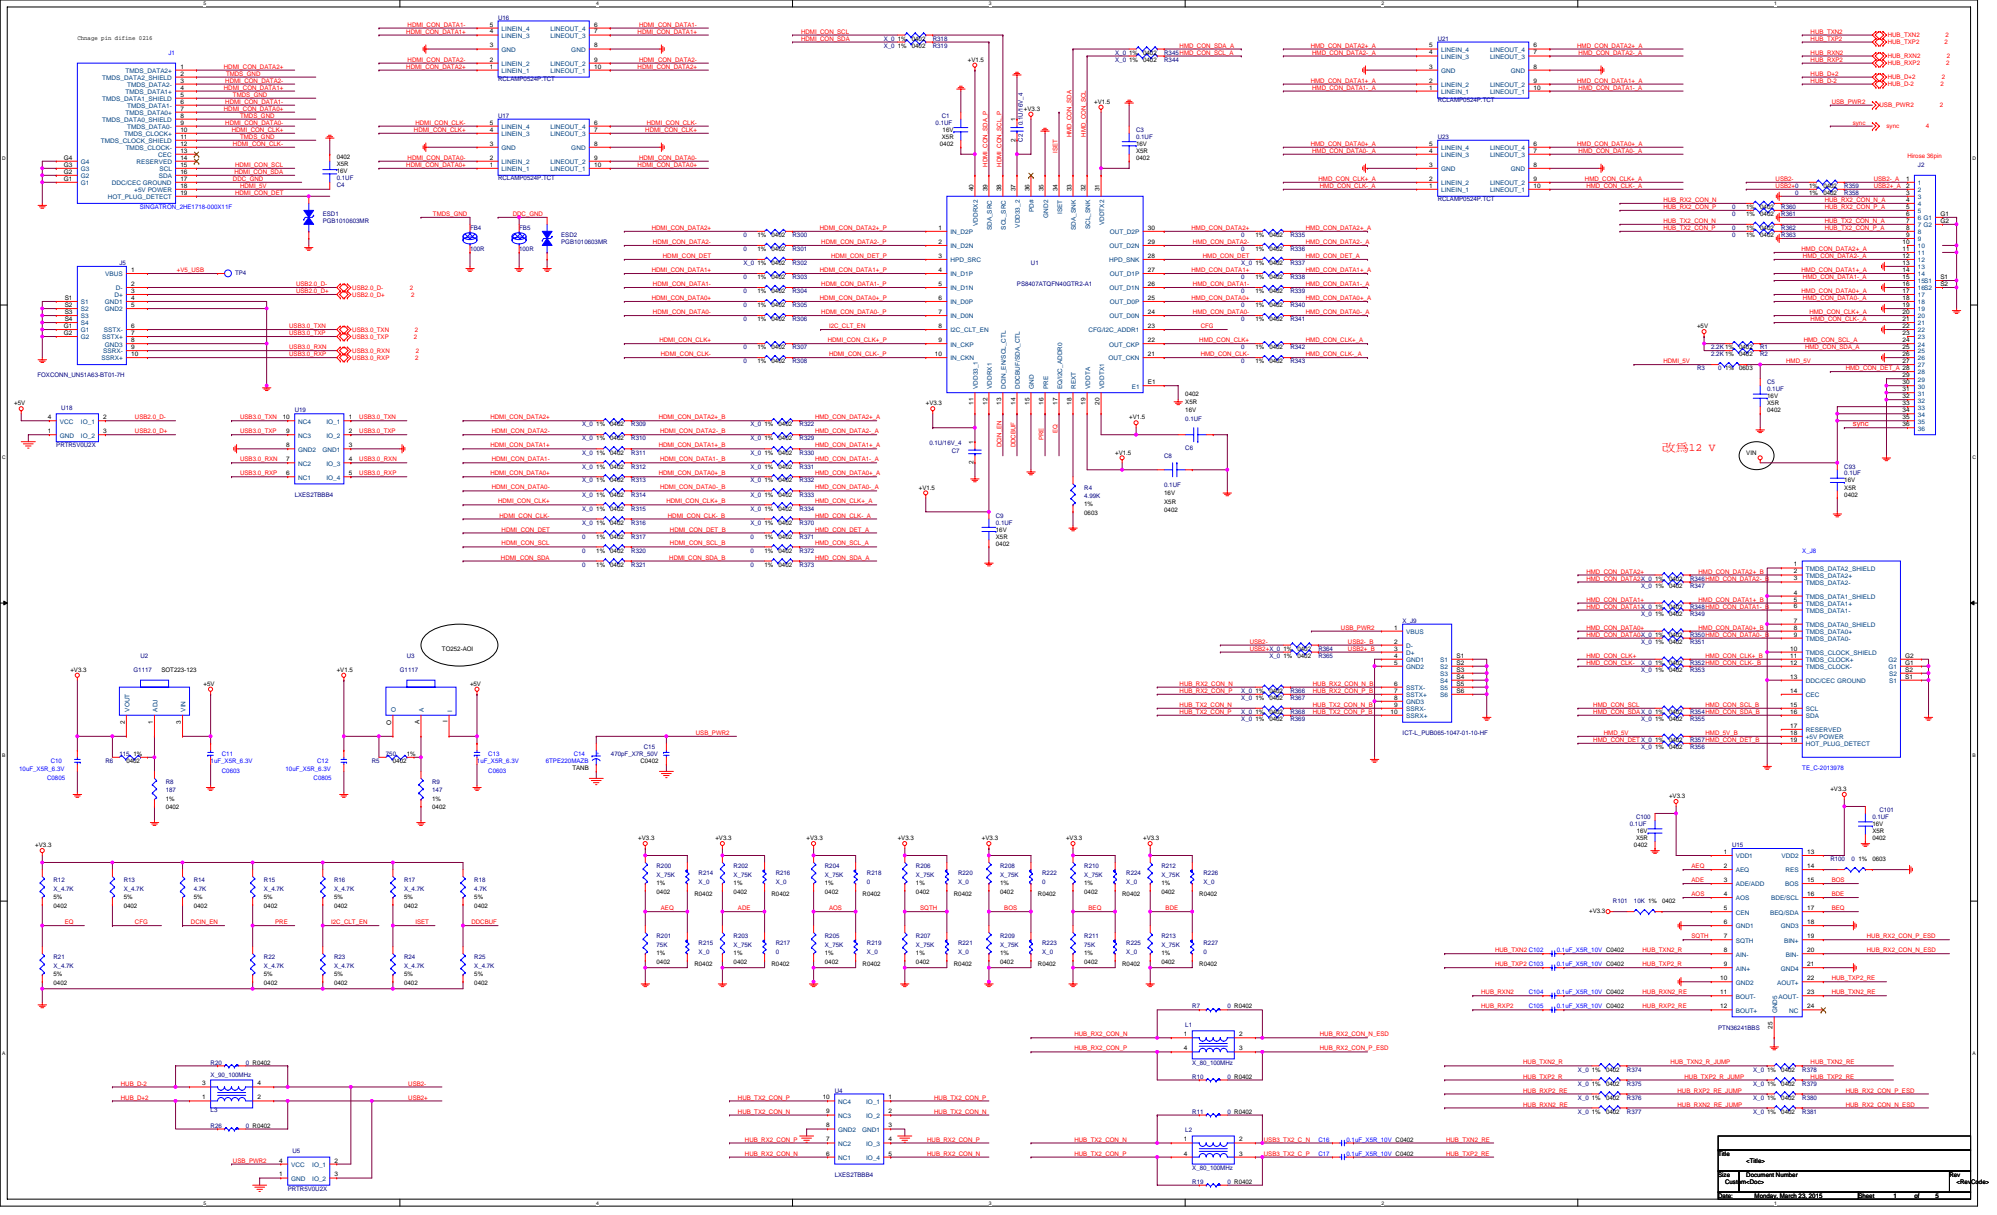
[picture p78: page 1]

## P_SPI_CK

## P_SPI_CZ

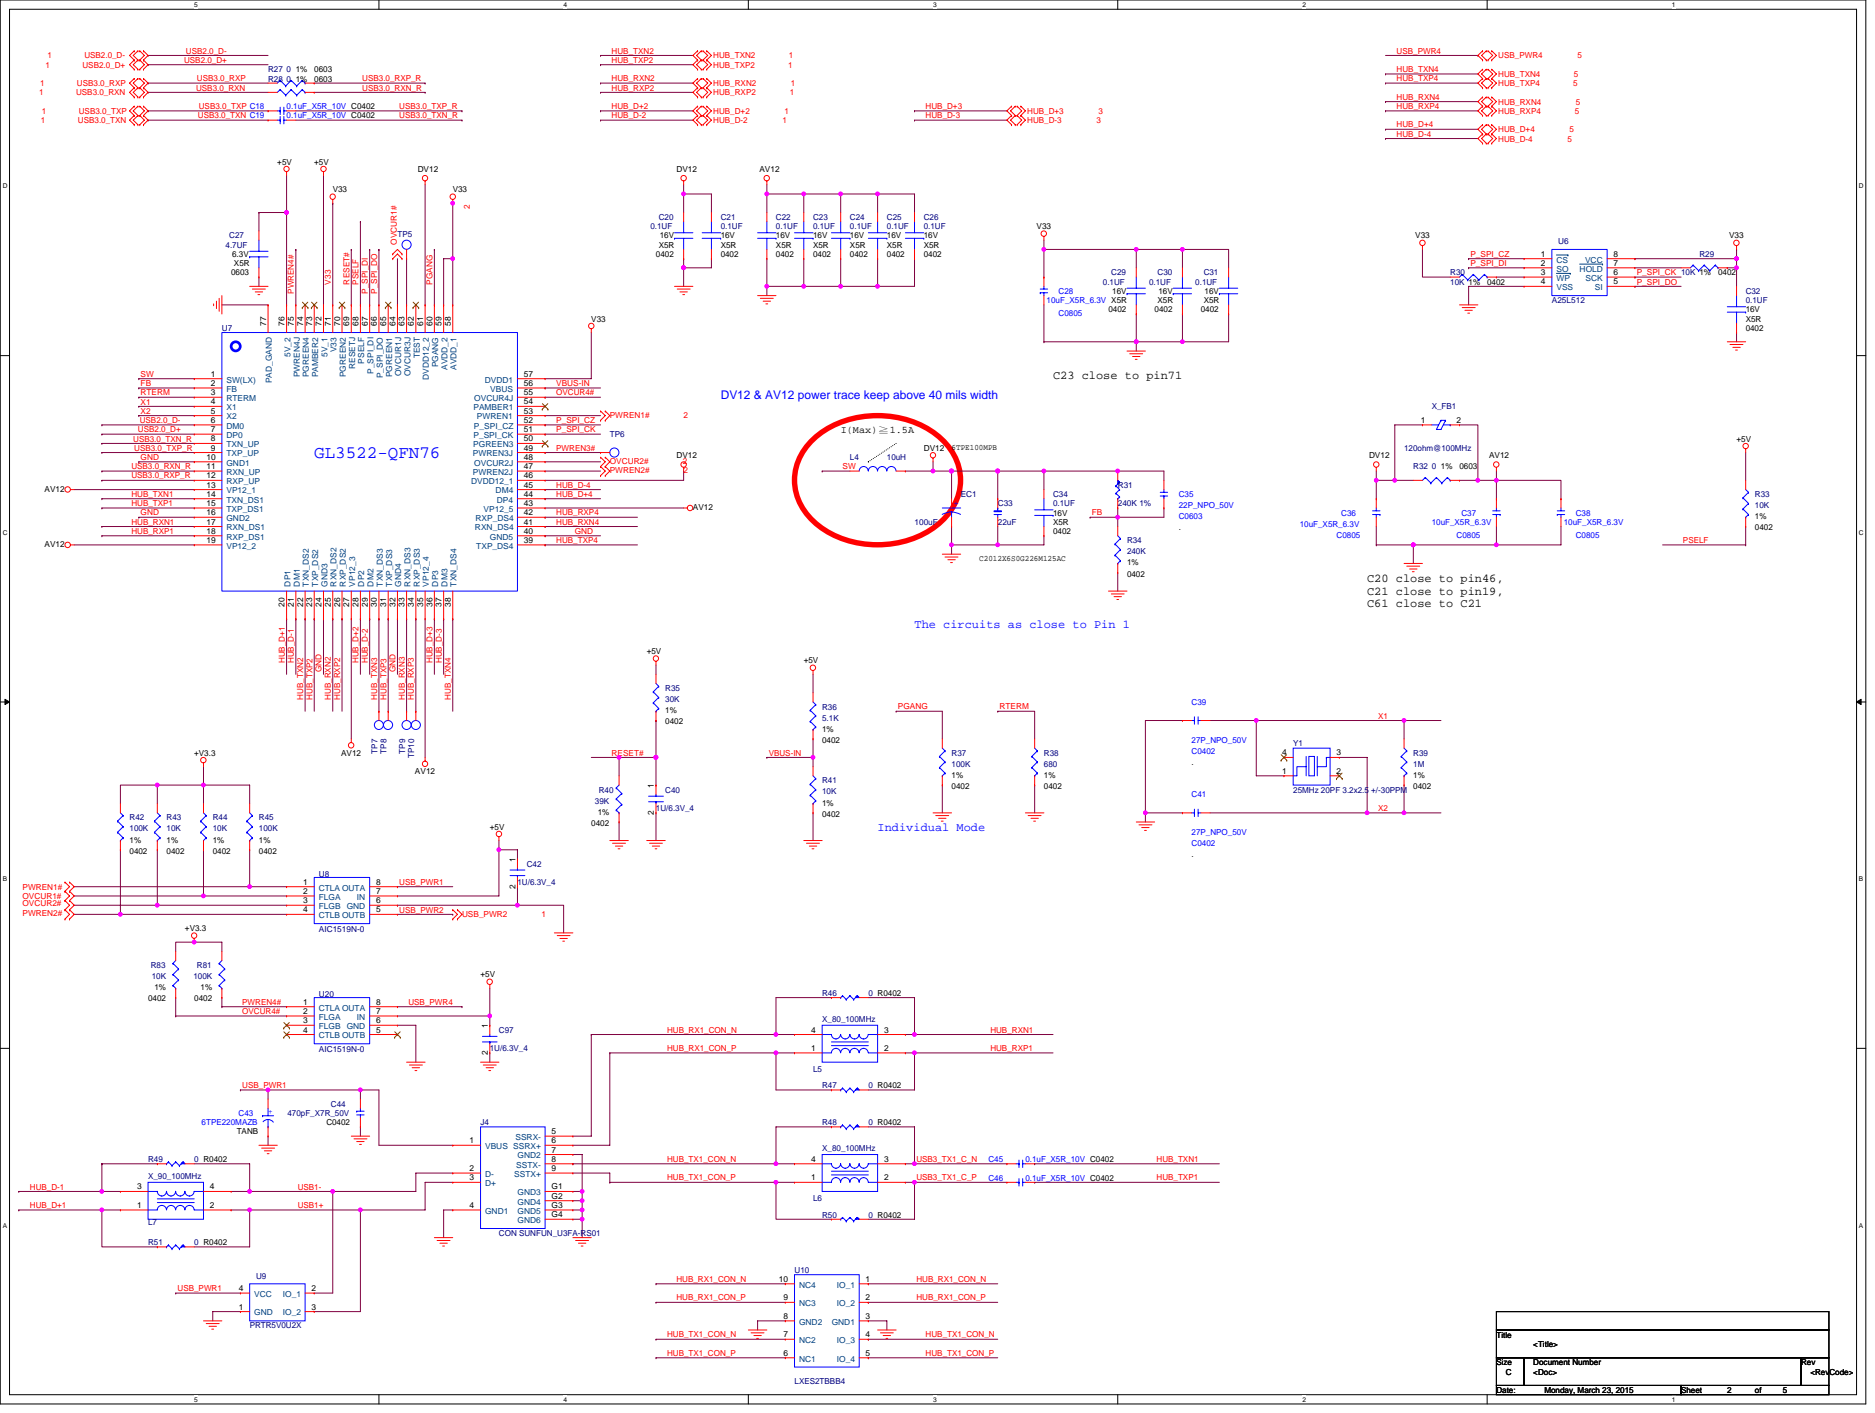
[picture p79: page 2]

TXN_DS4 38 TXP_DS4 39 GND5 40 RXN_DS4 41 RXP_DS4 42 VP12_5 43 DP4 44 DM4 45 DVDD12_1 46 PWREN2J 47 OVCUR2J 48 PWREN3J 49 PGREEN3 50 P_SPI_CK 51 P_SPI_CZ 52 PWREN1 53 PAMBER1 54 OVCUR4J 55 VBUS 56 DVDD1 57 AVDD_1 58 AVDD_2 59 PGANG 60 DVDD12_2 61 TEST 62 OVCUR3J 63 OVCUR1J 64 PGREEN1 65 P_SPI_DO 66 P_SPI_DI 67 PSELF 68 RESETJ 69 PGREEN2 70 V33 71 5V_1 72 PAMBER2 73 PGREEN4 74 PWREN4J 75 5V_2 76

DV12 & AV12 power trace keep above 40 mils width

The circuits as close to Pin 1

## change to shortpad

## reference ckt is 100k ohm

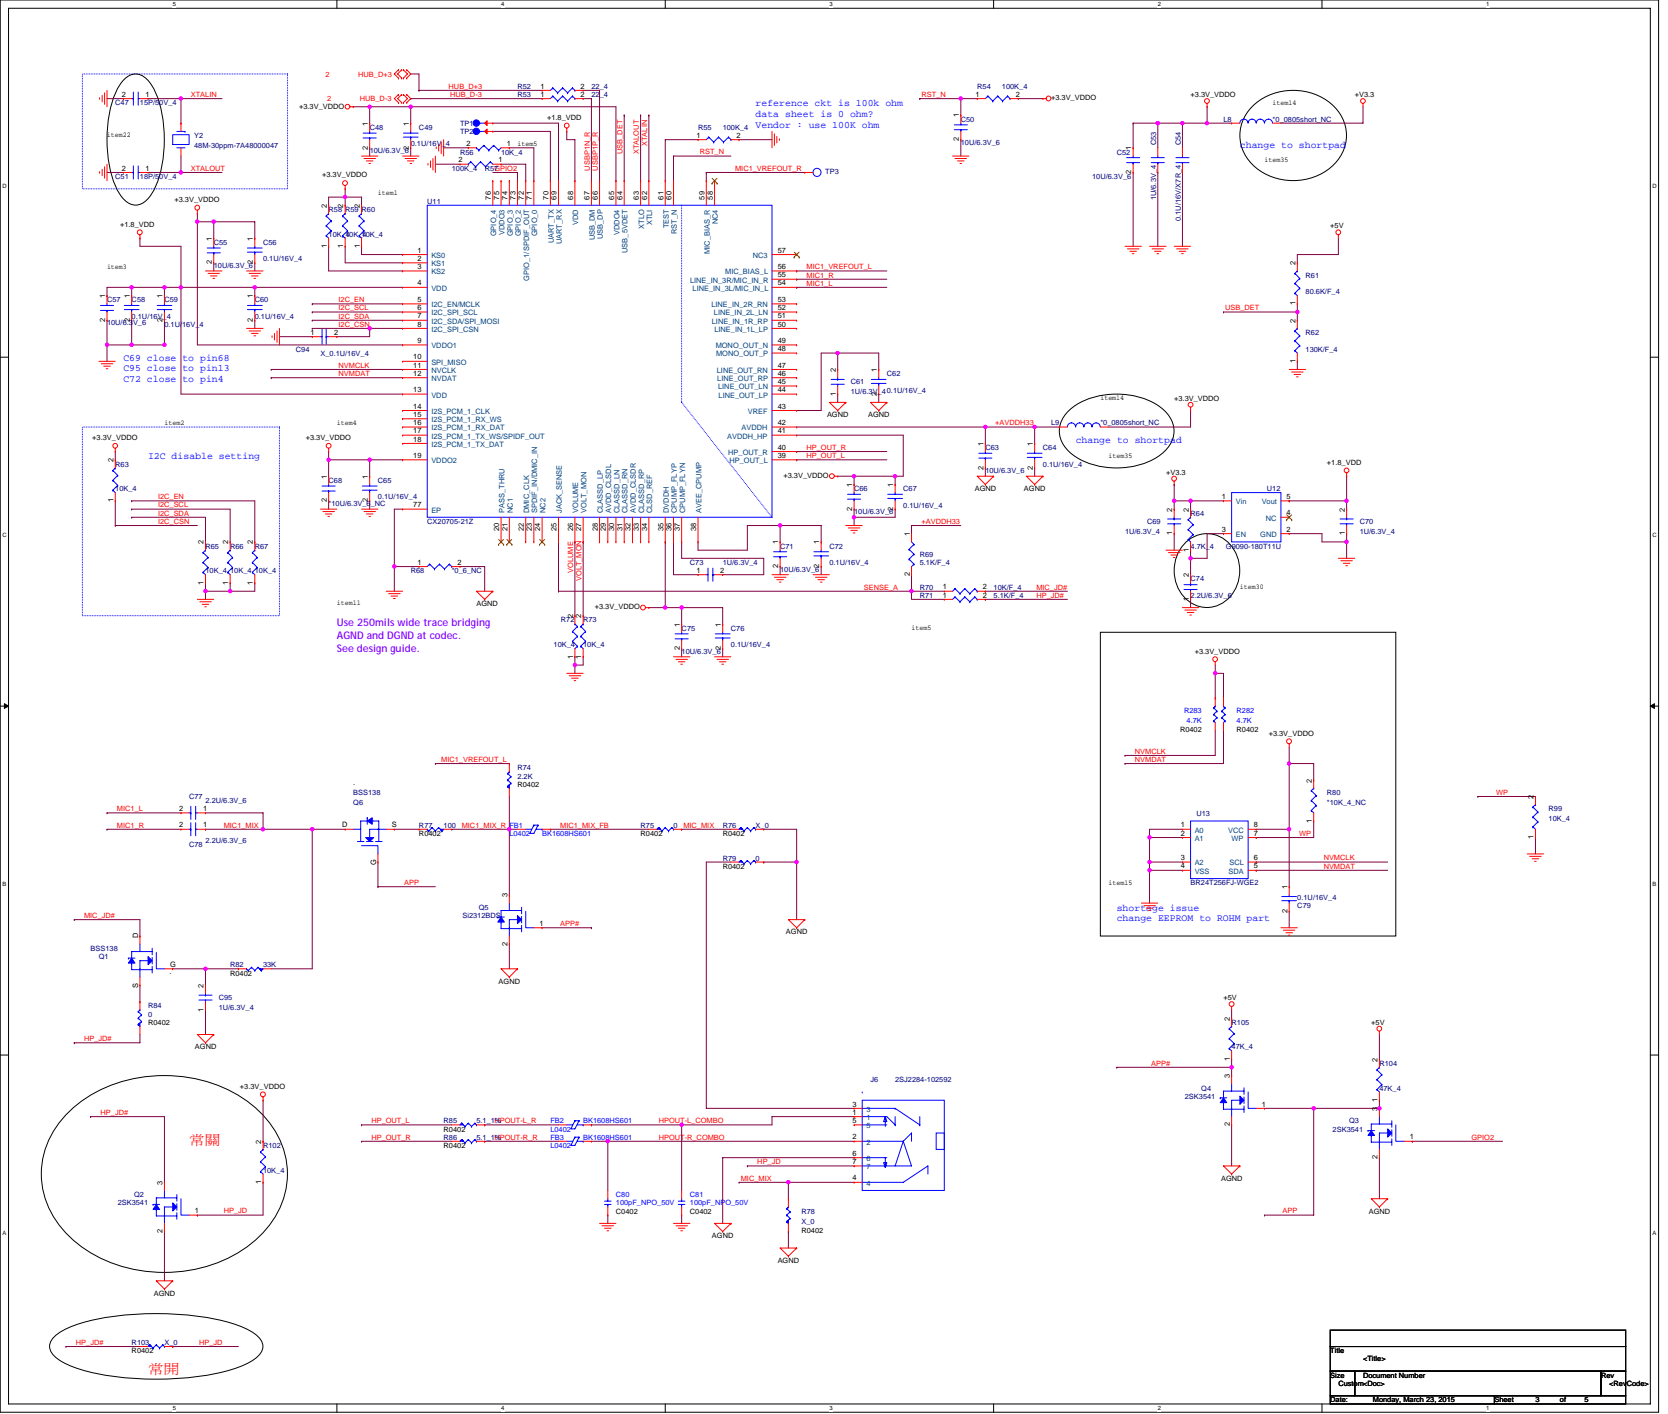
[picture p80: page 3]

data sheet is 0 ohm?
Vendor : use 100K ohm

item11
Use 250mils wide trace bridging
AGND and DGND at codec.
See design guide.

shortage issue
change EEPROM to ROHM part

D | D

# Change Package to 1206 and add 10UF/25V

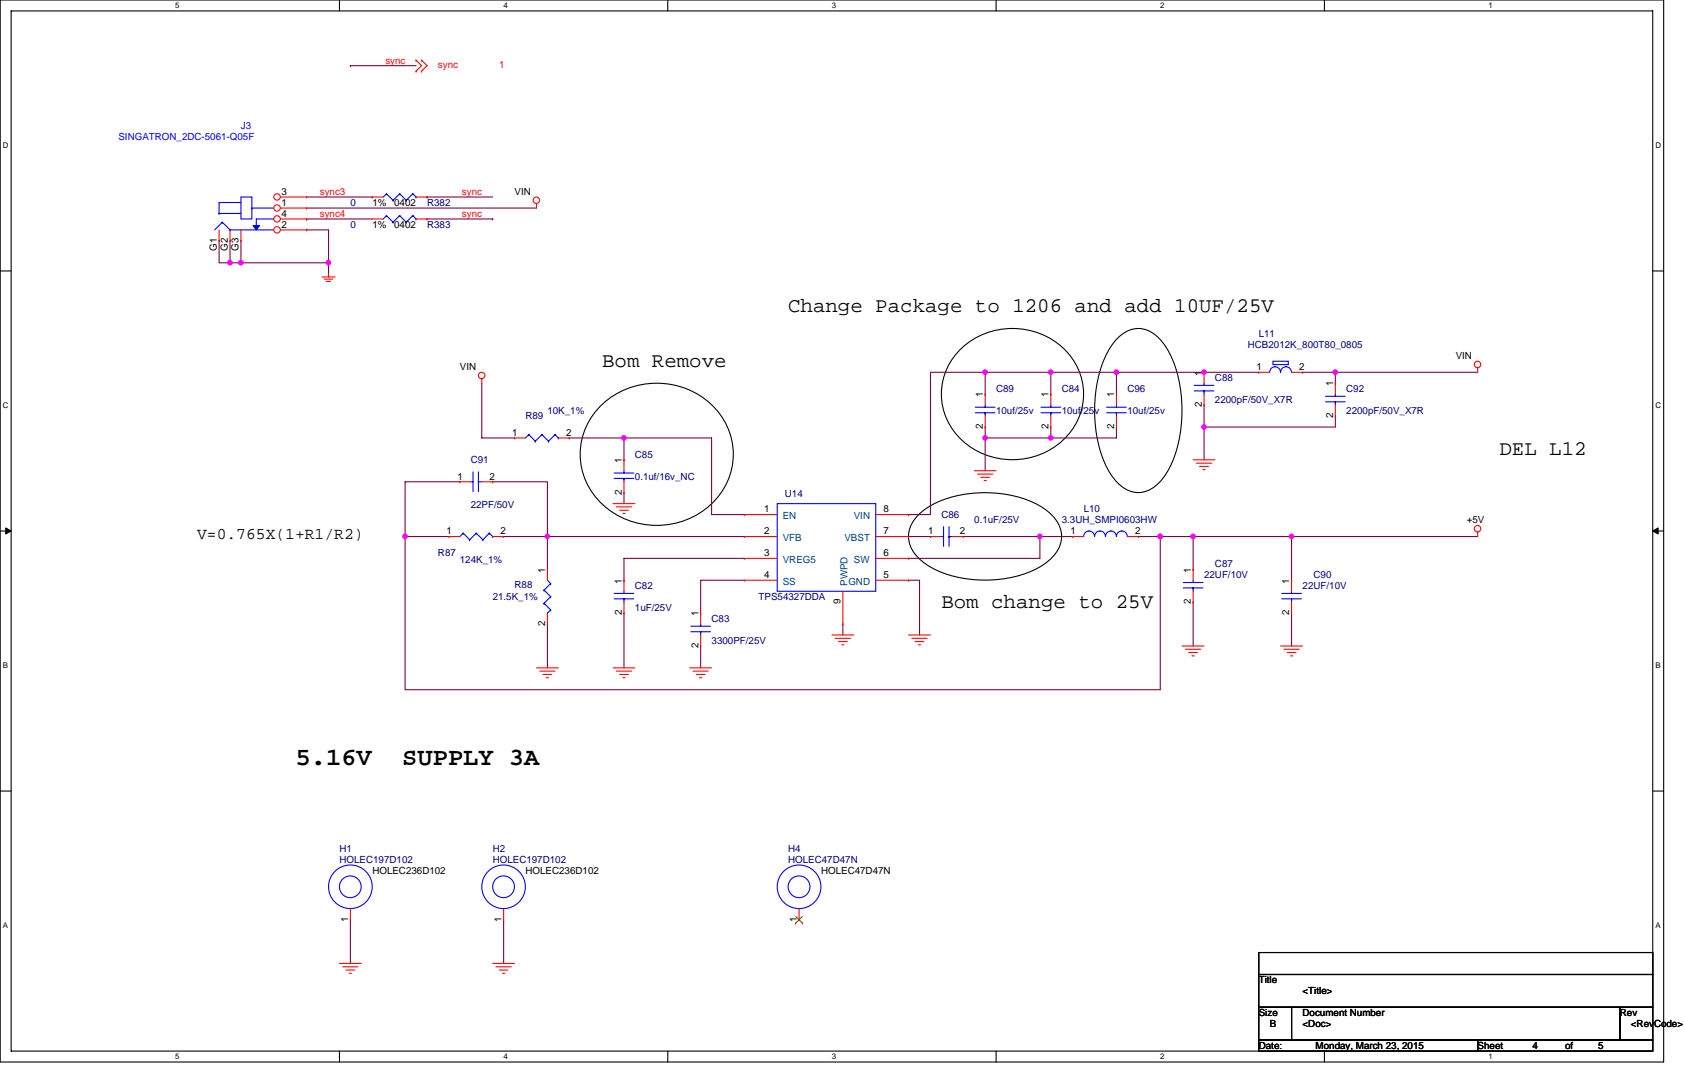
[picture p81: page 4]

Size Size Size B B B | Document Number Document Number Document Number | Rev Rev Rev

Date: Date: Date: Monday, March 23, 2015 Monday, March 23, 2015 Monday, March 23, 2015 | Sheet Sheet Sheet 4 4 4 of of of 5 5 5

D | D

# HUB_RXN4

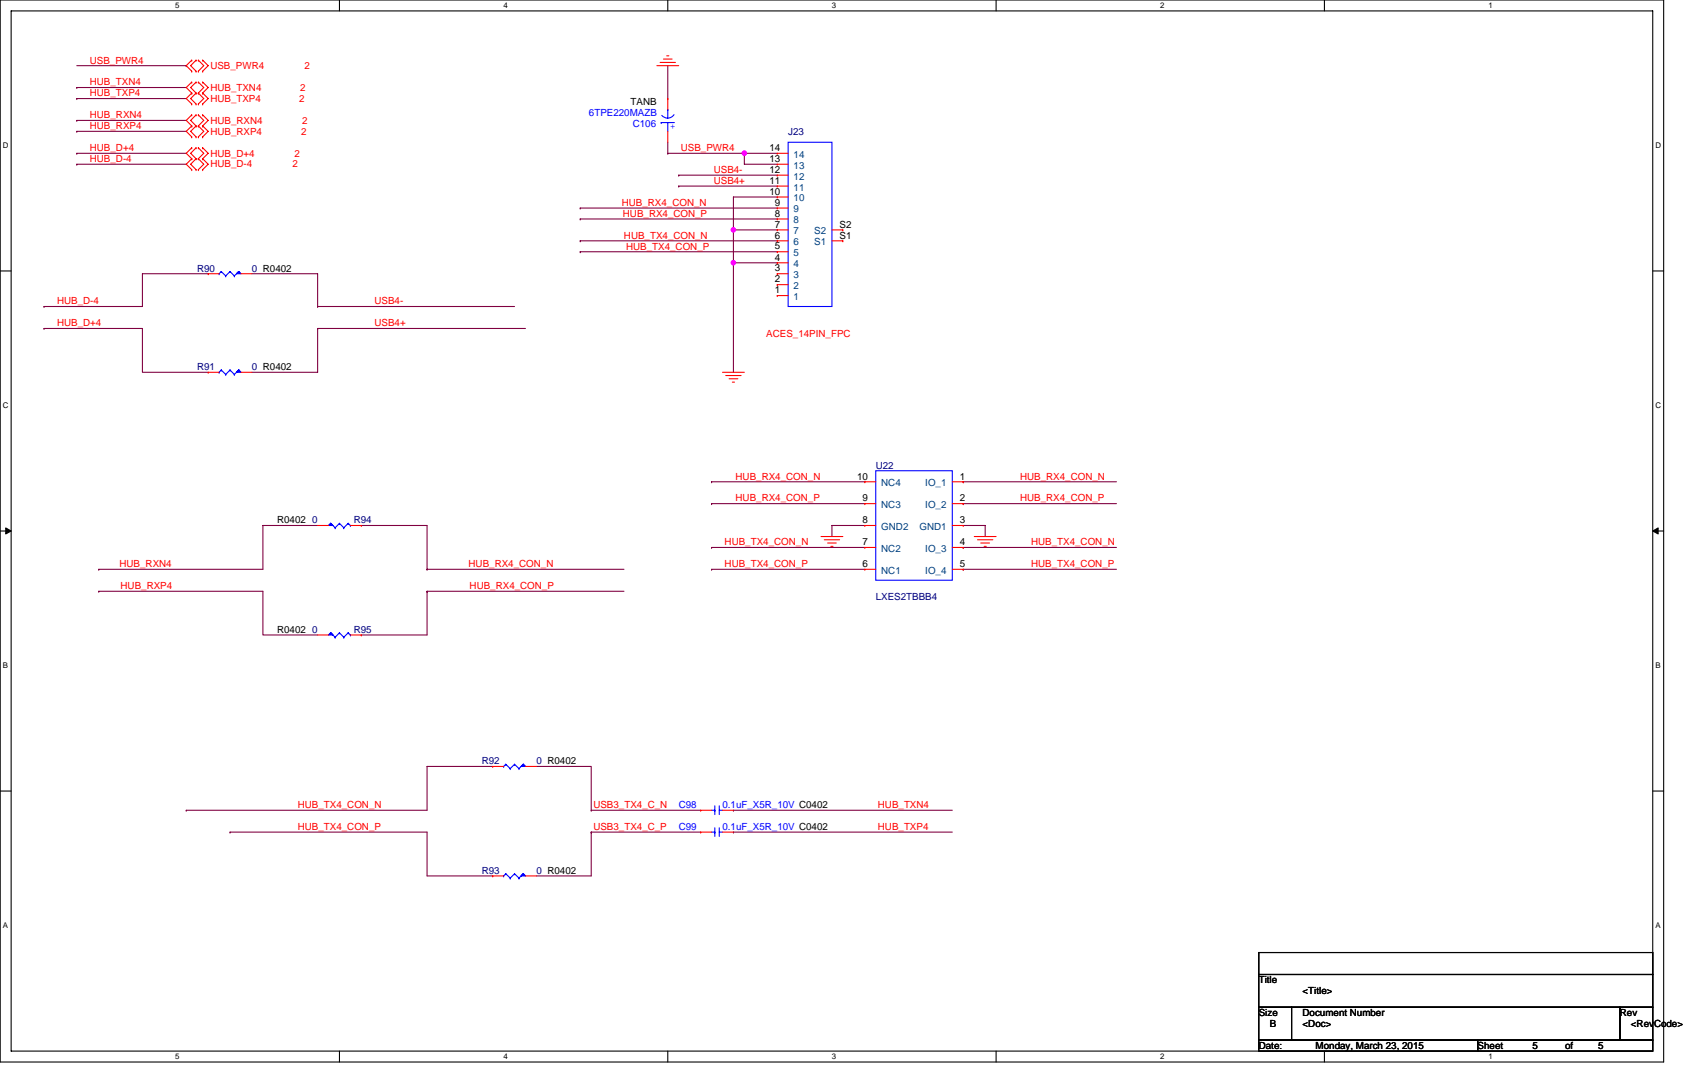
[picture p82: page 5]

Size Size Size B B B | Document Number Document Number Document Number | Rev Rev Rev

Date: Date: Date: Monday, March 23, 2015 Monday, March 23, 2015 Monday, March 23, 2015 | Sheet Sheet Sheet 5 5 5 of of of 5 5 5
