OSVR/OSVR-HDK/HDK Ver 1.1/electronics/Schematics/display board_1226.pdf

# Socket

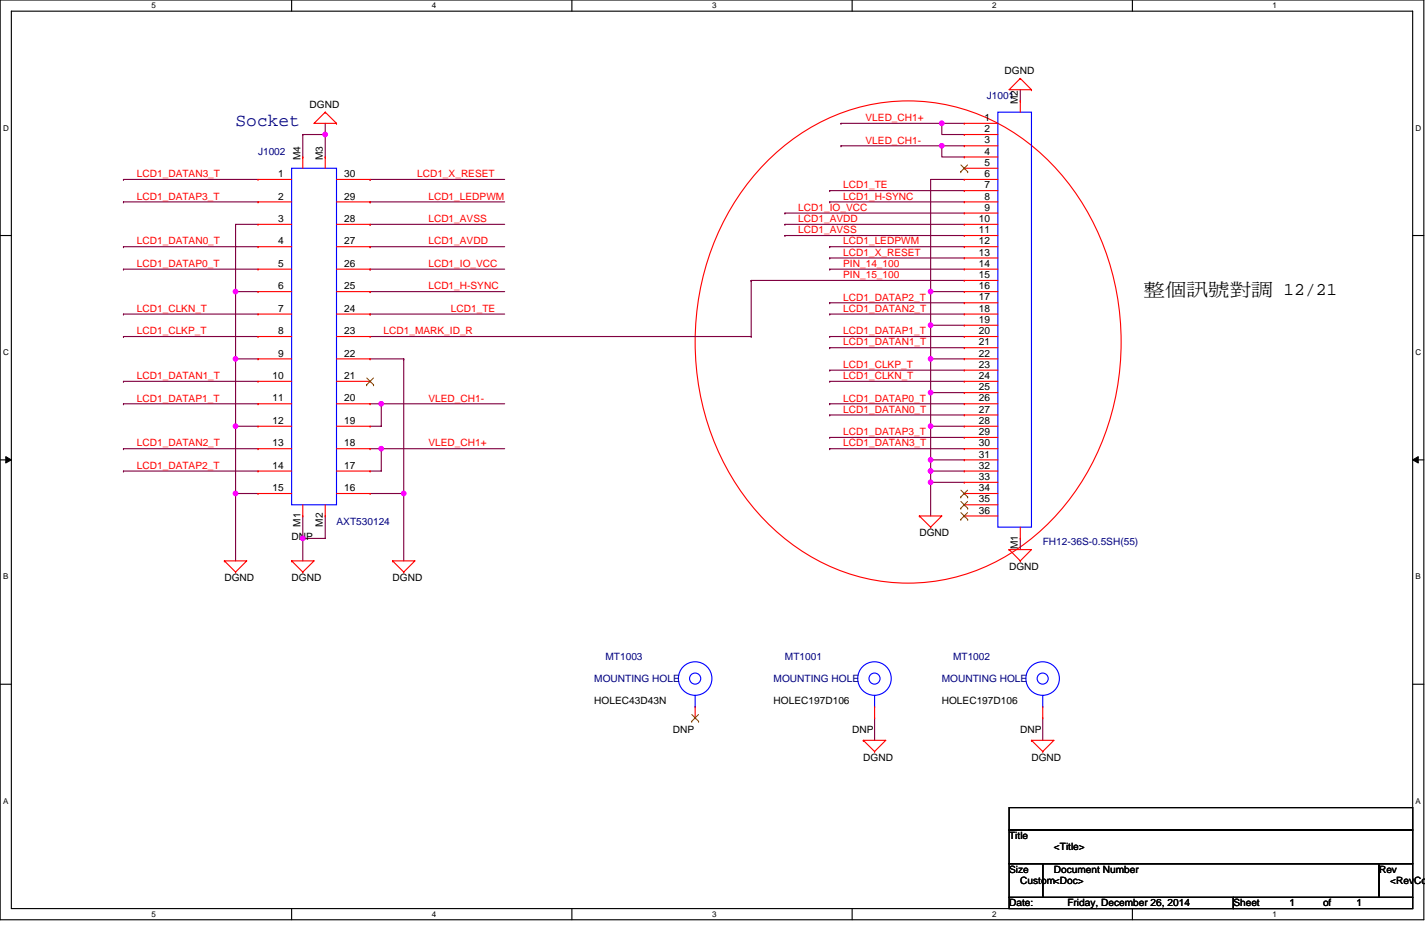
[picture p83: page 1]
整個訊號對調 12/21; VLED_CH1+; VLED_CH1-; LCD1_AVDD; LCD1_LEDPWM LCD1_X_RESET; LCD1_DATAP3_T; LCD1_DATAN0_T; LCD1_DATAP0_T; LCD1_DATAN1_T; LCD1_DATAP1_T; LCD1_DATAN2_T; LCD1_DATAP2_T; LCD1_DATAN3_T; LCD1_CLKN_T; LCD1_CLKP_T; LCD1_TE LCD1_H-SYNC LCD1_IO_VCC; PIN_14_100 PIN_15_100; LCD1_AVSS; LCD1_TE; LCD1_IO_VCC; LCD1_LEDPWM; LCD1_X_RESET; LCD1_H-SYNC; LCD1_MARK_ID_R; DGND; Title; <Doc>; <RevCo; <Title>; MOUNTING HOLE; HOLEC197D106; DNP; AXT530124; HOLEC43D43N

Size Size Size Custom Custom Custom | Document Number Document Number Document Number | Rev Rev Rev

Date: Date: Date: Friday, December 26, 2014 Friday, December 26, 2014 Friday, December 26, 2014 | Sheet Sheet Sheet 1 1 1 of of of 1 1 1
