OSVR/OSVR-HDK/HDK Ver 1.1/electronics/Schematics/hmd_box_2015_0106.pdf

# Remove R90~R101 R99不需移除 12/21

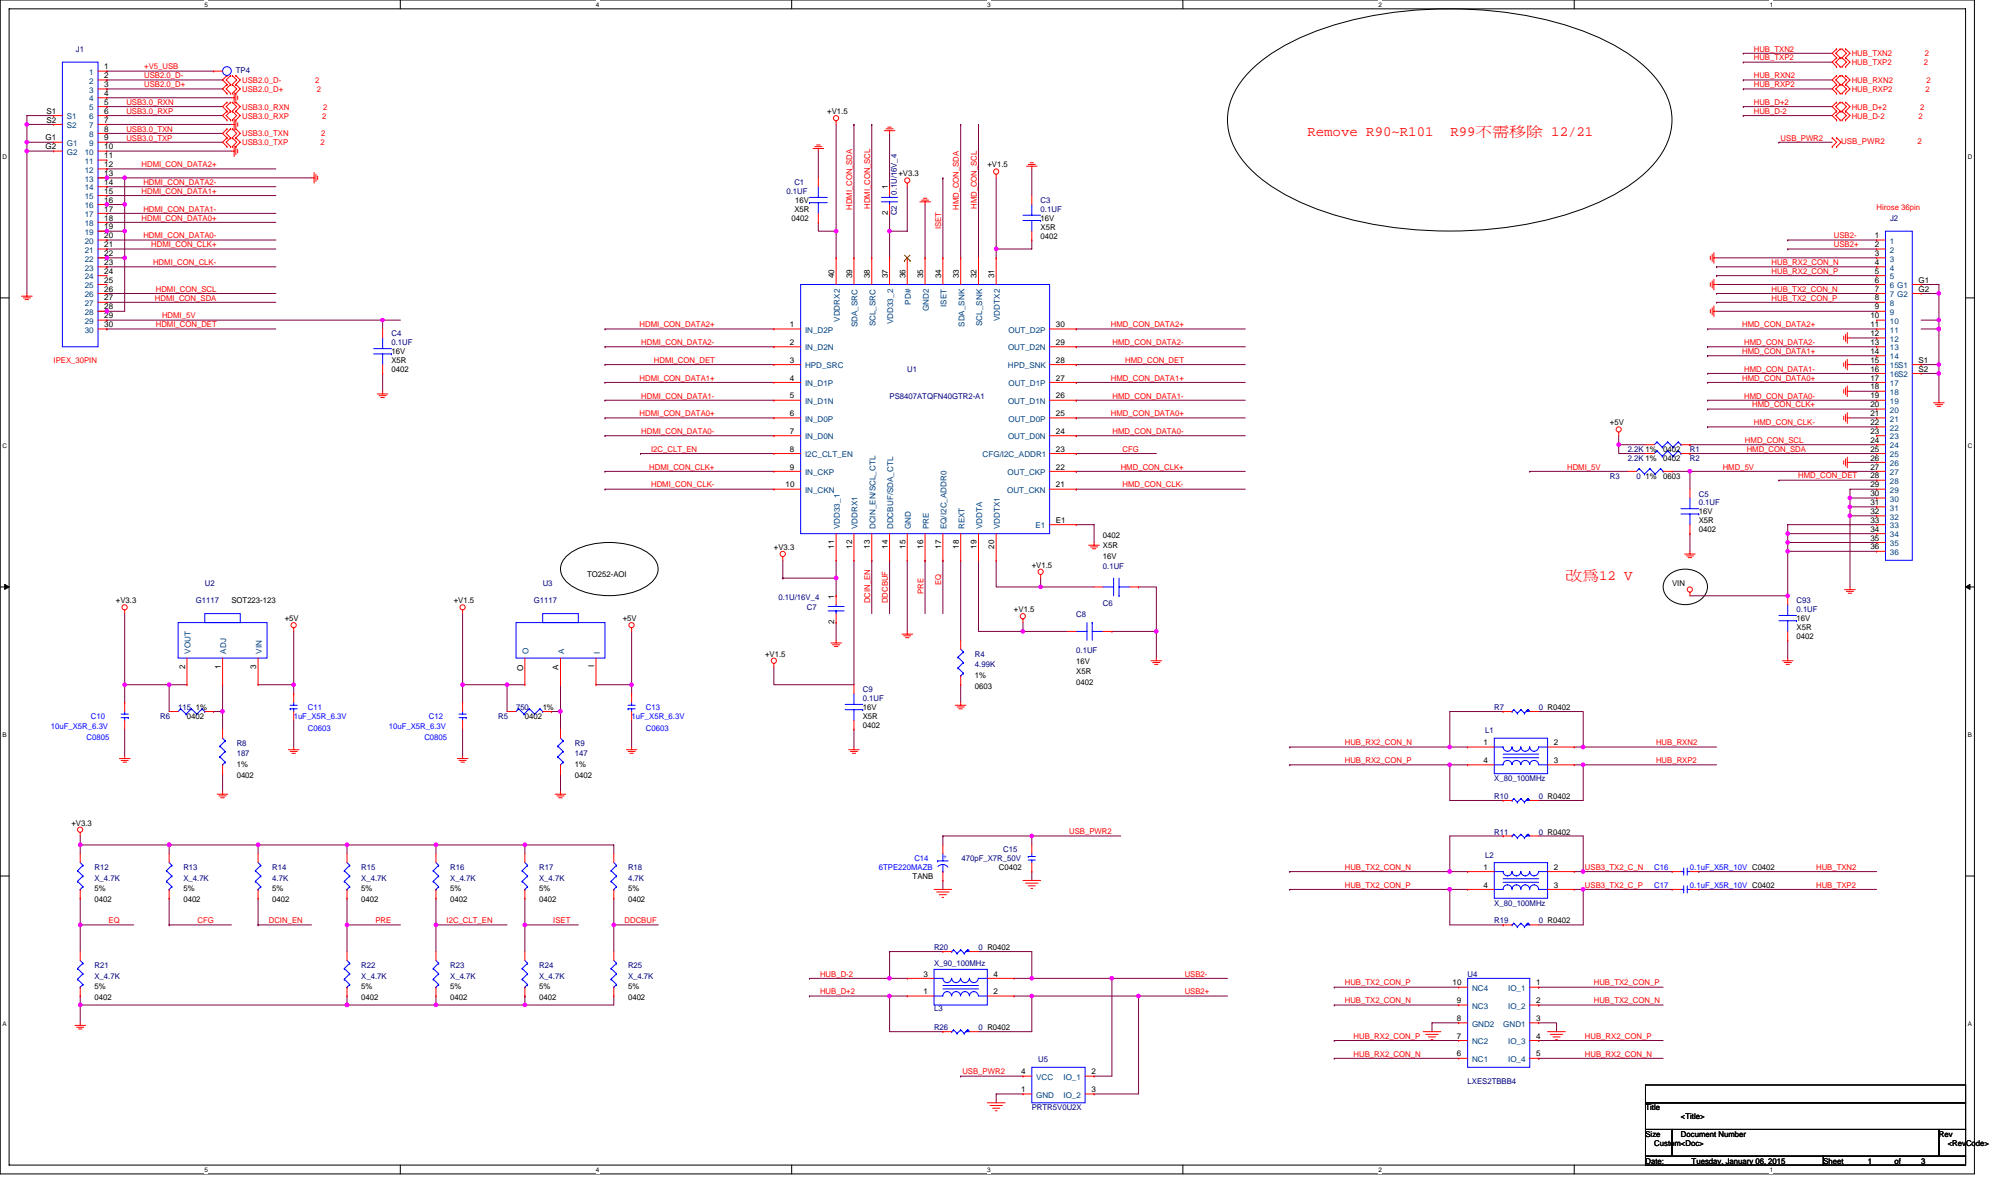
[picture p84: page 1]

D | D

# Change Package to 1206 and add 10UF/25V

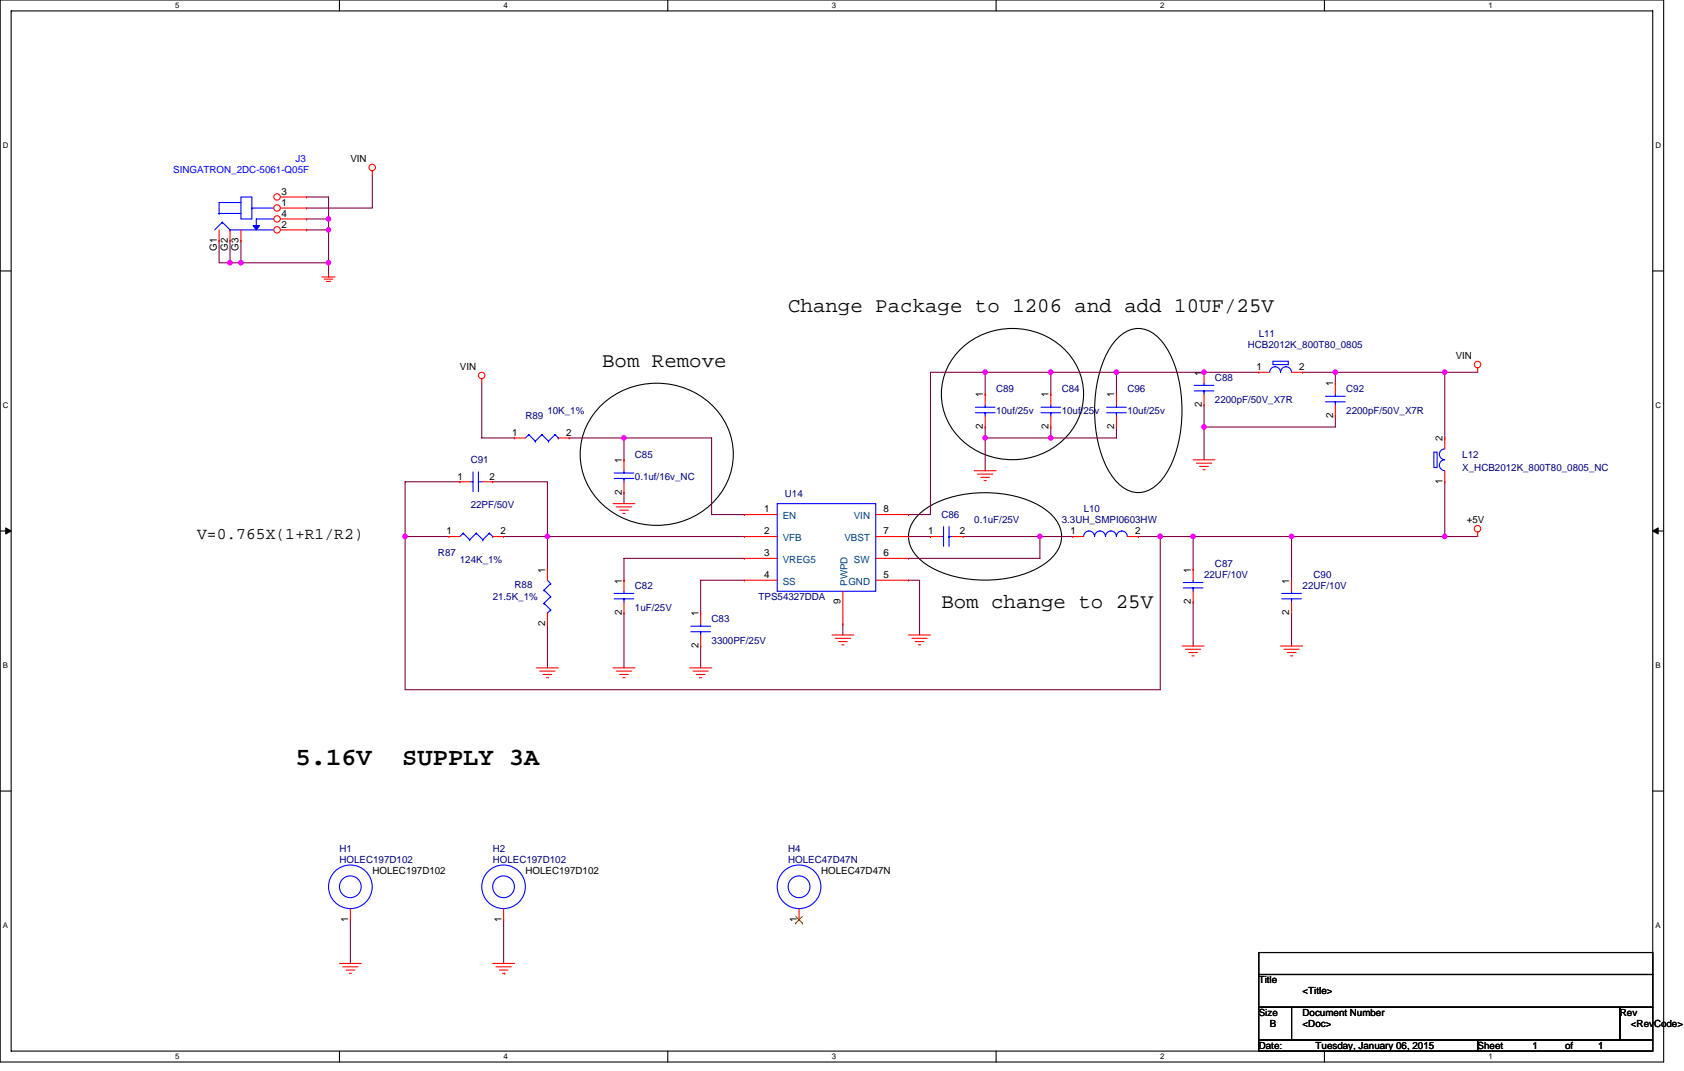
[picture p85: page 2]

Size Size Size B B B | Document Number Document Number Document Number | Rev Rev Rev

Date: Date: Date: Tuesday, January 06, 2015 Tuesday, January 06, 2015 Tuesday, January 06, 2015 | Sheet Sheet Sheet 1 1 1 of of of 1 1 1

D | D

D-

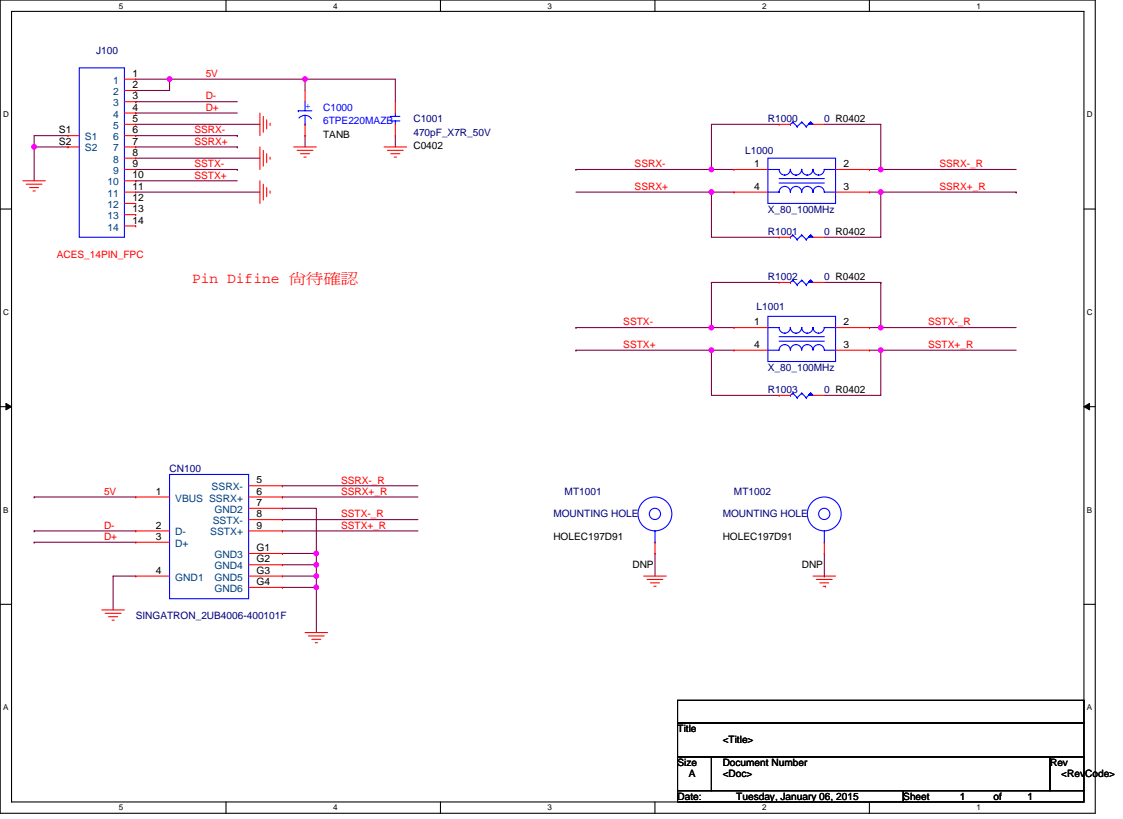
[picture p86: page 3]

Size A A A | Document Number | Rev

Date: Tuesday, January 06, 2015 Tuesday, January 06, 2015 Tuesday, January 06, 2015 | Sheet 1 1 1 of 1 1 1

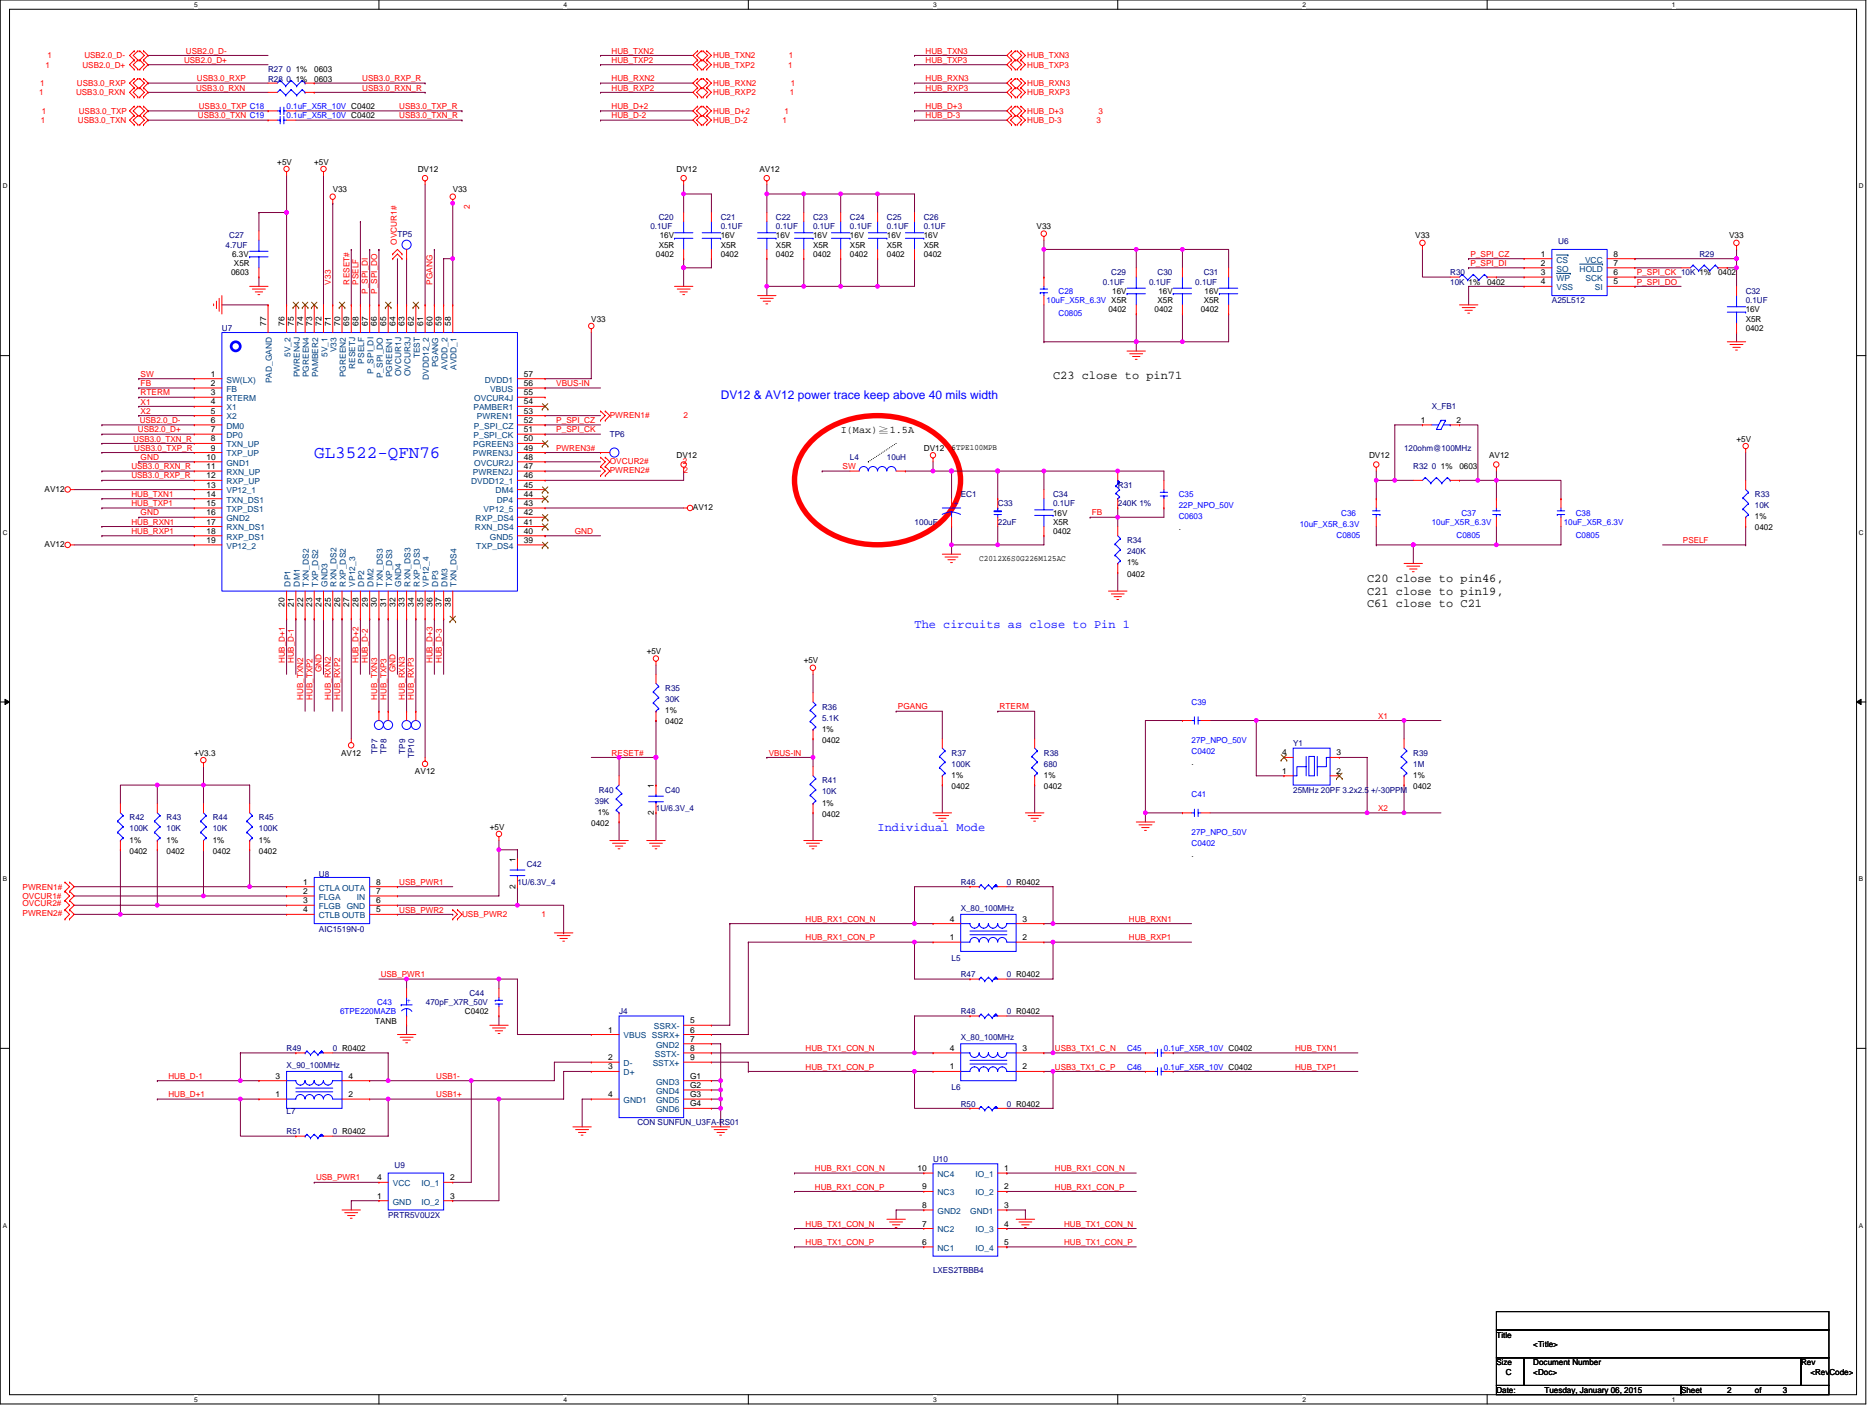
[picture p87: page 4]

TXN_DS4 38 TXP_DS4 39 GND5 40 RXN_DS4 41 RXP_DS4 42 VP12_5 43 DP4 44 DM4 45 DVDD12_1 46 PWREN2J 47 OVCUR2J 48 PWREN3J 49 PGREEN3 50 P_SPI_CK 51 P_SPI_CZ 52 PWREN1 53 PAMBER1 54 OVCUR4J 55 VBUS 56 DVDD1 57 AVDD_1 58 AVDD_2 59 PGANG 60 DVDD12_2 61 TEST 62 OVCUR3J 63 OVCUR1J 64 PGREEN1 65 P_SPI_DO 66 P_SPI_DI 67 PSELF 68 RESETJ 69 PGREEN2 70 V33 71 5V_1 72 PAMBER2 73 PGREEN4 74 PWREN4J 75 5V_2 76

DV12 & AV12 power trace keep above 40 mils width

The circuits as close to Pin 1

### change to shortpad

### reference ckt is 100k ohm

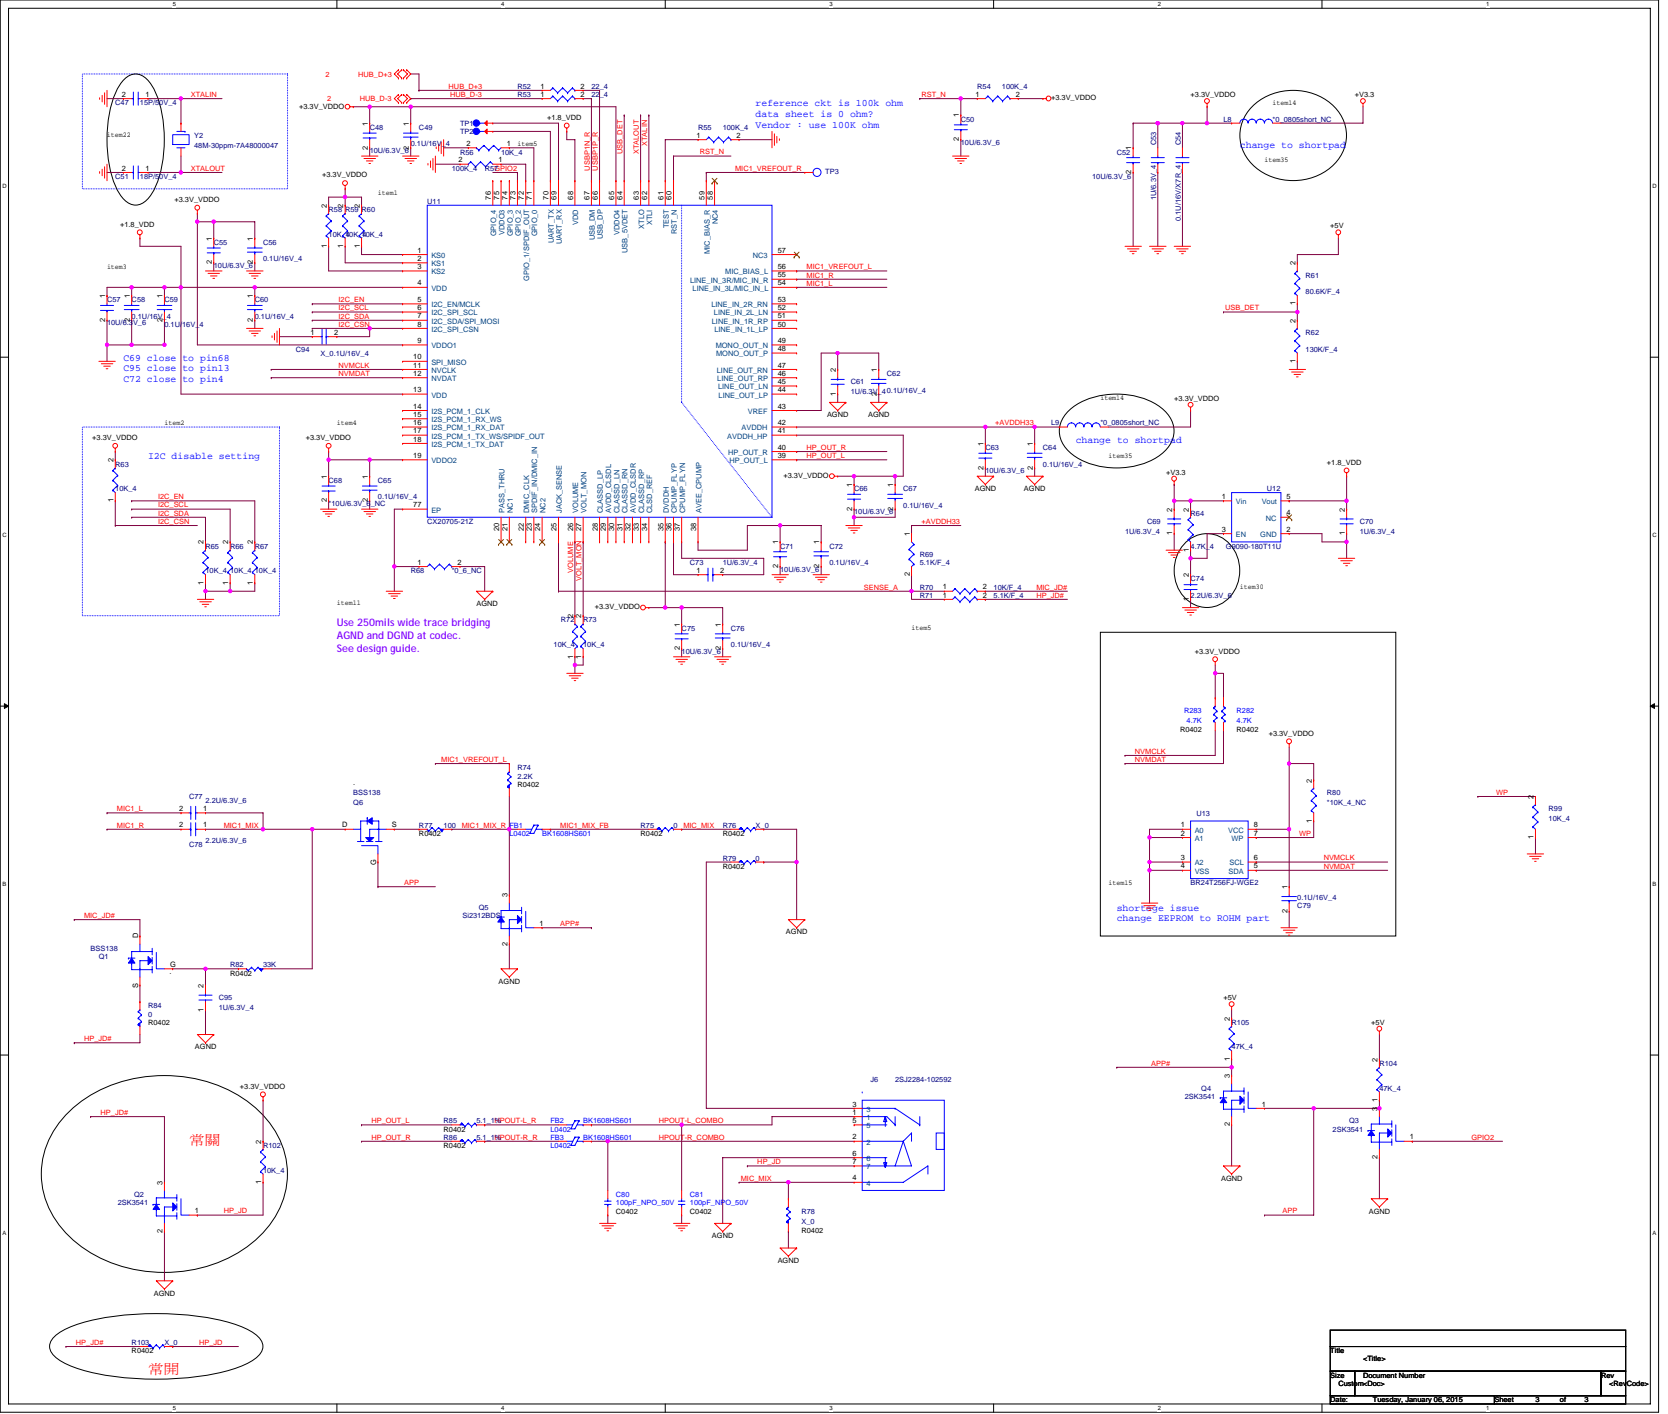
[picture p88: page 5]

data sheet is 0 ohm?
Vendor : use 100K ohm

item11
Use 250mils wide trace bridging
AGND and DGND at codec.
See design guide.

shortage issue
change EEPROM to ROHM part
