OSVR/OSVR-HDK/HDK Ver 1.2/electricals/gerber/front-cover-dvt2-gbr-all/front-cover-dvt2-dxf/front_cover_led-core-0508-03.pdf

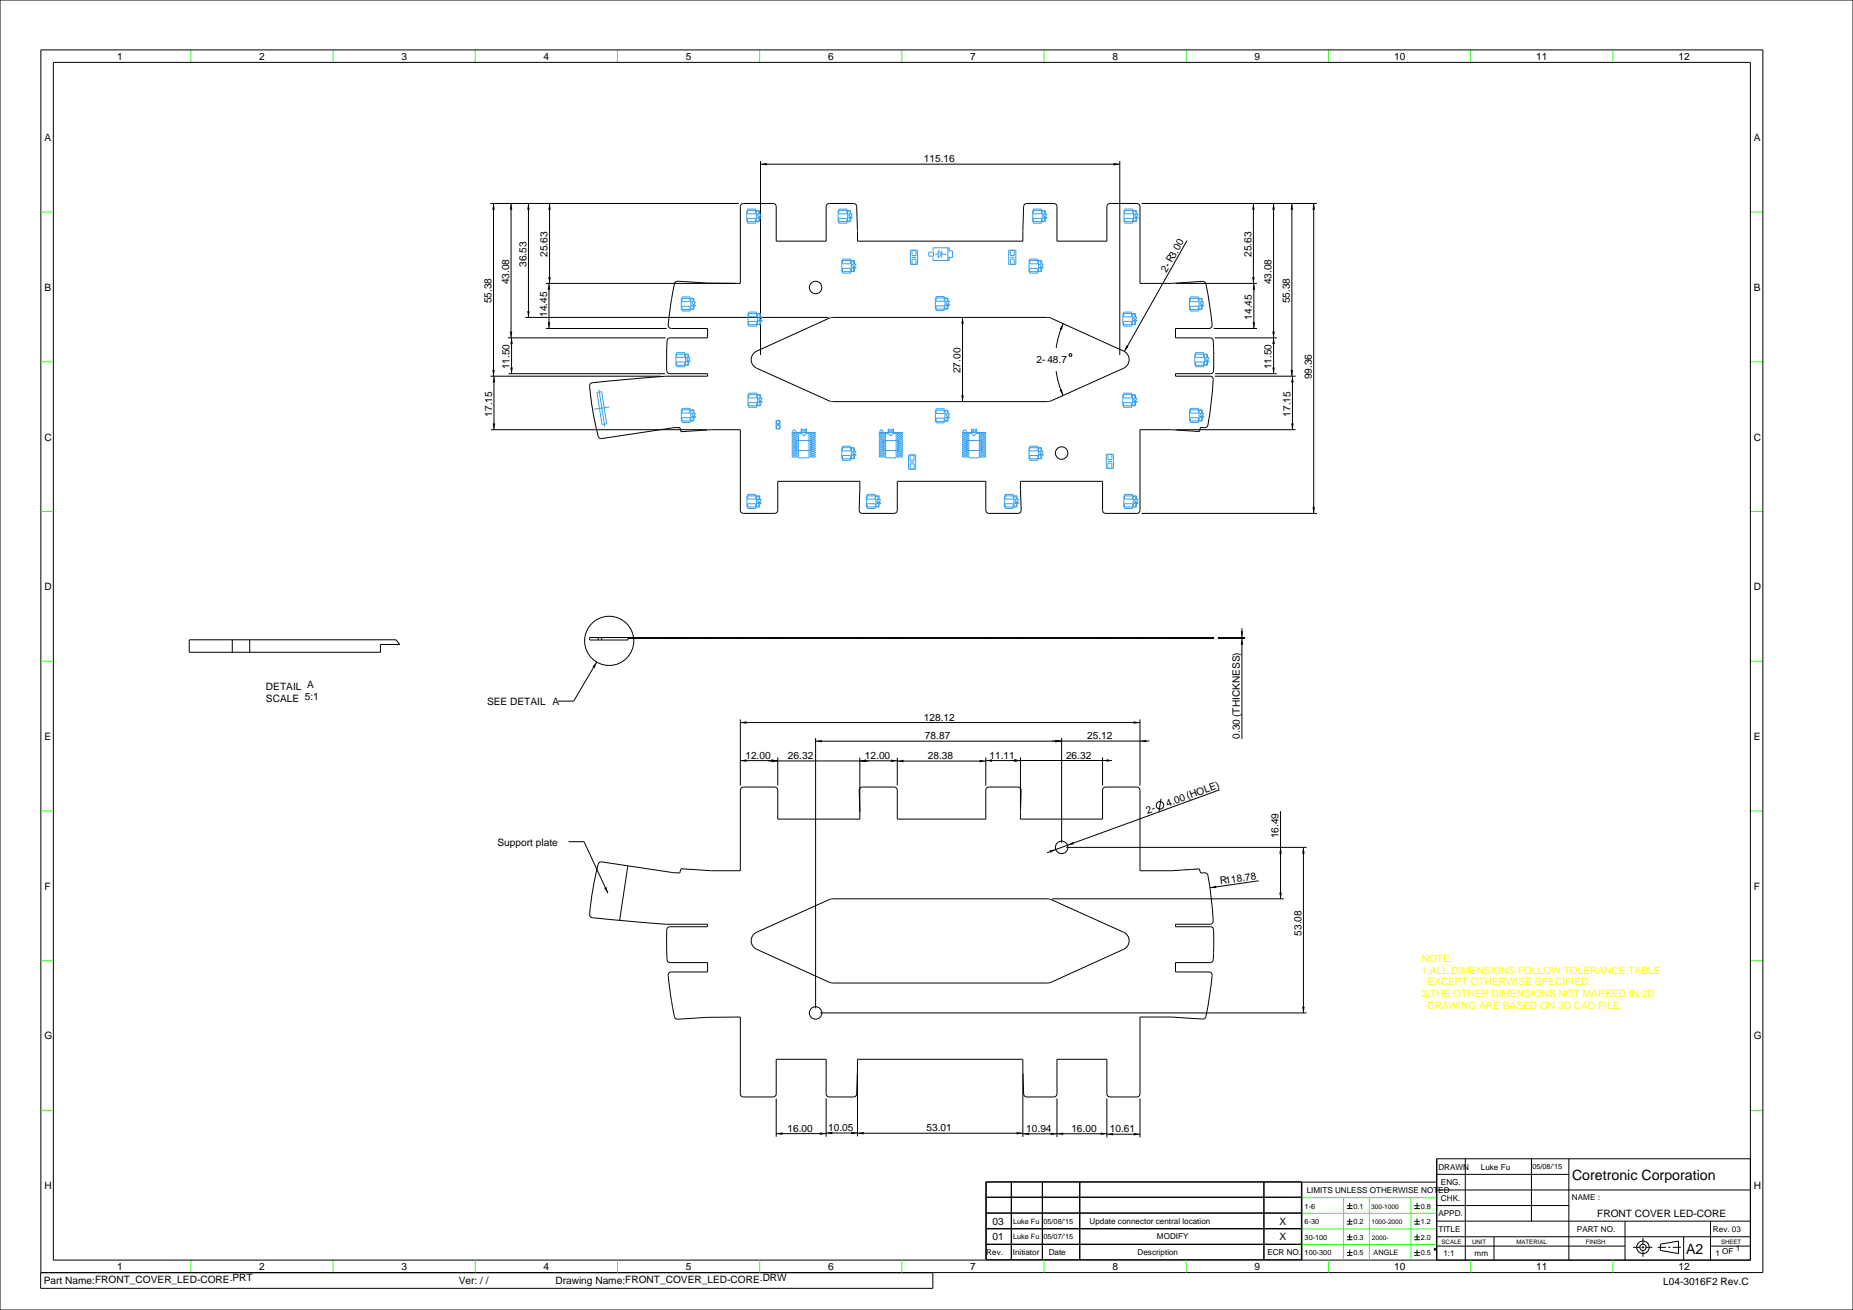
[picture p89: page 1]
ANGLE; L04-3016F2 Rev.C; (THICKNESS) 0.30; (HOLE) 4.00; Rev.; Initiator; Date; Description; ECR NO.; DRAWN Luke Fu; Part Name:FRONT_COVER_LED-CORE.PRT; Ver: / /; Drawing Name:FRONT_COVER_LED-CORE.DRW; SEE DETAIL A; Support plate; DETAIL A SCALE 5:1

NOTE:
1.ALL DIMENSIONS FOLLOW TOLERANCE TABLE
EXCEPT OTHERWISE SPECIFIED.
2.THE OTHER DIMENSIONS NOT MARKED IN 2D
DRAWING ARE BASED ON 3D CAD FILE.

Coretronic Corporation ENG.

LIMITS UNLESS OTHERWISE NOTED
1-6 | | | 300-1000

CHK. | | | NAME : FRONT COVER LED-CORE
APPD.
TITLE | | PART NO. | | Rev. 03
SCALE | UNIT | MATERIAL | FINISH | | SHEET

03 | Luke Fu | 05/08/'15 | Update connector central location | X | 6-30 | 1000-2000
01 | Luke Fu | 05/07/'15 | MODIFY | X | 30-100 | 2000-

Made By Willy Tsai 88/3/8
