OSVR/OSVR-HDK/HDK Ver 1.2/electricals/schematics/DVT IR_PCB_BACK_photodiode_0524.pdf

# TO HMD

# Back IR Module (photodiode *1)

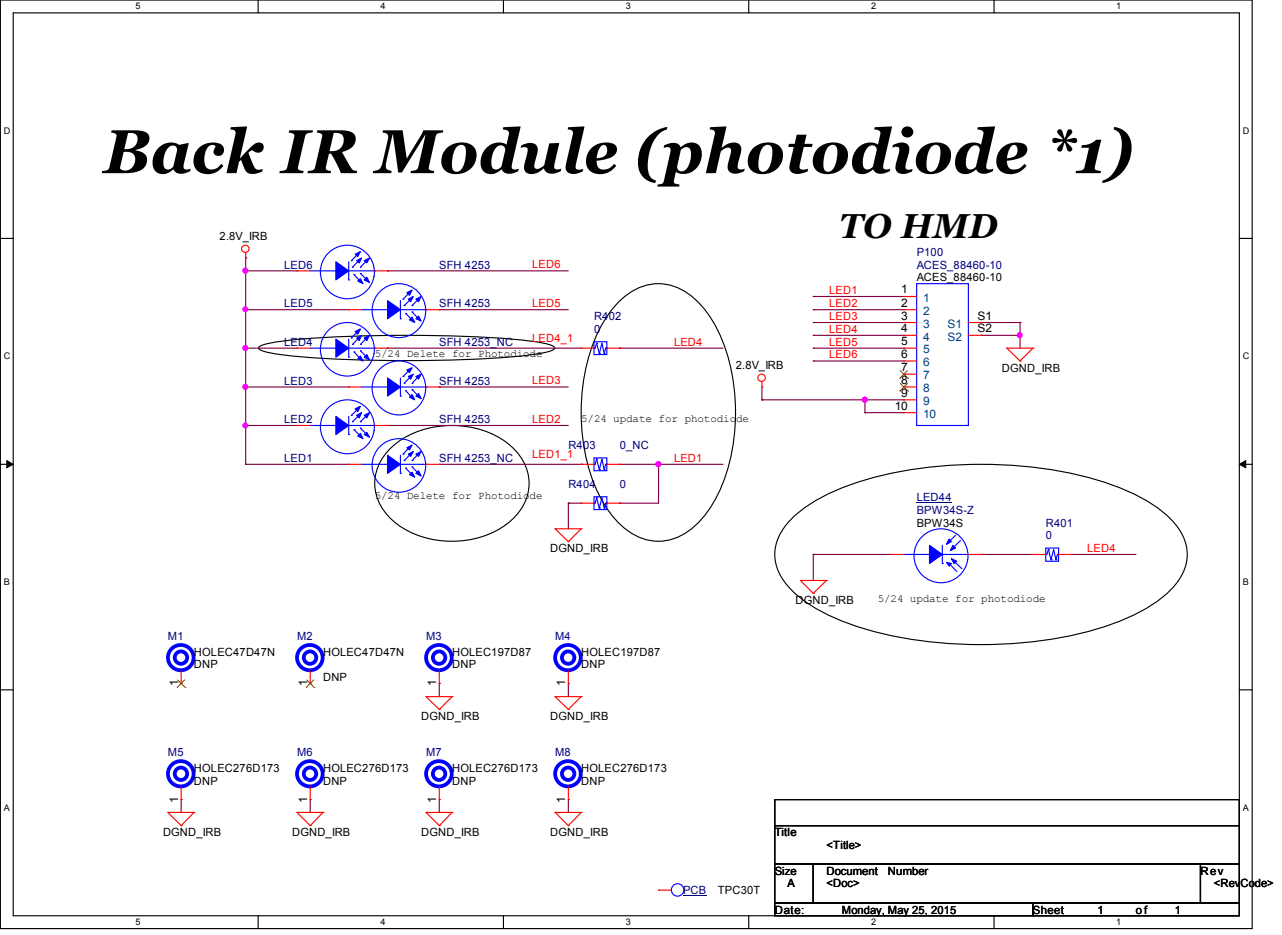
[picture p90: page 1]
