OSVR/OSVR-HDK/HDK Ver 1.1/electronics/hmd-c-gbr-all/Hmd-impedance-pdf/hmd-impedance.pdf

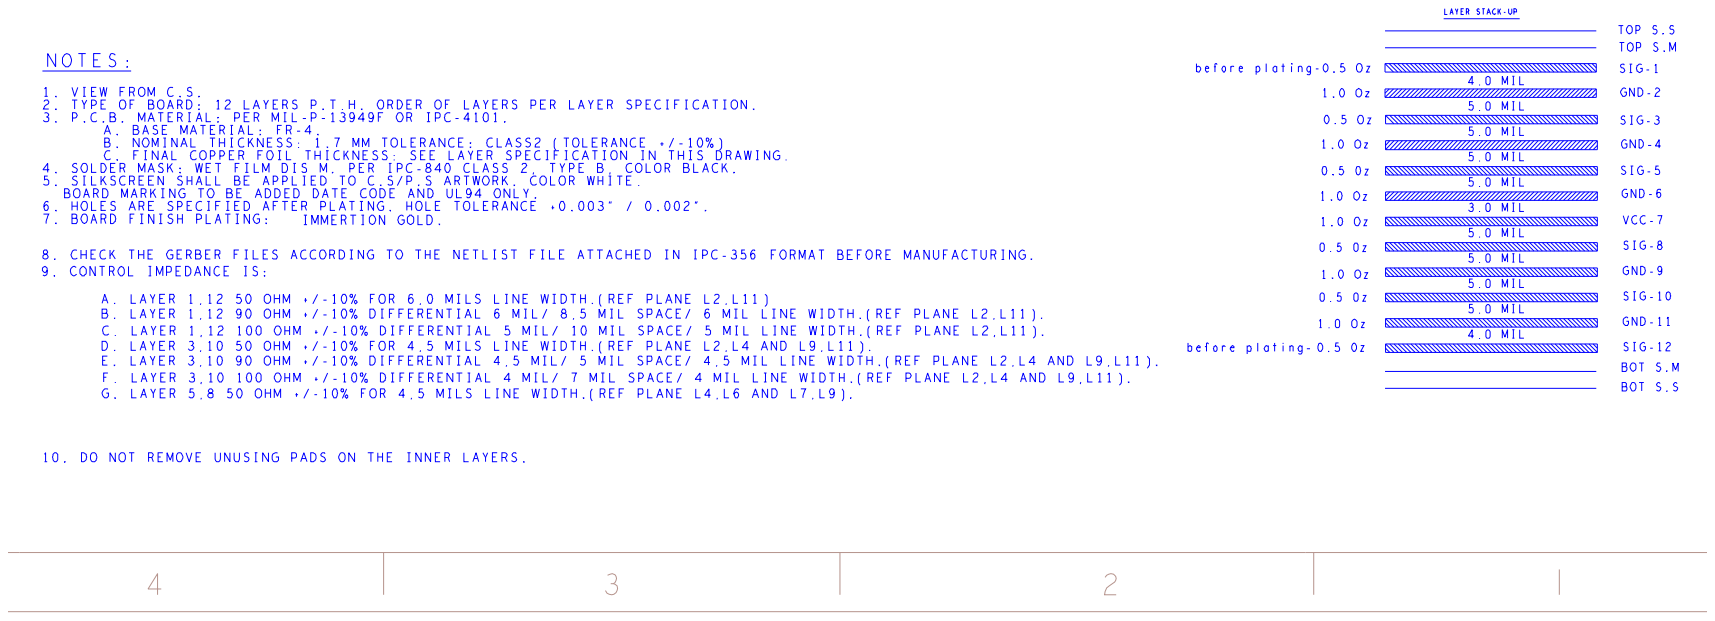
[picture p91: page 1]
