OSVR/OSVR-HDK/HDK Ver 1.1/electronics/belt_box-002-all/belt_box-002-gbr-all/belt_box-002_impedance/belt_box-impedance-bot.pdf

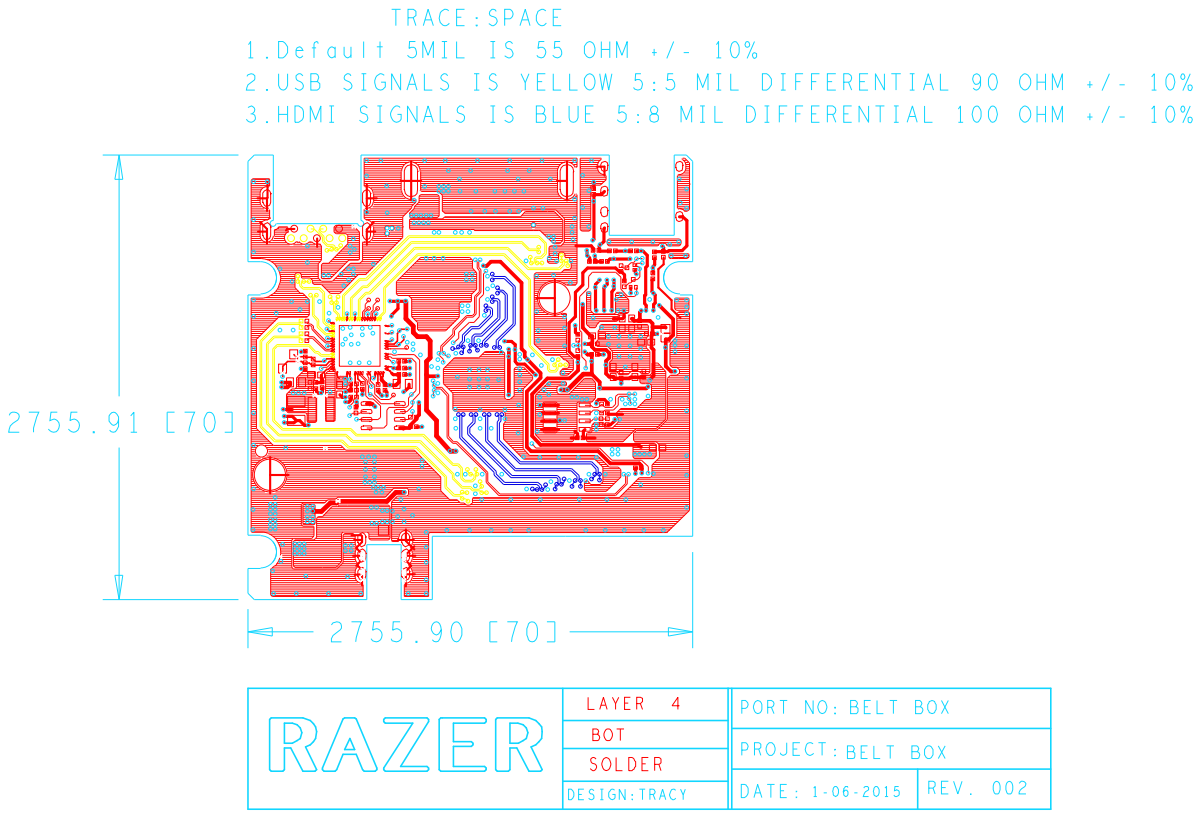
[picture p92: page 1]
