OSVR/OSVR-HDK/HDK Ver 1.1/electronics/display-sharp-002-all/display-002-gbr-all/dispaly-002-impedance/dispaly-impedance-top.pdf

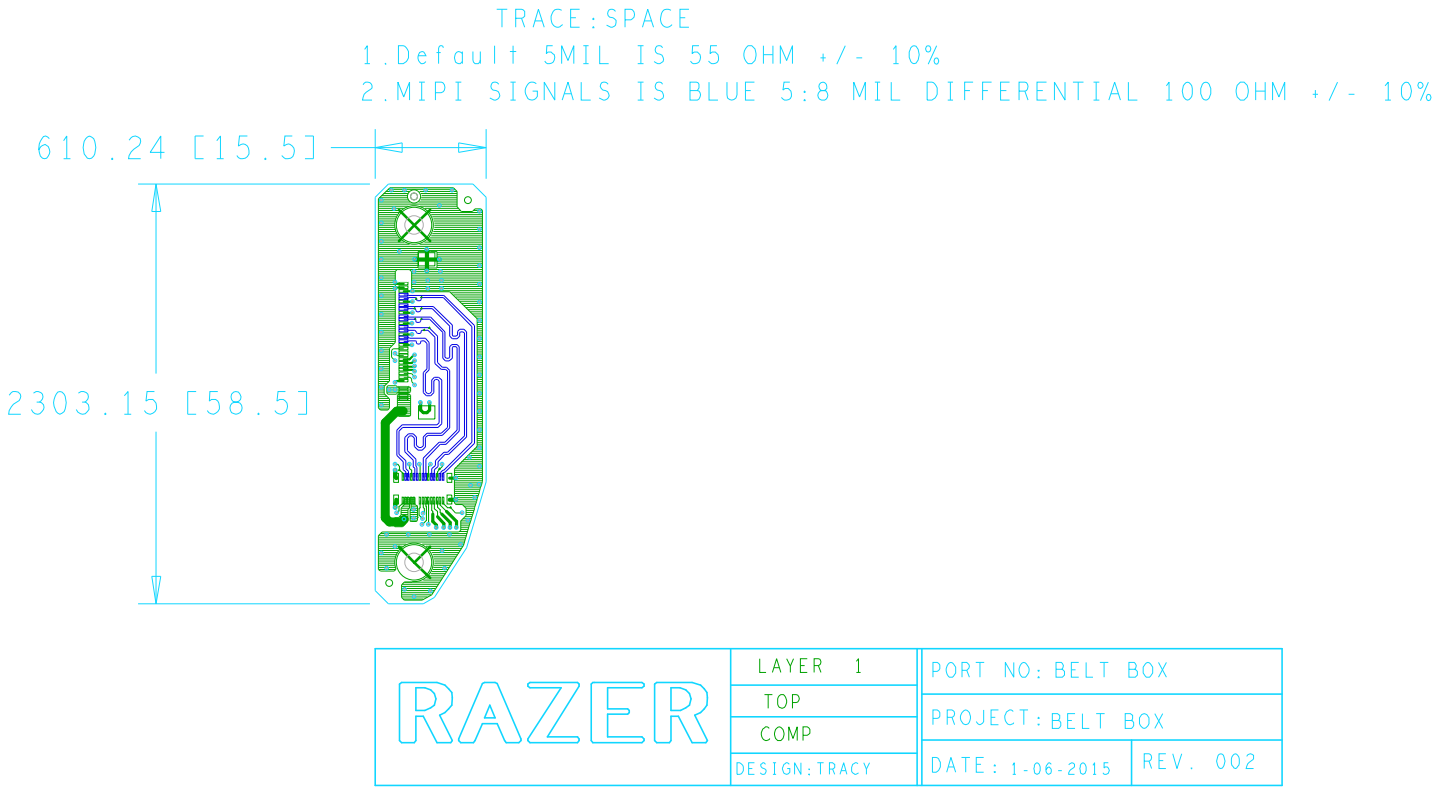
[picture p94: page 1]
