OSVR/OSVR-HDK/HDK Ver 1.1/electronics/usb-001-120-all/usb-001-gbr-120-all/usb-001-impedance/usb-impedance-top.pdf

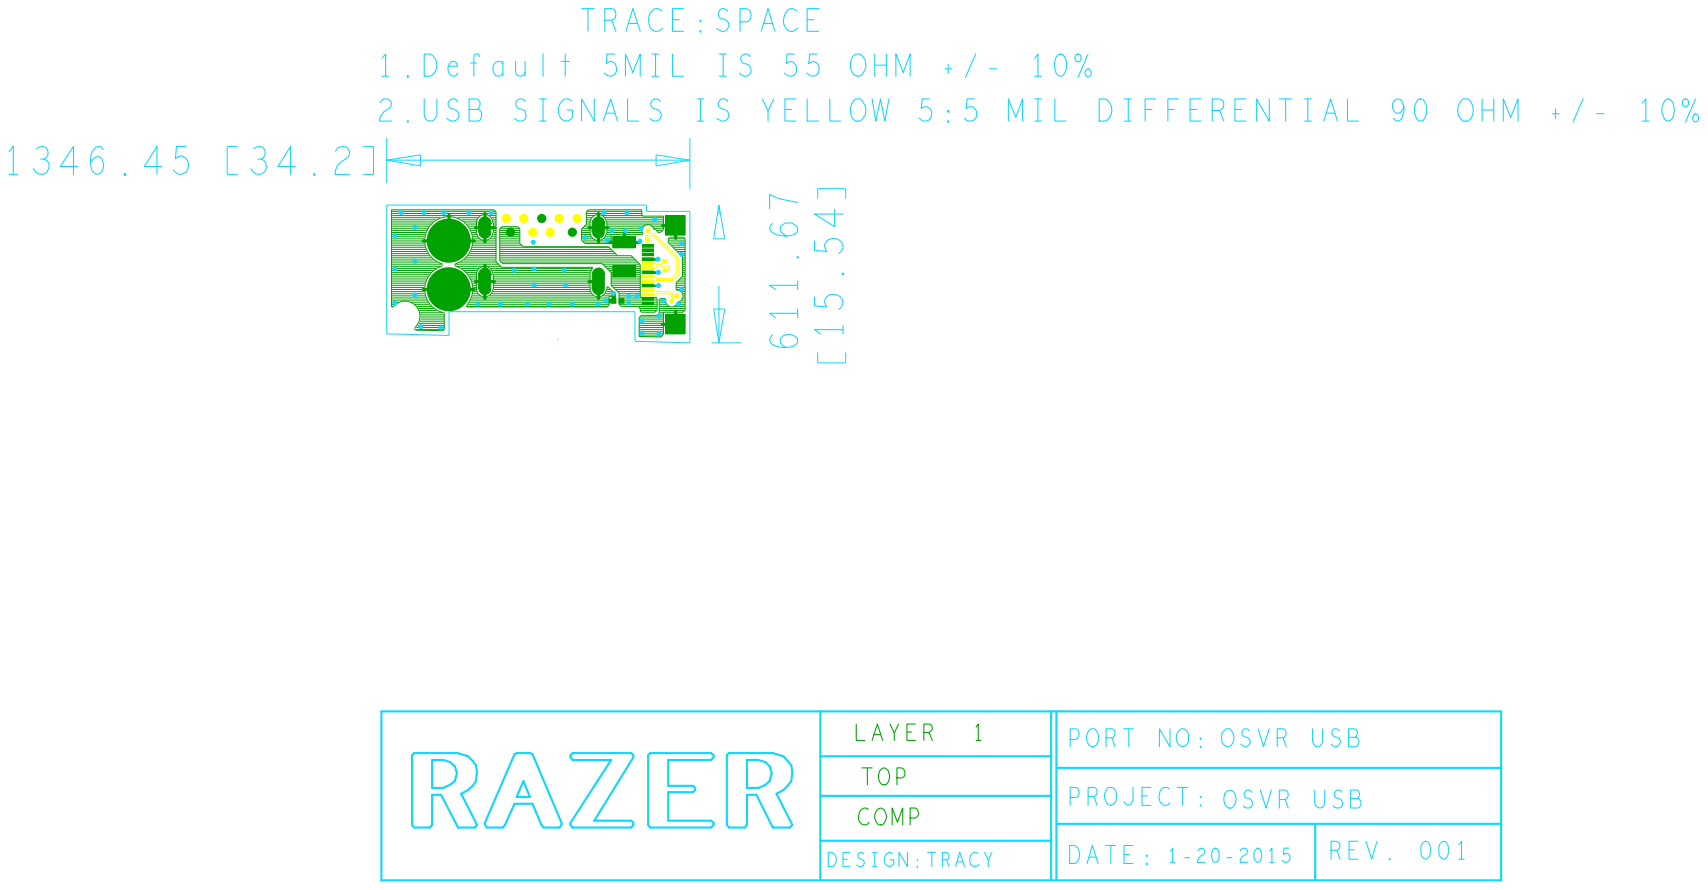
[picture p96: page 1]
