OSVR/OSVR-HDK/HDK Ver 1.1/electronics/usb_fpc-001-all/usb_fpc-001-gbr-all/usb_fpc-impedance/usb_fpc-bot-impedance.pdf

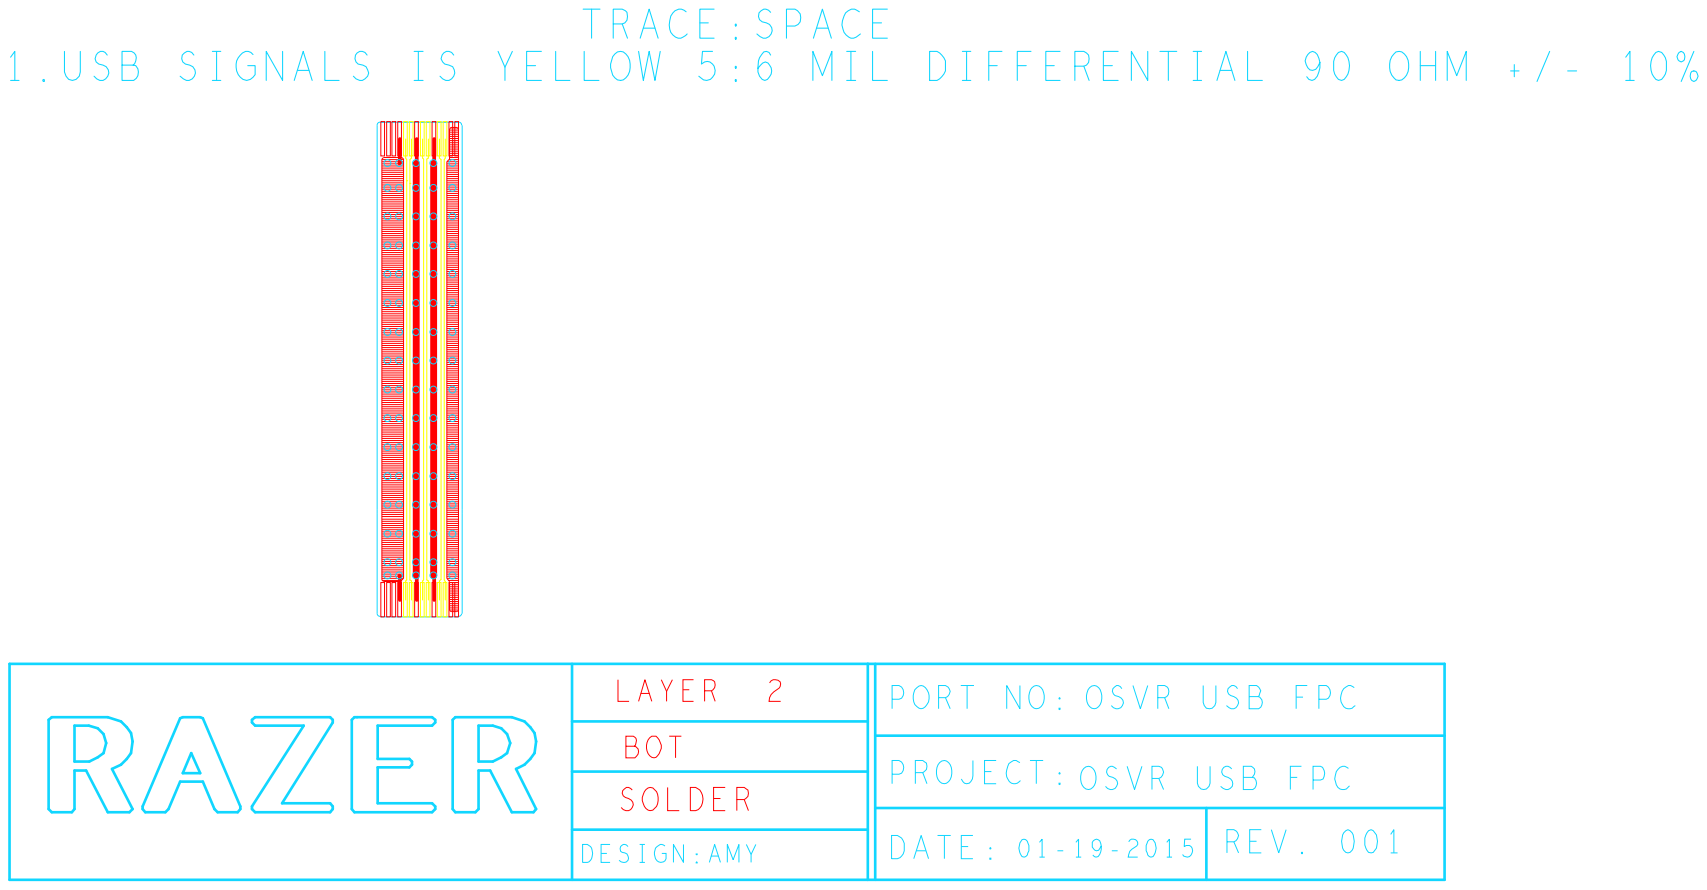
[picture p97: page 1]
