OSVR/OSVR-HDK/HDK Ver 1.2/electricals/gerber/belt-box-dvt3-gbr-0706-all/belt_box-dvt3-impedance/imoedance-bot.pdf

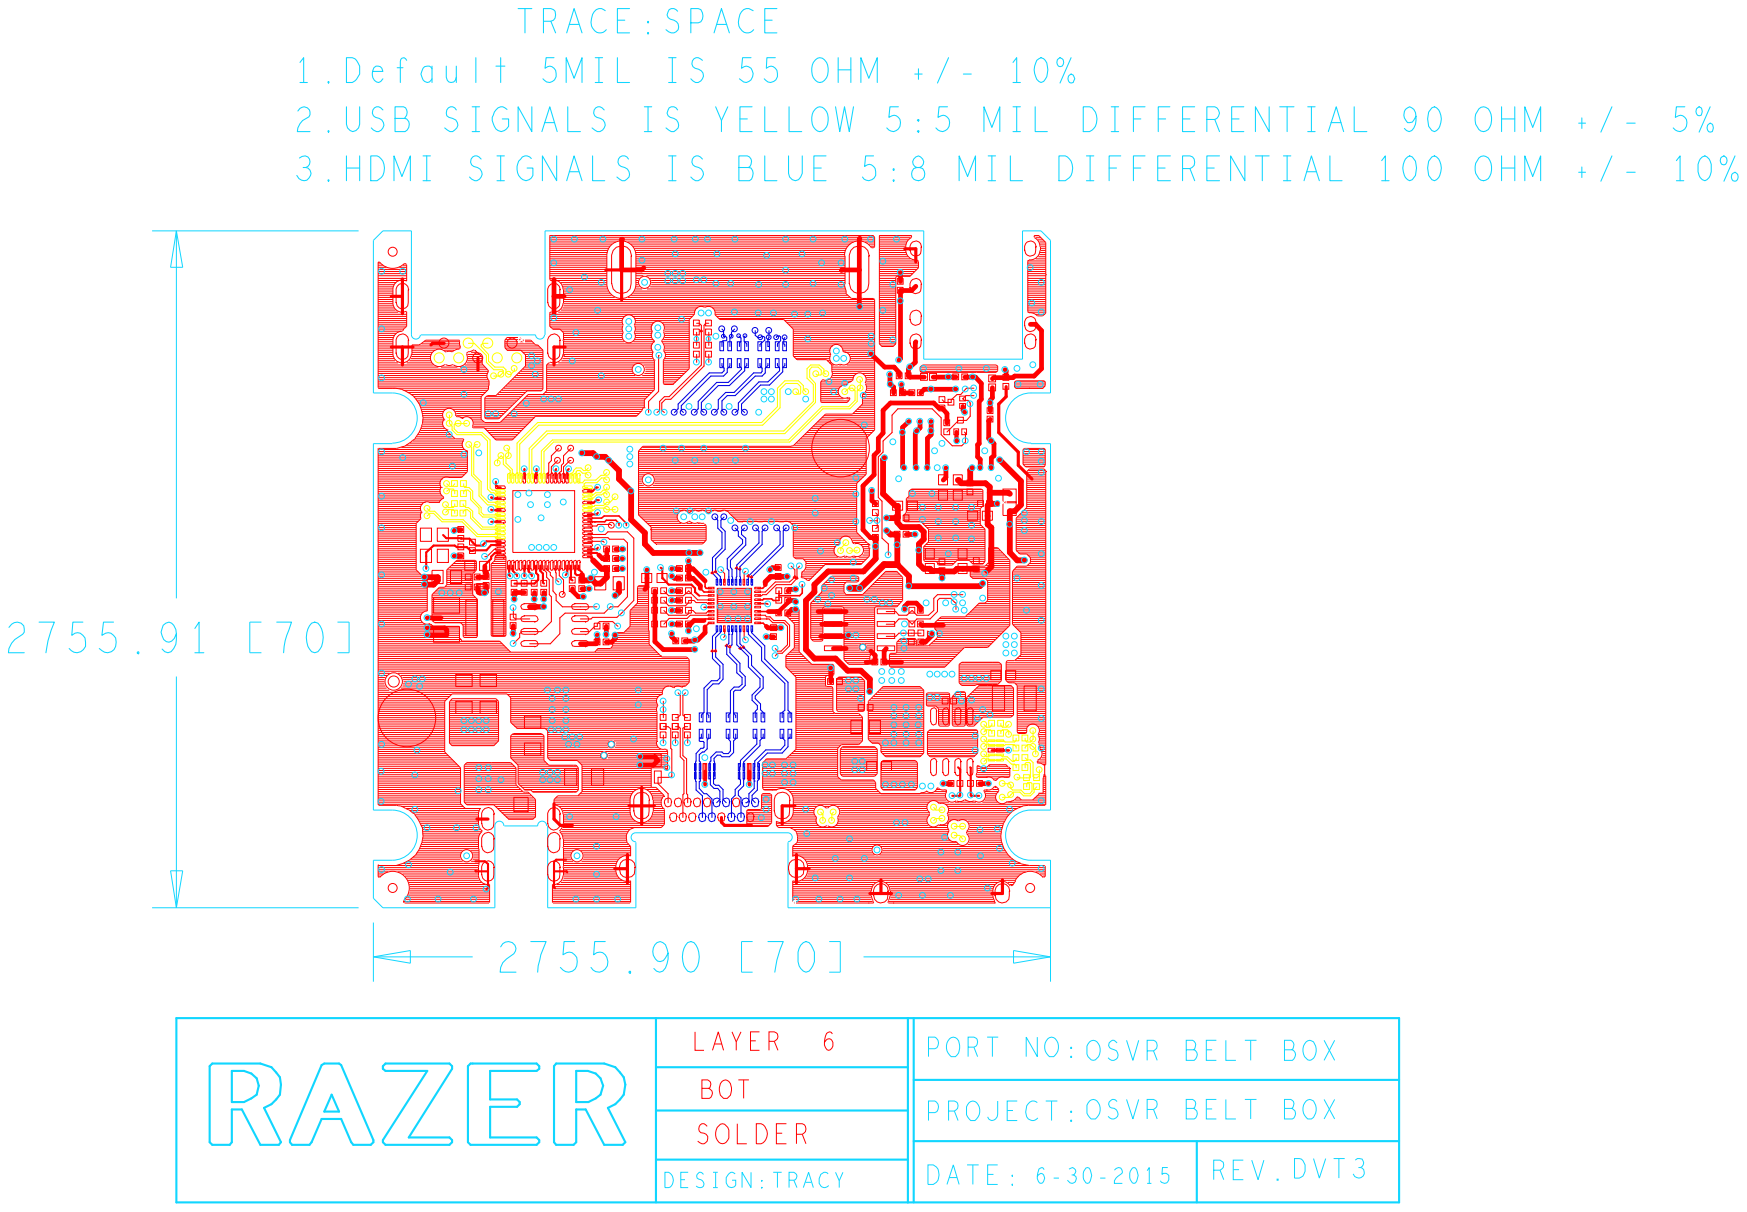
[picture p98: page 1]
